markeby/Synth32/Schematics/3PoleStateVarVCF.kicad_sch

## KiCad design Schematics/3PoleStateVarVCF.kicad_sch (2024-06-07)

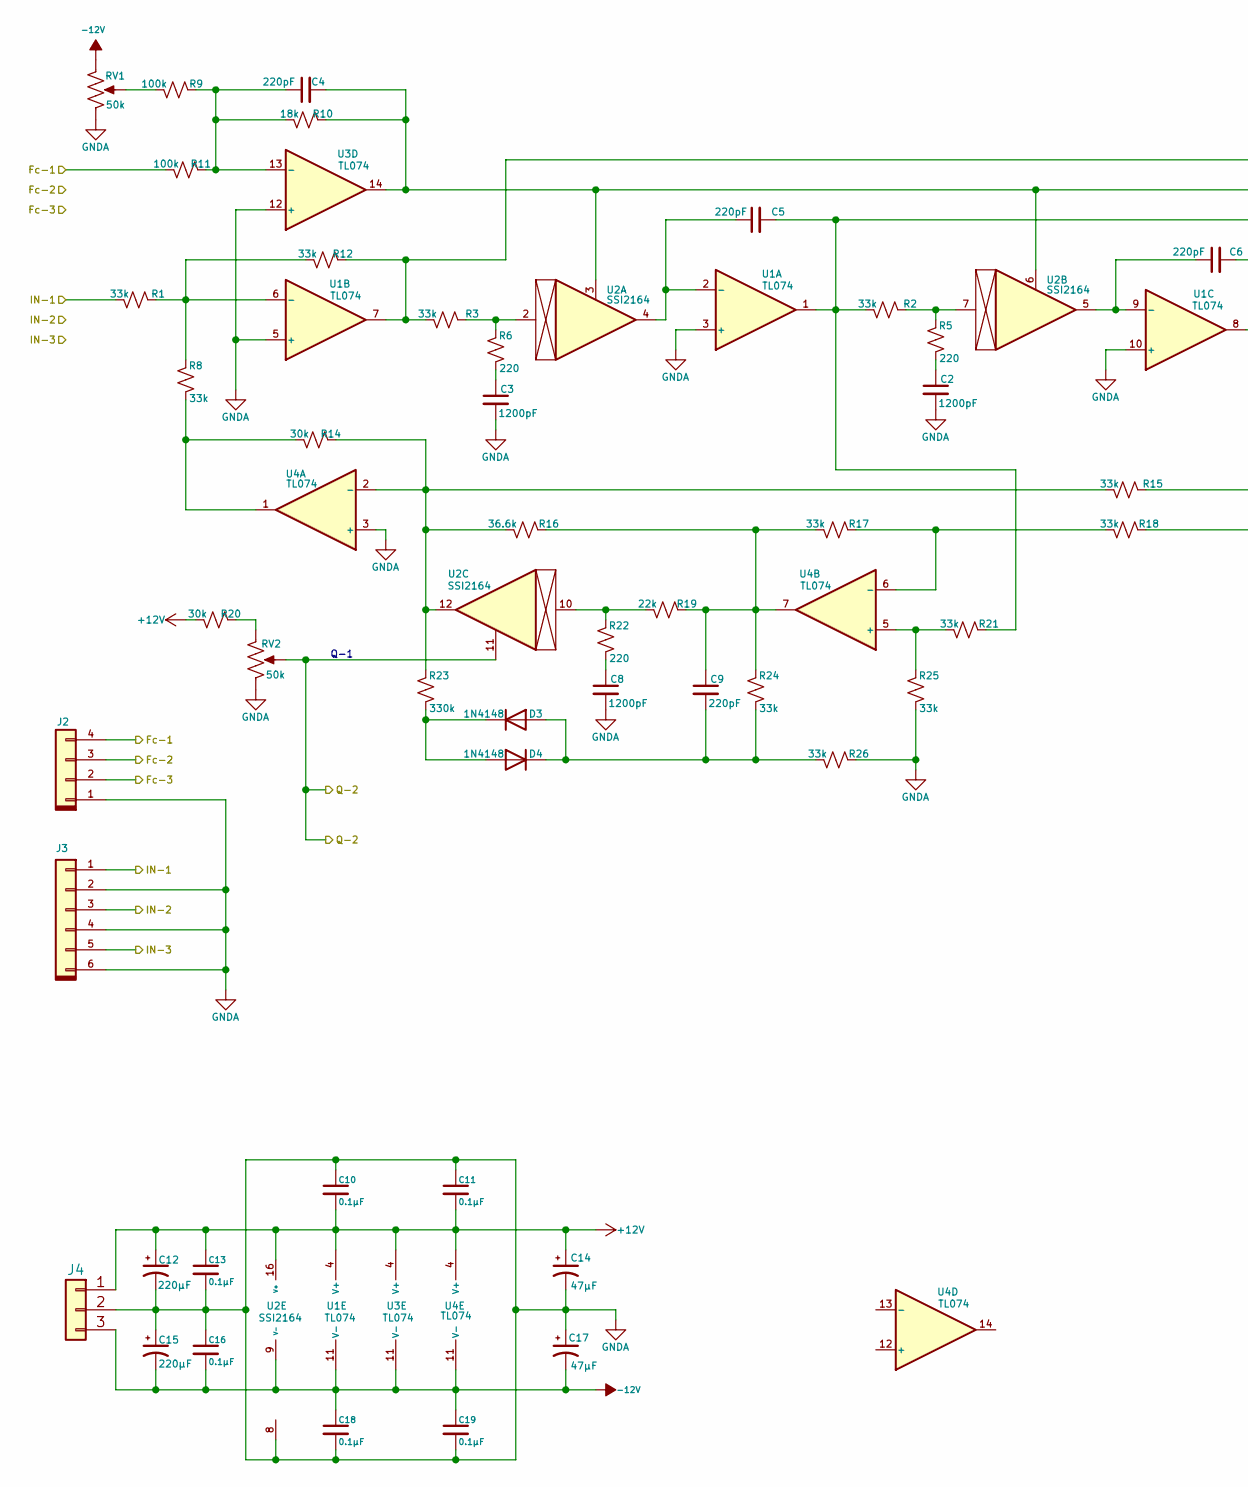
[picture p5: schematic 3PoleStateVarVCF.kicad_sch, part in row 1, column 1]

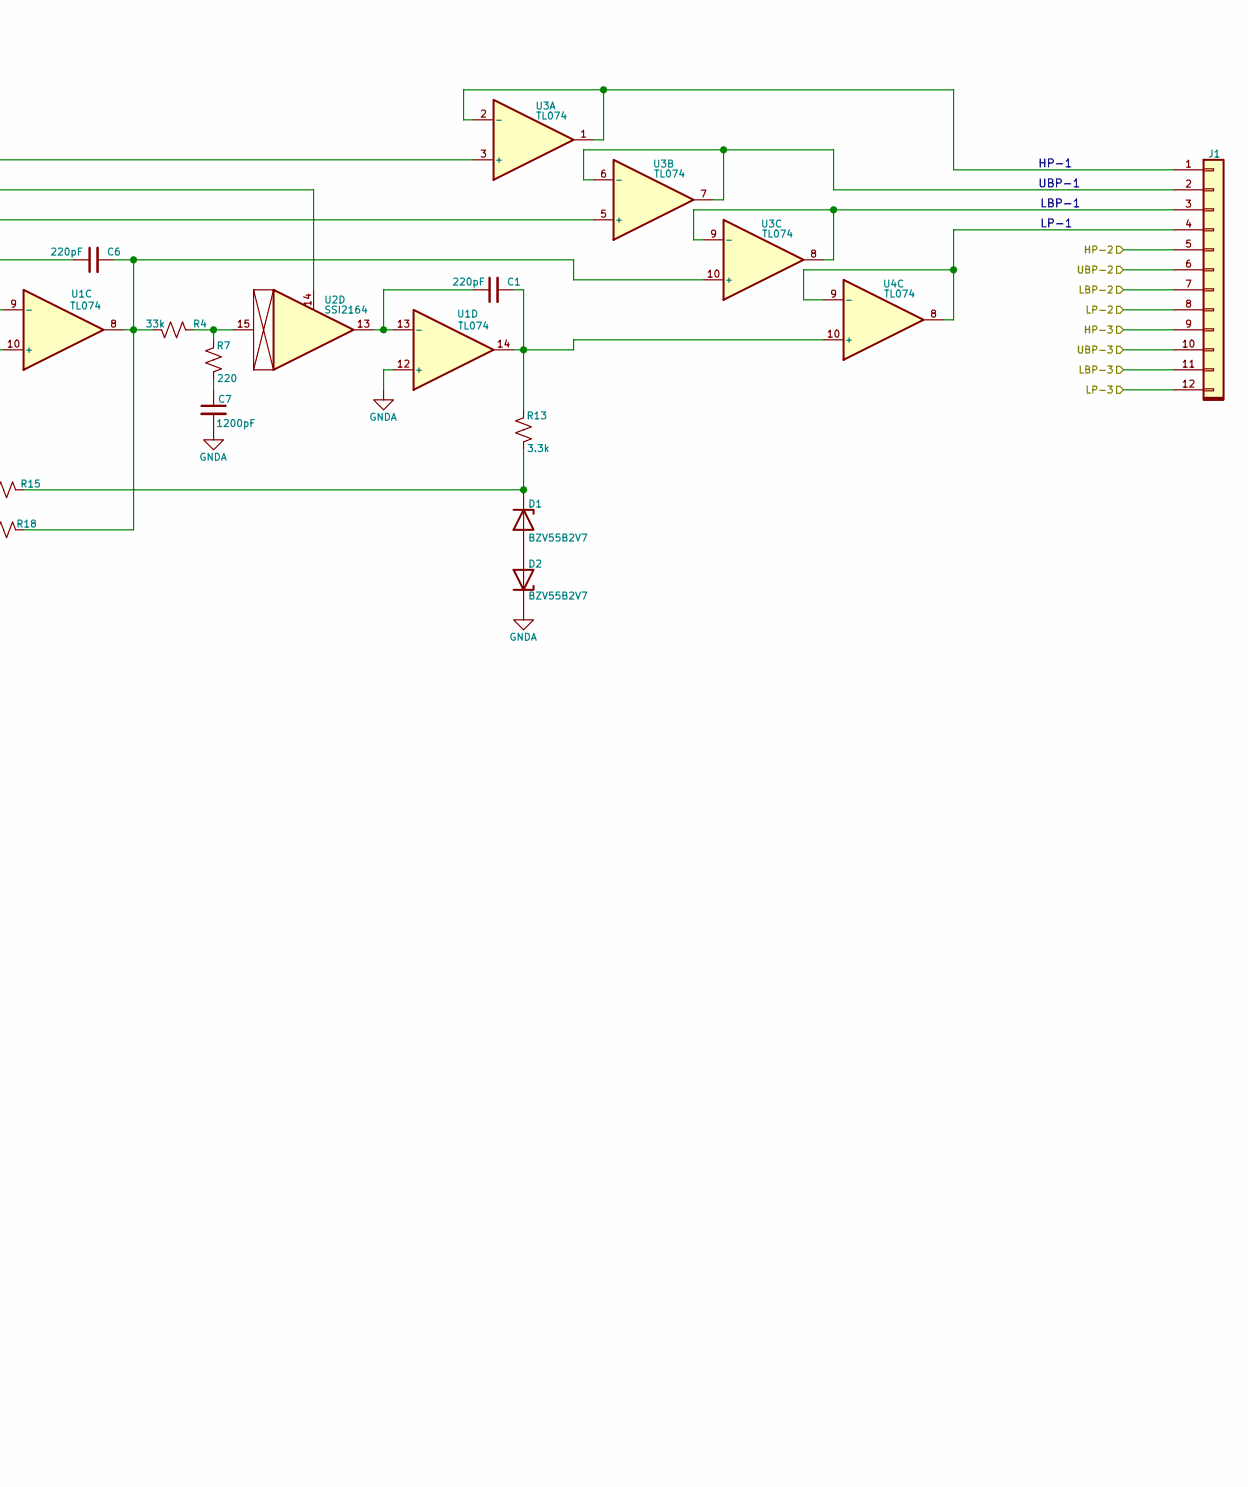
[picture p6: schematic 3PoleStateVarVCF.kicad_sch, part in row 1, column 2]

Parts:
C1, C4, C5, C6, C9: 220pF
C2, C3, C7, C8: 1200pF
C10, C11, C13, C16, C18, C19: 0.1µF
C12, C15: 220µF
C14, C17: 47µF
D1, D2: BZV55B2V7; D_MiniMELF
D3, D4: 1N4148; D_SOD-123
J1: Conn_01x12
J2: Conn_01x04
J3: Conn_01x06
J4: Conn_01x03
R1, R2, R3, R4, R8, R12, R15, R17, R18, R21, R24, R25, R26: 33k
R5, R6, R7, R22: 220
R9, R11: 100k
R10: 18k
R13: 3.3k
R14, R20: 30k
R16: 36.6k
R19: 22k
R23: 330k
RV1, RV2: 50k
U1, U3, U4: TL074
U2: SSI2164

Connections:
+12V: C10.2, C11.2, C12.1, C13.1, C14.1, J4.1, R20.2, U1.4 (V+), U2.16 (V+), U3.4 (V+), U4.4 (V+)
-12V: C15.2, C16.2, C17.2, C18.1, C19.1, J4.3, RV1., U1.11 (V-), U2.9 (V-), U3.11 (V-), U4.11 (V-)
Fc-1: J2.4, R11.2
Fc-2: J2.3
Fc-3: J2.2
GNDA: C2.2, C3.2, C7.2, C8.2, C10.1, C11.1, C12.2, C13.2, C14.2, C15.1, C16.1, C17.1, C18.2, C19.2, D2.1 (K), J2.1, J3.2, J3.4, J3.6, J4.2, R25.2, R26.1, RV1., RV2., U1.3 (+), U1.5 (+), U1.10 (+), U1.12 (+), U2.8, U3.12 (+), U4.3 (+)
HP-2: J1.5
HP-3: J1.9
IN-1: J3.1, R1.2
IN-2: J3.3
IN-3: J3.5
LBP-2: J1.7
LBP-3: J1.11
LP-2: J1.8
LP-3: J1.12
unnamed: C1.1, U1.13 (-), U2.13
unnamed: C1.2, R13.1, U1.14, U4.10 (+)
unnamed: C2.1, R5.2
unnamed: C3.1, R6.2
unnamed: C4.1, R9.1, R10.2, R11.1, U3.13 (-)
unnamed: C4.2, R10.1, U2.3, U2.6, U2.14, U3.14
unnamed: C5.1, U1.2 (-), U2.4
unnamed: C5.2, R2.2, R21.1, U1.1, U3.5 (+)
unnamed: C6.1, U1.9 (-), U2.5
unnamed: C6.2, R4.2, R18.1, U1.8, U3.10 (+)
unnamed: C7.1, R7.2
unnamed: C8.1, R22.2
unnamed: C9.1, R16.1, R17.2, R19.1, R24.1, U4.7
unnamed: C9.2, D3.2 (A), D4.1 (K), R24.2, R26.2
unnamed: D1.1 (K), R13.2, R15.1
unnamed: D1.2 (A), D2.2 (A)
unnamed: D3.1 (K), D4.2 (A), R23.2
unnamed: J1.1, U3.1, U3.2 (-)
unnamed: J1.2, U3.6 (-), U3.7
unnamed: J1.3, U3.8, U3.9 (-)
unnamed: J1.4, U4.8, U4.9 (-)
unnamed: R1.1, R8.1, R12.2, U1.6 (-)
unnamed: R2.1, R5.1, U2.7
unnamed: R3.1, R6.1, U2.2
unnamed: R4.1, R7.1, U2.15
unnamed: R9.2, RV1.
unnamed: R3.2, R12.1, U1.7, U3.3 (+)
unnamed: R14.1, R15.2, R16.2, R23.1, U2.12, U4.2 (-)
unnamed: R8.2, R14.2, U4.1
unnamed: R17.1, R18.2, U4.6 (-)
unnamed: R19.2, R22.1, U2.10
unnamed: R20.1, RV2.
unnamed: R21.2, R25.1, U4.5 (+)
Q-2: RV2., U2.11
UBP-2: J1.6
UBP-3: J1.10

Notes on the sheet:
LP-1
UBP-1
LBP-1
HP-1
Q-1
