markeby/Synth32/Schematics/Analog-1.kicad_sch

## KiCad design Schematics/Analog-1.kicad_sch (2024-10-31)

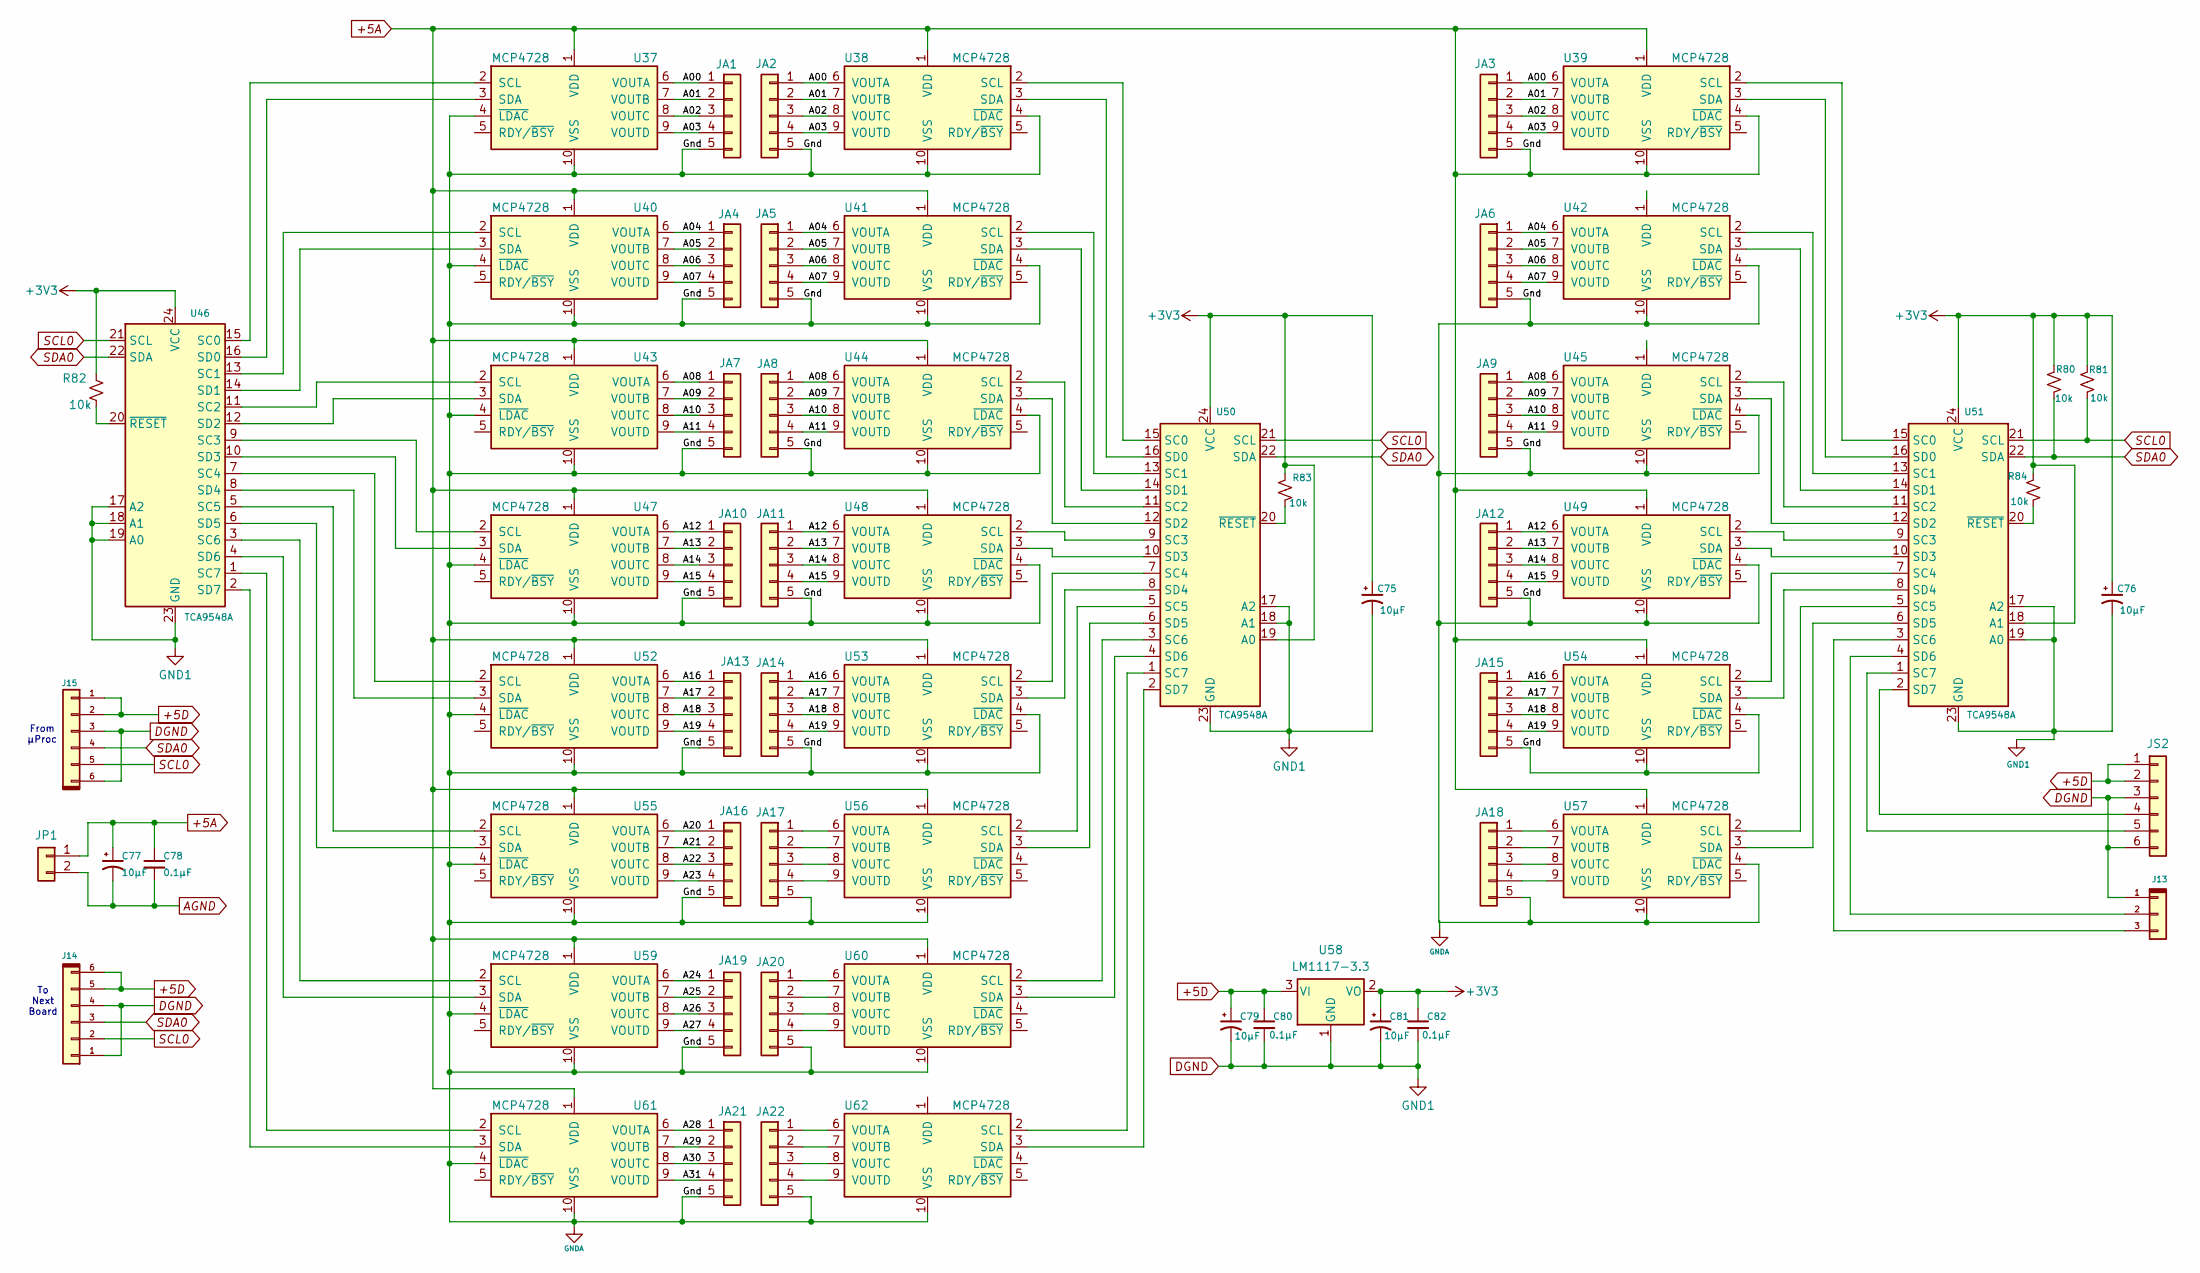
[picture p7: schematic Analog-1.kicad_sch]

Parts:
C75, C76, C77, C79, C81: 10µF
C78, C80, C82: 0.1µF
J13: Conn_01x03
J14, J15: Conn_01x06
JA1, JA2, JA3: DA00
JA4, JA5, JA6: DA04
JA7, JA8, JA9: DA08
JA10, JA11, JA12: DA12
JA13, JA14, JA15, JA17, JA18, JA20, JA22: DA16
JA16: DA20
JA19: DA24
JA21: DA38
JP1: From 12v Analog
JS2: To Compute #1
R80, R81, R82, R83, R84: 10k
U37, U38, U39, U40, U41, U42, U43, U44, U45, U47, U48, U49, U52, U53, U54, U55, U56, U57, U59, U60, U61, U62: MCP4728; MSOP-10_3x3mm_P0.5mm
U46, U50, U51: TCA9548A; SOIC-24W_7.5x15.4mm_P1.27mm
U58: LM1117-3.3

Connections:
+3V3: C75.1, C76.1, C81.1, C82.1, R80.1, R81.1, R82.1, R83.1, R84.1, U46.24 (VCC), U50.19 (A0), U50.24 (VCC), U51.18 (A1), U51.24 (VCC), U58.2 (VO)
+5A: C77.1, C78.1, JA1.5, JA2.5, JA3.5, JA4.5, JA5.5, JA6.5, JA7.5, JA8.5, JA9.5, JA10.5, JA11.5, JA12.5, JA13.5, JA14.5, JA15.5, JA16.5, JA17.5, JA18.5, JA19.5, JA20.5, JA21.5, JA22.5, JP1.1, U37.1 (VDD), U37.4 (~LDAC), U37.10 (VSS), U38.1 (VDD), U38.4 (~LDAC), U38.10 (VSS), U39.1 (VDD), U39.4 (~LDAC), U39.10 (VSS), U40.1 (VDD), U40.4 (~LDAC), U40.10 (VSS), U41.1 (VDD), U41.4 (~LDAC), U41.10 (VSS), U42.4 (~LDAC), U42.10 (VSS), U43.1 (VDD), U43.4 (~LDAC), U43.10 (VSS), U44.1 (VDD), U44.4 (~LDAC), U44.10 (VSS), U45.4 (~LDAC), U45.10 (VSS), U47.1 (VDD), U47.4 (~LDAC), U47.10 (VSS), U48.1 (VDD), U48.4 (~LDAC), U48.10 (VSS), U49.1 (VDD), U49.4 (~LDAC), U49.10 (VSS), U52.1 (VDD), U52.4 (~LDAC), U52.10 (VSS), U53.1 (VDD), U53.4 (~LDAC), U53.10 (VSS), U54.1 (VDD), U54.4 (~LDAC), U54.10 (VSS), U55.1 (VDD), U55.4 (~LDAC), U55.10 (VSS), U56.1 (VDD), U56.10 (VSS), U57.1 (VDD), U57.4 (~LDAC), U57.10 (VSS), U59.1 (VDD), U59.4 (~LDAC), U59.10 (VSS), U60.1 (VDD), U60.10 (VSS), U61.1 (VDD), U61.4 (~LDAC), U61.10 (VSS), U62.10 (VSS)
+5D: C79.1, C80.1, J14.5, J14.6, J15.1, J15.2, JS2.1, JS2.2, U58.3 (VI)
A00: JA1.1, JA2.1, JA3.1, U37.6 (VOUTA), U38.6 (VOUTA), U39.6 (VOUTA)
A01: JA1.2, JA2.2, JA3.2, U37.7 (VOUTB), U38.7 (VOUTB), U39.7 (VOUTB)
A02: JA1.3, JA2.3, JA3.3, U37.8 (VOUTC), U38.8 (VOUTC), U39.8 (VOUTC)
A03: JA1.4, JA2.4, JA3.4, U37.9 (VOUTD), U38.9 (VOUTD), U39.9 (VOUTD)
A04: JA4.1, JA5.1, JA6.1, U40.6 (VOUTA), U41.6 (VOUTA), U42.6 (VOUTA)
A05: JA4.2, JA5.2, JA6.2, U40.7 (VOUTB), U41.7 (VOUTB), U42.7 (VOUTB)
A06: JA4.3, JA5.3, JA6.3, U40.8 (VOUTC), U41.8 (VOUTC), U42.8 (VOUTC)
A07: JA4.4, JA5.4, JA6.4, U40.9 (VOUTD), U41.9 (VOUTD), U42.9 (VOUTD)
A08: JA7.1, JA8.1, JA9.1, U43.6 (VOUTA), U44.6 (VOUTA), U45.6 (VOUTA)
A09: JA7.2, JA8.2, JA9.2, U43.7 (VOUTB), U44.7 (VOUTB), U45.7 (VOUTB)
A10: JA7.3, JA8.3, JA9.3, U43.8 (VOUTC), U44.8 (VOUTC), U45.8 (VOUTC)
A11: JA7.4, JA8.4, JA9.4, U43.9 (VOUTD), U44.9 (VOUTD), U45.9 (VOUTD)
A12: JA10.1, JA11.1, JA12.1, U47.6 (VOUTA), U48.6 (VOUTA), U49.6 (VOUTA)
A13: JA10.2, JA11.2, JA12.2, U47.7 (VOUTB), U48.7 (VOUTB), U49.7 (VOUTB)
A14: JA10.3, JA11.3, JA12.3, U47.8 (VOUTC), U48.8 (VOUTC), U49.8 (VOUTC)
A15: JA10.4, JA11.4, JA12.4, U47.9 (VOUTD), U48.9 (VOUTD), U49.9 (VOUTD)
A16: JA13.1, JA14.1, JA15.1, U52.6 (VOUTA), U53.6 (VOUTA), U54.6 (VOUTA)
A17: JA13.2, JA14.2, JA15.2, U52.7 (VOUTB), U53.7 (VOUTB), U54.7 (VOUTB)
A18: JA13.3, JA14.3, JA15.3, U52.8 (VOUTC), U53.8 (VOUTC), U54.8 (VOUTC)
A19: JA13.4, JA14.4, JA15.4, U52.9 (VOUTD), U53.9 (VOUTD), U54.9 (VOUTD)
A20: JA16.1, U55.6 (VOUTA)
A21: JA16.2, U55.7 (VOUTB)
A22: JA16.3, U55.8 (VOUTC)
A23: JA16.4, U55.9 (VOUTD)
A24: JA19.1, U59.6 (VOUTA)
A25: JA19.2, U59.7 (VOUTB)
A26: JA19.3, U59.8 (VOUTC)
A27: JA19.4, U59.9 (VOUTD)
A28: JA21.1, U61.6 (VOUTA)
A29: JA21.2, U61.7 (VOUTB)
A30: JA21.3, U61.8 (VOUTC)
A31: JA21.4, U61.9 (VOUTD)
AGND: C77.2, C78.2, JP1.2
DGND: C75.2, C76.2, C79.2, C80.2, C81.2, C82.2, J13.1, J14.1, J14.4, J15.3, J15.6, JS2.3, JS2.6, U46.17 (A2), U46.18 (A1), U46.19 (A0), U46.23 (GND), U50.17 (A2), U50.18 (A1), U50.23 (GND), U51.17 (A2), U51.19 (A0), U51.23 (GND), U58.1 (GND)
unnamed: J13.2, U51.4 (SD6)
unnamed: J13.3, U51.3 (SC6)
unnamed: JA17.1, U56.6 (VOUTA)
unnamed: JA17.2, U56.7 (VOUTB)
unnamed: JA17.3, U56.8 (VOUTC)
unnamed: JA17.4, U56.9 (VOUTD)
unnamed: JA18.1, U57.6 (VOUTA)
unnamed: JA18.2, U57.7 (VOUTB)
unnamed: JA18.3, U57.8 (VOUTC)
unnamed: JA18.4, U57.9 (VOUTD)
unnamed: JA20.1, U60.6 (VOUTA)
unnamed: JA20.2, U60.7 (VOUTB)
unnamed: JA20.3, U60.8 (VOUTC)
unnamed: JA20.4, U60.9 (VOUTD)
unnamed: JA22.1, U62.6 (VOUTA)
unnamed: JA22.2, U62.7 (VOUTB)
unnamed: JA22.3, U62.8 (VOUTC)
unnamed: JA22.4, U62.9 (VOUTD)
unnamed: JS2.4, U51.2 (SD7)
unnamed: JS2.5, U51.1 (SC7)
unnamed: R82.2, U46.20 (~RESET)
unnamed: R83.2, U50.20 (~RESET)
unnamed: R84.2, U51.20 (~RESET)
unnamed: U37.2 (SCL), U46.15 (SC0)
unnamed: U37.3 (SDA), U46.16 (SD0)
unnamed: U38.2 (SCL), U50.15 (SC0)
unnamed: U38.3 (SDA), U50.16 (SD0)
unnamed: U39.2 (SCL), U51.15 (SC0)
unnamed: U39.3 (SDA), U51.16 (SD0)
unnamed: U40.2 (SCL), U46.13 (SC1)
unnamed: U40.3 (SDA), U46.14 (SD1)
unnamed: U41.2 (SCL), U50.13 (SC1)
unnamed: U41.3 (SDA), U50.14 (SD1)
unnamed: U42.2 (SCL), U51.13 (SC1)
unnamed: U42.3 (SDA), U51.14 (SD1)
unnamed: U43.2 (SCL), U46.11 (SC2)
unnamed: U43.3 (SDA), U46.12 (SD2)
unnamed: U44.2 (SCL), U50.11 (SC2)
unnamed: U44.3 (SDA), U50.12 (SD2)
unnamed: U45.2 (SCL), U51.11 (SC2)
unnamed: U45.3 (SDA), U51.12 (SD2)
unnamed: U46.1 (SC7), U61.2 (SCL)
unnamed: U46.2 (SD7), U61.3 (SDA)
unnamed: U46.3 (SC6), U59.2 (SCL)
unnamed: U46.4 (SD6), U59.3 (SDA)
unnamed: U46.5 (SC5), U55.2 (SCL)
unnamed: U46.6 (SD5), U55.3 (SDA)
unnamed: U46.7 (SC4), U52.2 (SCL)
unnamed: U46.8 (SD4), U52.3 (SDA)
unnamed: U46.9 (SC3), U47.2 (SCL)
unnamed: U46.10 (SD3), U47.3 (SDA)
unnamed: U48.2 (SCL), U50.9 (SC3)
unnamed: U48.3 (SDA), U50.10 (SD3)
unnamed: U49.2 (SCL), U51.9 (SC3)
unnamed: U49.3 (SDA), U51.10 (SD3)
unnamed: U50.1 (SC7), U62.2 (SCL)
unnamed: U50.2 (SD7), U62.3 (SDA)
unnamed: U50.3 (SC6), U60.2 (SCL)
unnamed: U50.4 (SD6), U60.3 (SDA)
unnamed: U50.5 (SC5), U56.2 (SCL)
unnamed: U50.6 (SD5), U56.3 (SDA)
unnamed: U50.7 (SC4), U53.2 (SCL)
unnamed: U50.8 (SD4), U53.3 (SDA)
unnamed: U51.5 (SC5), U57.2 (SCL)
unnamed: U51.6 (SD5), U57.3 (SDA)
unnamed: U51.7 (SC4), U54.2 (SCL)
unnamed: U51.8 (SD4), U54.3 (SDA)
SCL0: J14.2, J15.5, R81.2, U46.21 (SCL), U50.21 (SCL), U51.21 (SCL)
SDA0: J14.3, J15.4, R80.2, U46.22 (SDA), U50.22 (SDA), U51.22 (SDA)

Notes on the sheet:
From µProc
To Next Board
