markeby/Synth32/Schematics/DigitalOptical.kicad_sch

## KiCad design Schematics/DigitalOptical.kicad_sch (2024-11-26)

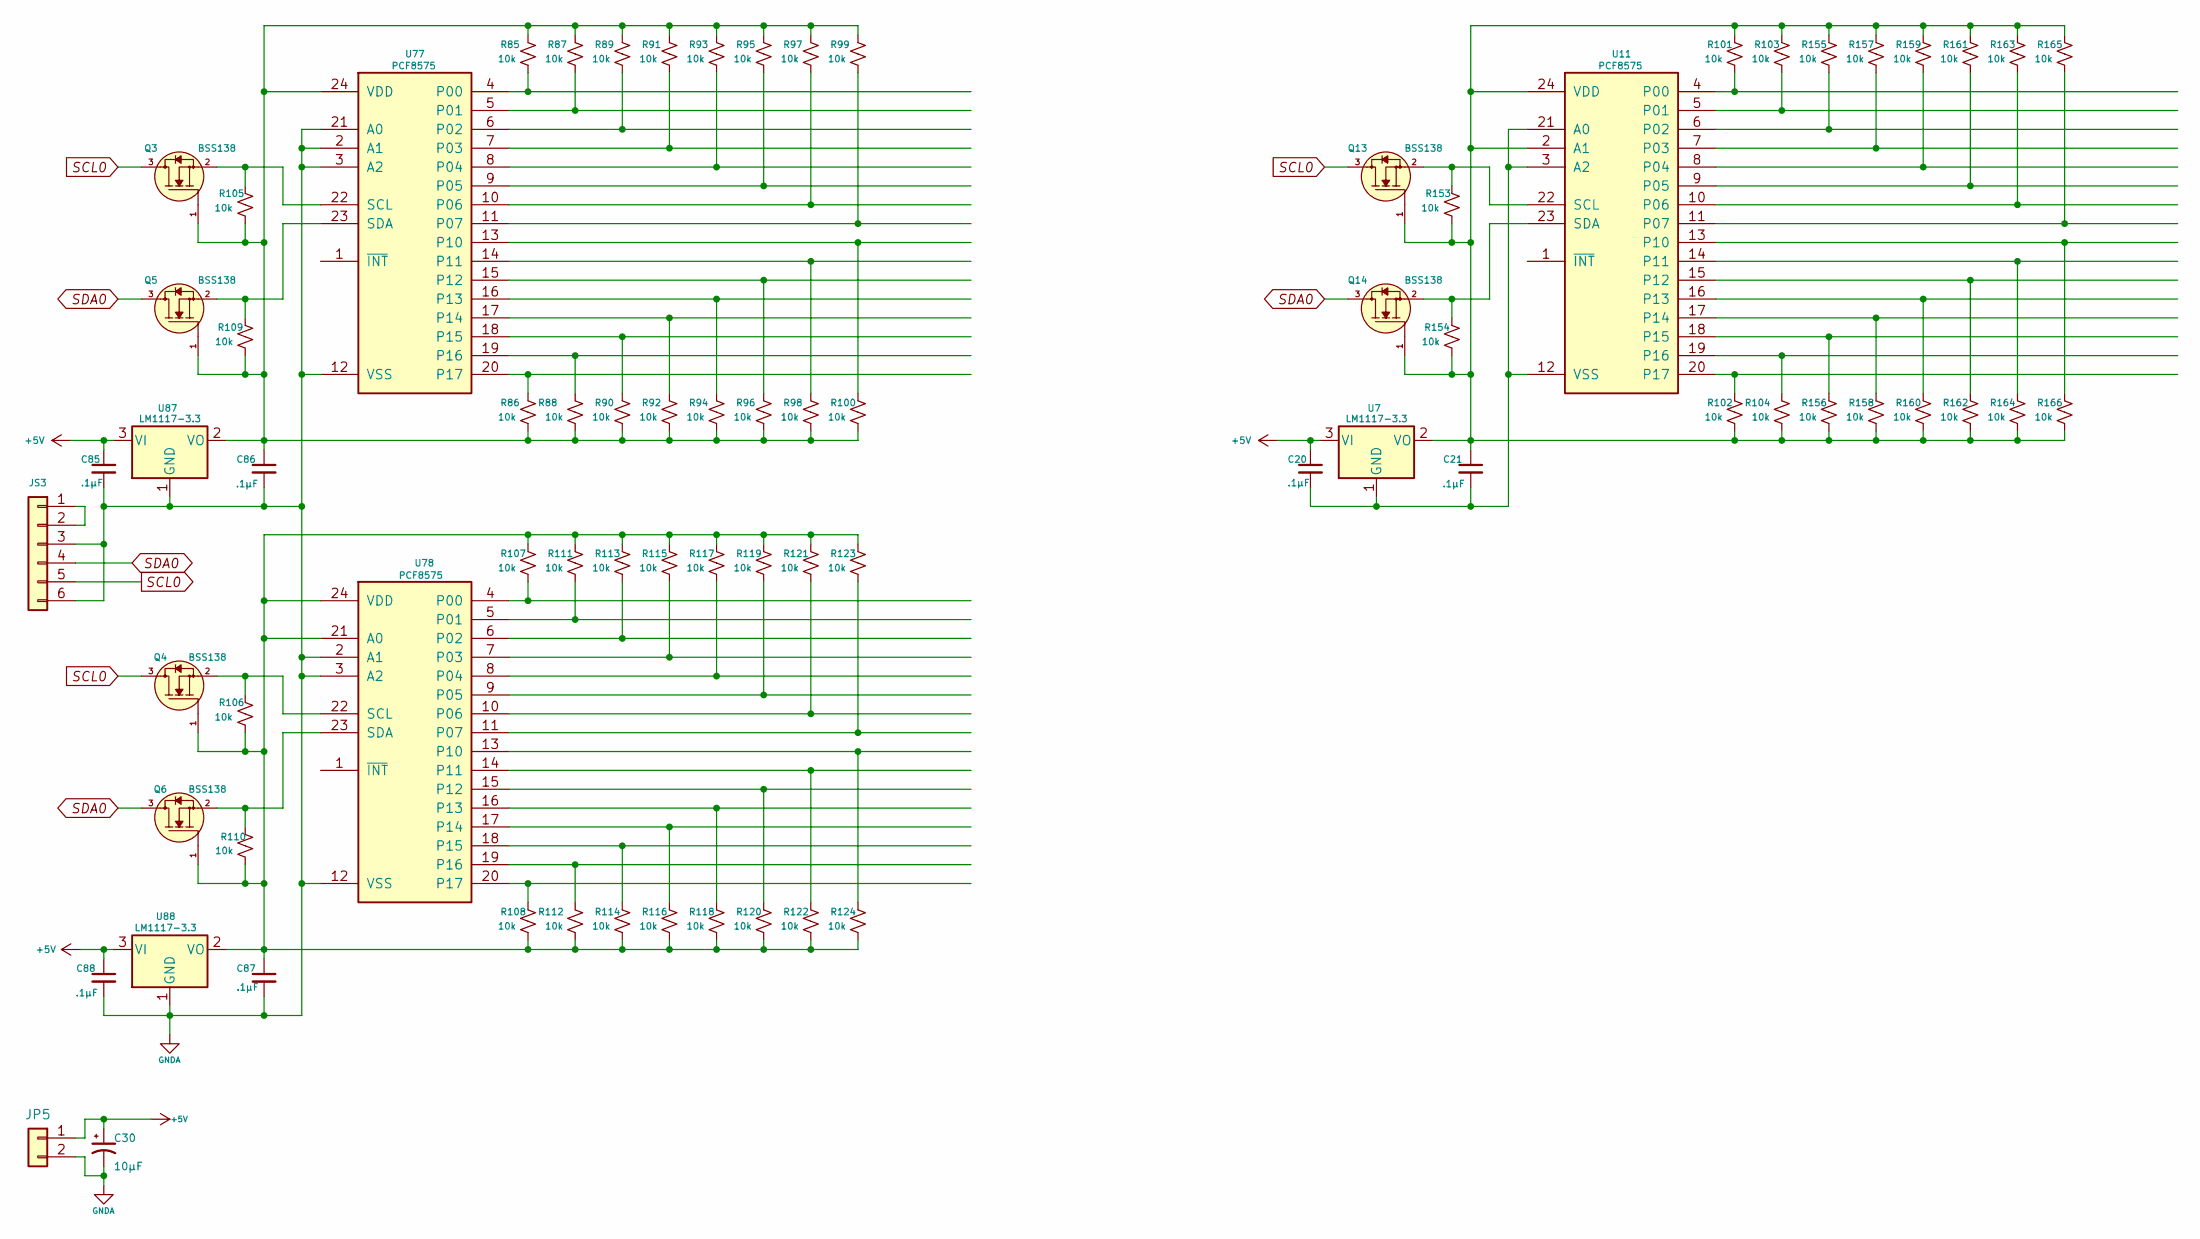
[picture p8: schematic DigitalOptical.kicad_sch]

Parts:
C20, C21, C85, C86, C87, C88: .1µF
C30: 10µF
JP5: From 12v Analog
JS3: To Compute #1
Q3, Q4, Q5, Q6, Q13, Q14: BSS138; SOT-23-3; MPN BSS138; Digi-Key_PN BSS138CT-ND
R85, R86, R87, R88, R89, R90, R91, R92, R93, R94, R95, R96, R97, R98, R99, R100, R101, R102, R103, R104, R105, R106, R107, R108, R109, R110, R111, R112, R113, R114, R115, R116, R117, R118, R119, R120, R121, R122, R123, R124, R153, R154, R155, R156, R157, R158, R159, R160, R161, R162, R163, R164, R165, R166: 10k
U7, U87, U88: LM1117-3.3
U11, U77, U78: PCF8575; SOP65P775X200-24; MPN PCF8575TS/1,112

Connections:
+5V: C20.1, C30.1, C85.1, C88.1, JP5.1, U7.3 (VI), U87.3 (VI), U88.3 (VI)
GNDA: C30.2, C85.2, C86.2, C87.2, C88.2, JP5.2, JS3.3, JS3.6, U77.2 (A1), U77.3 (A2), U77.12 (VSS), U77.21 (A0), U78.2 (A1), U78.3 (A2), U78.12 (VSS), U87.1 (GND), U88.1 (GND)
unnamed: C20.2, C21.2, U7.1 (GND), U11.3 (A2), U11.12 (VSS), U11.21 (A0)
unnamed: C21.1, Q13.1, Q14.1, R101.1, R102.2, R103.1, R104.2, R153.2, R154.2, R155.1, R156.2, R157.1, R158.2, R159.1, R160.2, R161.1, R162.2, R163.1, R164.2, R165.1, R166.2, U7.2 (VO), U11.2 (A1), U11.24 (VDD)
unnamed: C86.1, Q3.1, Q5.1, R85.1, R86.2, R87.1, R88.2, R89.1, R90.2, R91.1, R92.2, R93.1, R94.2, R95.1, R96.2, R97.1, R98.2, R99.1, R100.2, R105.2, R109.2, U77.24 (VDD), U87.2 (VO)
unnamed: C87.1, Q4.1, Q6.1, R106.2, R107.1, R108.2, R110.2, R111.1, R112.2, R113.1, R114.2, R115.1, R116.2, R117.1, R118.2, R119.1, R120.2, R121.1, R122.2, R123.1, R124.2, U78.21 (A0), U78.24 (VDD), U88.2 (VO)
unnamed: JS3.1, JS3.2
unnamed: Q3.2, R105.1, U77.22 (SCL)
unnamed: Q4.2, R106.1, U78.22 (SCL)
unnamed: Q5.2, R109.1, U77.23 (SDA)
unnamed: Q6.2, R110.1, U78.23 (SDA)
unnamed: Q13.2, R153.1, U11.22 (SCL)
unnamed: Q14.2, R154.1, U11.23 (SDA)
unnamed: R85.2, U77.4 (P00)
unnamed: R86.1, U77.20 (P17)
unnamed: R87.2, U77.5 (P01)
unnamed: R88.1, U77.19 (P16)
unnamed: R89.2, U77.6 (P02)
unnamed: R90.1, U77.18 (P15)
unnamed: R91.2, U77.7 (P03)
unnamed: R92.1, U77.17 (P14)
unnamed: R93.2, U77.8 (P04)
unnamed: R94.1, U77.16 (P13)
unnamed: R95.2, U77.9 (P05)
unnamed: R96.1, U77.15 (P12)
unnamed: R97.2, U77.10 (P06)
unnamed: R98.1, U77.14 (P11)
unnamed: R99.2, U77.11 (P07)
unnamed: R100.1, U77.13 (P10)
unnamed: R101.2, U11.4 (P00)
unnamed: R102.1, U11.20 (P17)
unnamed: R103.2, U11.5 (P01)
unnamed: R104.1, U11.19 (P16)
unnamed: R107.2, U78.4 (P00)
unnamed: R108.1, U78.20 (P17)
unnamed: R111.2, U78.5 (P01)
unnamed: R112.1, U78.19 (P16)
unnamed: R113.2, U78.6 (P02)
unnamed: R114.1, U78.18 (P15)
unnamed: R115.2, U78.7 (P03)
unnamed: R116.1, U78.17 (P14)
unnamed: R117.2, U78.8 (P04)
unnamed: R118.1, U78.16 (P13)
unnamed: R119.2, U78.9 (P05)
unnamed: R120.1, U78.15 (P12)
unnamed: R121.2, U78.10 (P06)
unnamed: R122.1, U78.14 (P11)
unnamed: R123.2, U78.11 (P07)
unnamed: R124.1, U78.13 (P10)
unnamed: R155.2, U11.6 (P02)
unnamed: R156.1, U11.18 (P15)
unnamed: R157.2, U11.7 (P03)
unnamed: R158.1, U11.17 (P14)
unnamed: R159.2, U11.8 (P04)
unnamed: R160.1, U11.16 (P13)
unnamed: R161.2, U11.9 (P05)
unnamed: R162.1, U11.15 (P12)
unnamed: R163.2, U11.10 (P06)
unnamed: R164.1, U11.14 (P11)
unnamed: R165.2, U11.11 (P07)
unnamed: R166.1, U11.13 (P10)
SCL0: JS3.5, Q3.3, Q4.3, Q13.3
SDA0: JS3.4, Q5.3, Q6.3, Q14.3
