markeby/Synth32/Schematics/Digitial-1.kicad_sch

## KiCad design Schematics/Digitial-1.kicad_sch (2024-08-03)

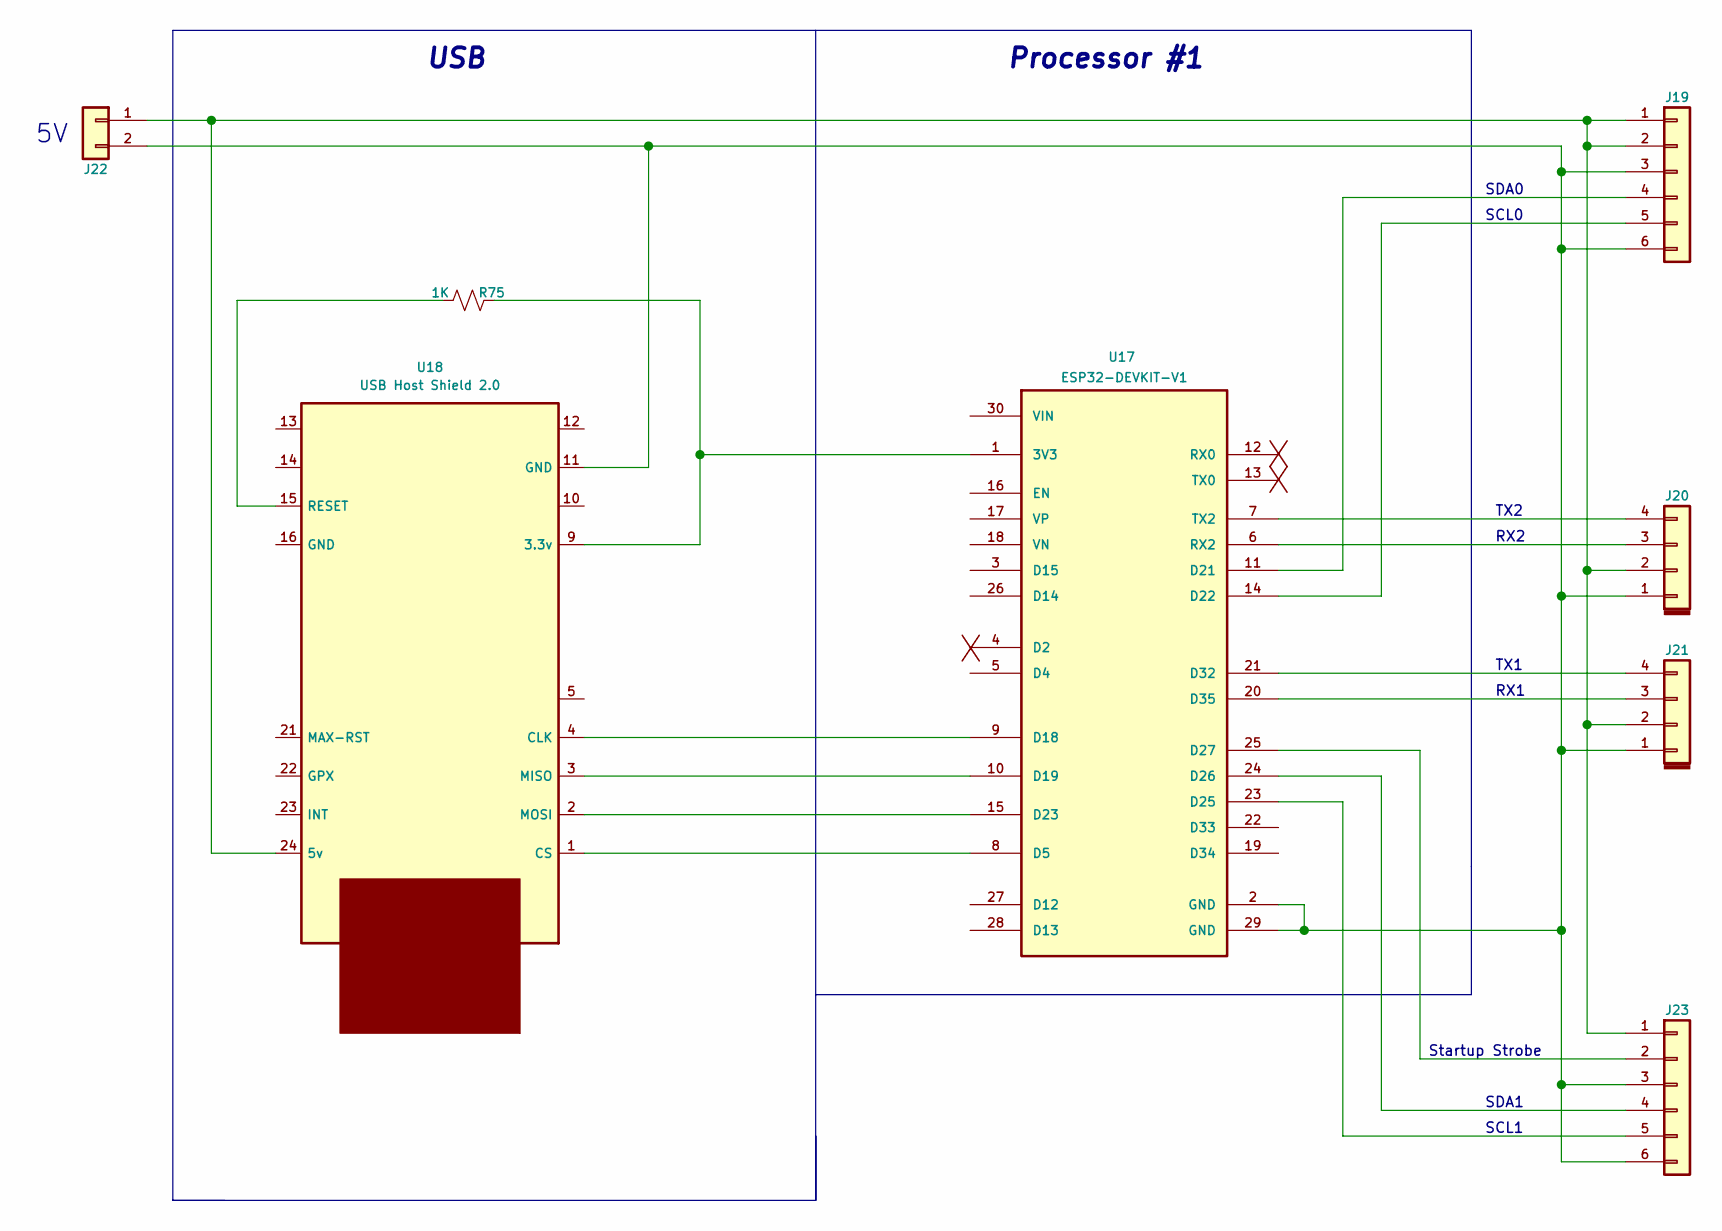
[picture p9: schematic Digitial-1.kicad_sch]

Parts:
J19, J23: To Compute #1
J20, J21: Conn_01x04
J22: Conn_01x02
R75: 1K
U17: ESP32-DEVKIT-V1
U18: USB Host Shield 2.0

Connections:
unnamed: J19.1, J19.2, J20.2, J21.2, J22.1, J23.1, U18.24 (5v)
unnamed: J19.3, J19.6, J20.1, J21.1, J22.2, J23.3, J23.6, U17.2 (GND), U17.29 (GND), U18.11 (GND)
unnamed: J19.4, U17.11 (D21)
unnamed: J19.5, U17.14 (D22)
unnamed: J20.3, U17.6 (RX2)
unnamed: J20.4, U17.7 (TX2)
unnamed: J21.3, U17.20 (D35)
unnamed: J21.4, U17.21 (D32)
unnamed: J23.2, U17.25 (D27)
unnamed: J23.4, U17.24 (D26)
unnamed: J23.5, U17.23 (D25)
unnamed: R75.1, U17.1 (3V3), U18.9 (3.3v)
unnamed: R75.2, U18.15 (RESET)
unnamed: U17.8 (D5), U18.1 (CS)
unnamed: U17.9 (D18), U18.4 (CLK)
unnamed: U17.10 (D19), U18.3 (MISO)
unnamed: U17.15 (D23), U18.2 (MOSI)

Notes on the sheet:
RX1
Processor #1
RX2
SDA1
Startup Strobe
TX2
TX1
SCL0
USB
SDA0
SCL1
