markeby/Synth32/Schematics/LFO-1.kicad_sch

## KiCad design Schematics/LFO-1.kicad_sch (2024-07-26)

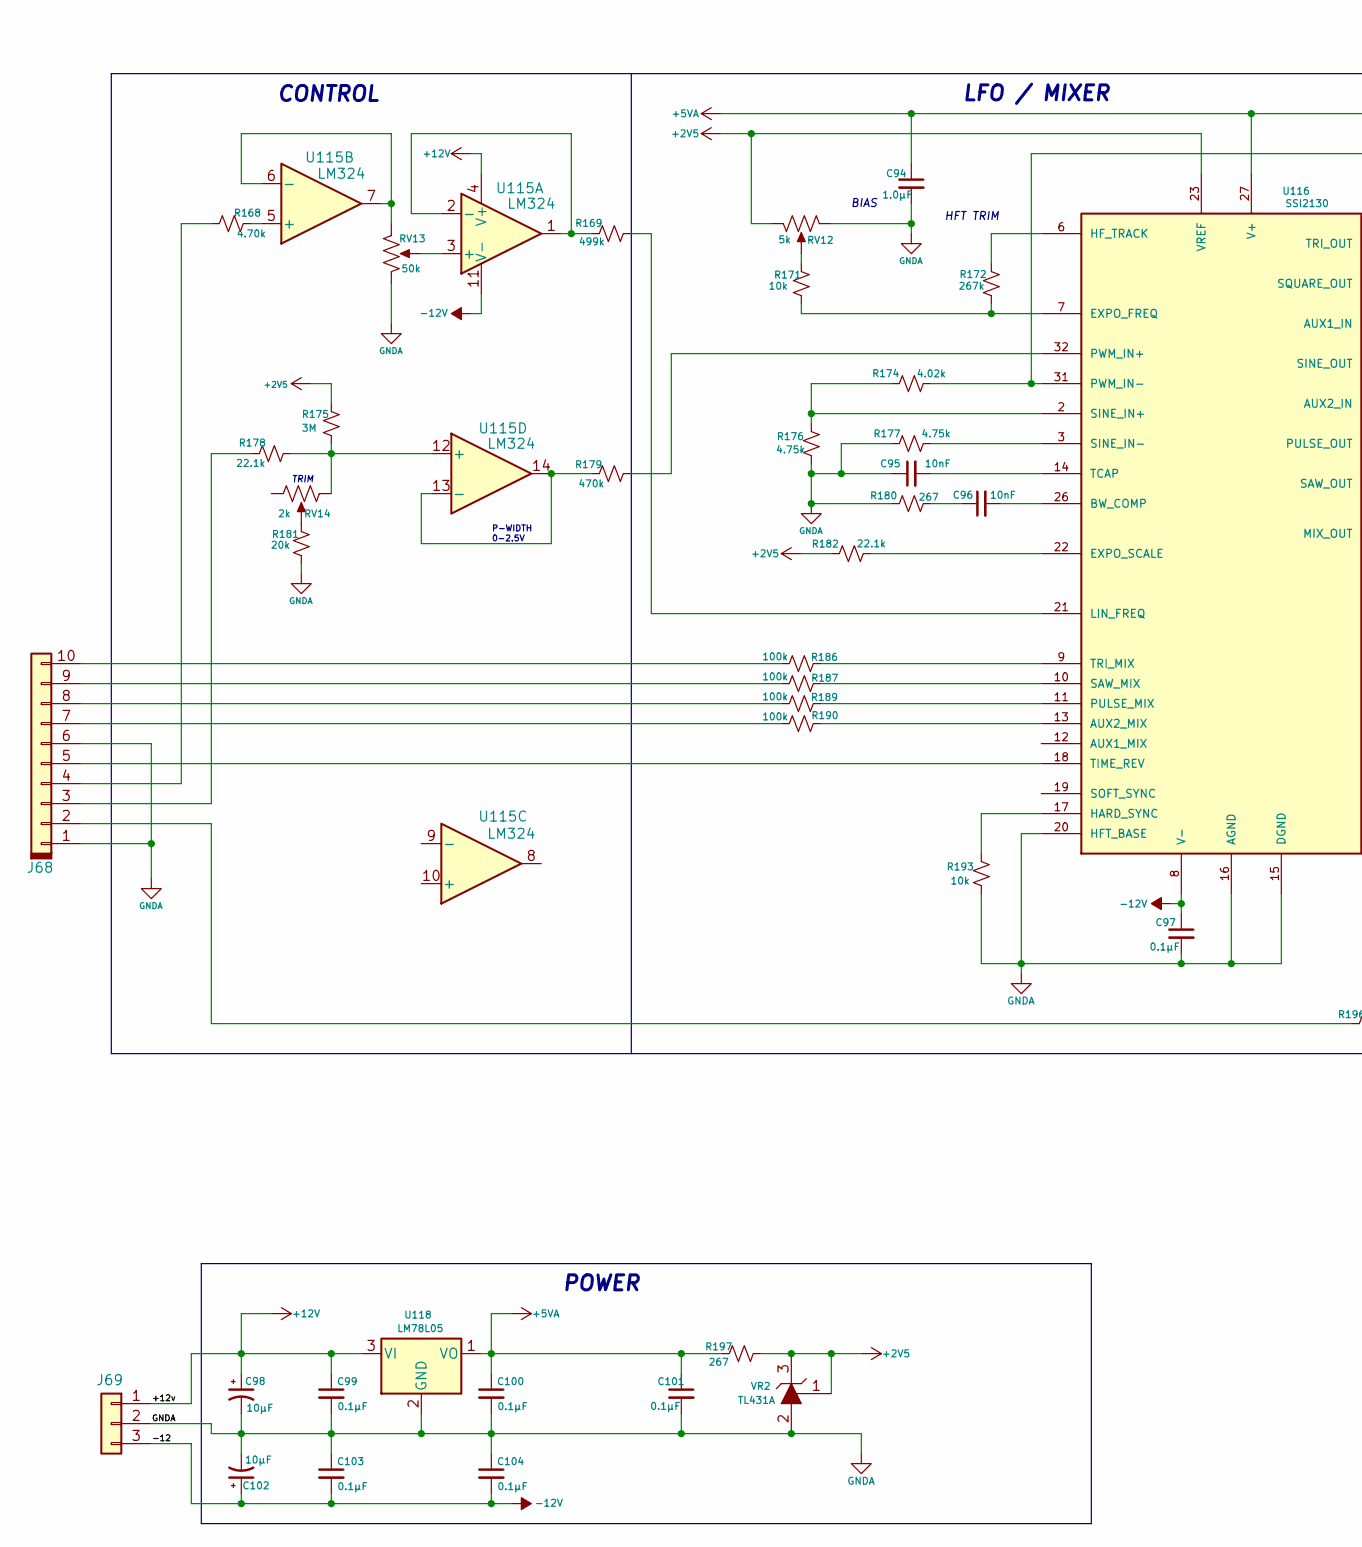
[picture p10: schematic LFO-1.kicad_sch, part in row 1, column 1]

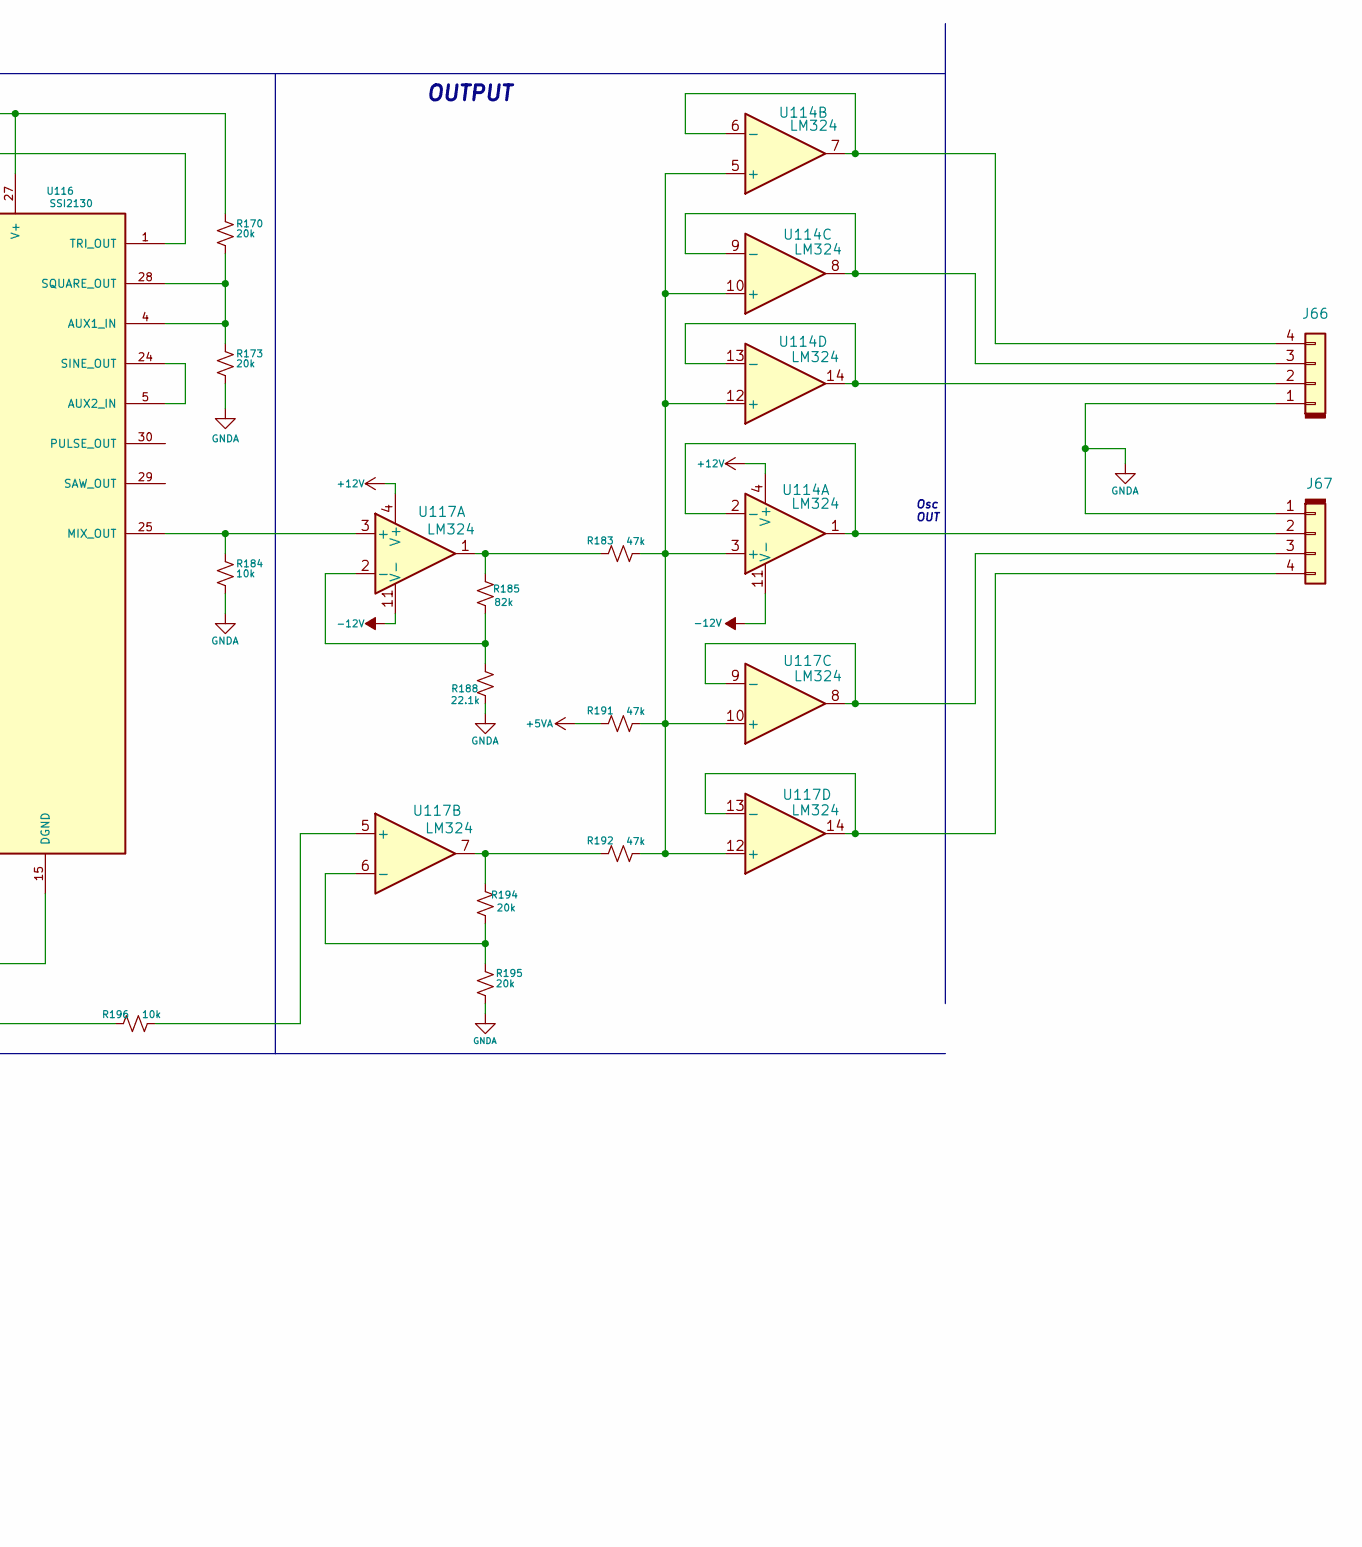
[picture p11: schematic LFO-1.kicad_sch, part in row 1, column 2]

Parts:
C94: 1.0µF
C95, C96: 10nF
C97, C99, C100, C101, C103, C104: 0.1µF
C98, C102: 10µF
J66, J67: Conn_01x04
J68: Conn_01x10h
J69: Conn_01x03
R168: 4.70k
R169: 499k
R170, R173, R181, R194, R195: 20k
R171, R184, R193, R196: 10k
R172: 267k
R174: 4.02k
R175: 3M
R176, R177: 4.75k
R178, R182, R188: 22.1k
R179: 470k
R180, R197: 267
R183, R191, R192: 47k
R185: 82k
R186, R187, R189, R190: 100k
RV12: 5k
RV13: 50k
RV14: 2k
U114, U115, U117: LM324
U116: SSI2130; QFN40P400X400X90-33N; PARTREV Rev. 2.4
U118: LM78L05; TO-92_Inline
VR2: TL431A; TO-92-3_Formed_Leads; MPN TL431CLPM; Digi-Key_PN 296-26717-1-ND

Connections:
+2V5: R175.1, R182.1, R197.2, RV12., U116.23 (VREF), VR2.1 (REF), VR2.3 (K)
+5VA: C94.1, C100.1, C101.1, R170.1, R191.1, R197.1, U116.27 (V+), U118.1 (VO)
+12v: C98.1, C99.1, J69.1, U114.4 (V+), U115.4 (V+), U117.4 (V+), U118.3 (VI)
-12V: C97.1, C102.1, C103.2, C104.2, J69.3, U114.11 (V-), U115.11 (V-), U116.8 (V-), U117.11 (V-)
GNDA: C94.2, C95.1, C97.2, C98.2, C99.2, C100.2, C101.2, C102.2, C103.1, C104.1, J66.1, J67.1, J68.1, J68.6, J69.2, R173.2, R176.2, R177.1, R180.1, R181.2, R184.2, R188.2, R193.2, R195.2, RV12., RV13., U116.15 (DGND), U116.16 (AGND), U116.20 (HFT_BASE), U118.2 (GND), VR2.2 (A)
unnamed: C95.2, U116.14 (TCAP)
unnamed: C96.1, R180.2
unnamed: C96.2, U116.26 (BW_COMP)
unnamed: J66.2, U114.13 (-), U114.14
unnamed: J66.3, U114.8, U114.9 (-)
unnamed: J66.4, U114.6 (-), U114.7
unnamed: J67.2, U114.1, U114.2 (-)
unnamed: J67.3, U117.8, U117.9 (-)
unnamed: J67.4, U117.13 (-), U117.14
unnamed: J68.2, R196.1
unnamed: J68.3, R178.1
unnamed: J68.4, R168.1
unnamed: J68.5, U116.18 (TIME_REV)
unnamed: J68.7, R190.1
unnamed: J68.8, R189.1
unnamed: J68.9, R187.1
unnamed: J68.10, R186.1
unnamed: R168.2, U115.5 (+)
unnamed: R169.1, U115.1, U115.2 (-)
unnamed: R169.2, U116.21 (LIN_FREQ)
unnamed: R170.2, R173.1, U116.4 (AUX1_IN), U116.28 (SQUARE_OUT)
unnamed: R171.1, RV12.
unnamed: R171.2, R172.2, U116.7 (EXPO_FREQ)
unnamed: R172.1, U116.6 (HF_TRACK)
unnamed: R174.1, R176.1, U116.2 (SINE_IN+)
unnamed: R174.2, U116.1 (TRI_OUT), U116.31 (PWM_IN-)
unnamed: R175.2, R178.2, RV14., U115.12 (+)
unnamed: R177.2, U116.3 (SINE_IN-)
unnamed: R179.1, U115.13 (-), U115.14
unnamed: R179.2, U116.32 (PWM_IN+)
unnamed: R181.1, RV14.
unnamed: R182.2, U116.22 (EXPO_SCALE)
unnamed: R183.1, R185.1, U117.1
unnamed: R183.2, R191.2, R192.2, U114.3 (+), U114.5 (+), U114.10 (+), U114.12 (+), U117.10 (+), U117.12 (+)
unnamed: R184.1, U116.25 (MIX_OUT), U117.3 (+)
unnamed: R185.2, R188.1, U117.2 (-)
unnamed: R186.2, U116.9 (TRI_MIX)
unnamed: R187.2, U116.10 (SAW_MIX)
unnamed: R189.2, U116.11 (PULSE_MIX)
unnamed: R190.2, U116.13 (AUX2_MIX)
unnamed: R192.1, R194.2, U117.7
unnamed: R193.1, U116.17 (HARD_SYNC)
unnamed: R194.1, R195.1, U117.6 (-)
unnamed: R196.2, U117.5 (+)
unnamed: RV13., U115.3 (+), U115.6 (-), U115.7
unnamed: U116.5 (AUX2_IN), U116.24 (SINE_OUT)

Notes on the sheet:
Osc OUT
_{HFT TRIM}
LFO / MIXER
CONTROL
_{TRIM}
0-2.5V
_{BIAS}
P-WIDTH
POWER
OUTPUT
