markeby/Synth32/Schematics/Mixer1.kicad_sch

## KiCad design Schematics/Mixer1.kicad_sch (2024-10-31)

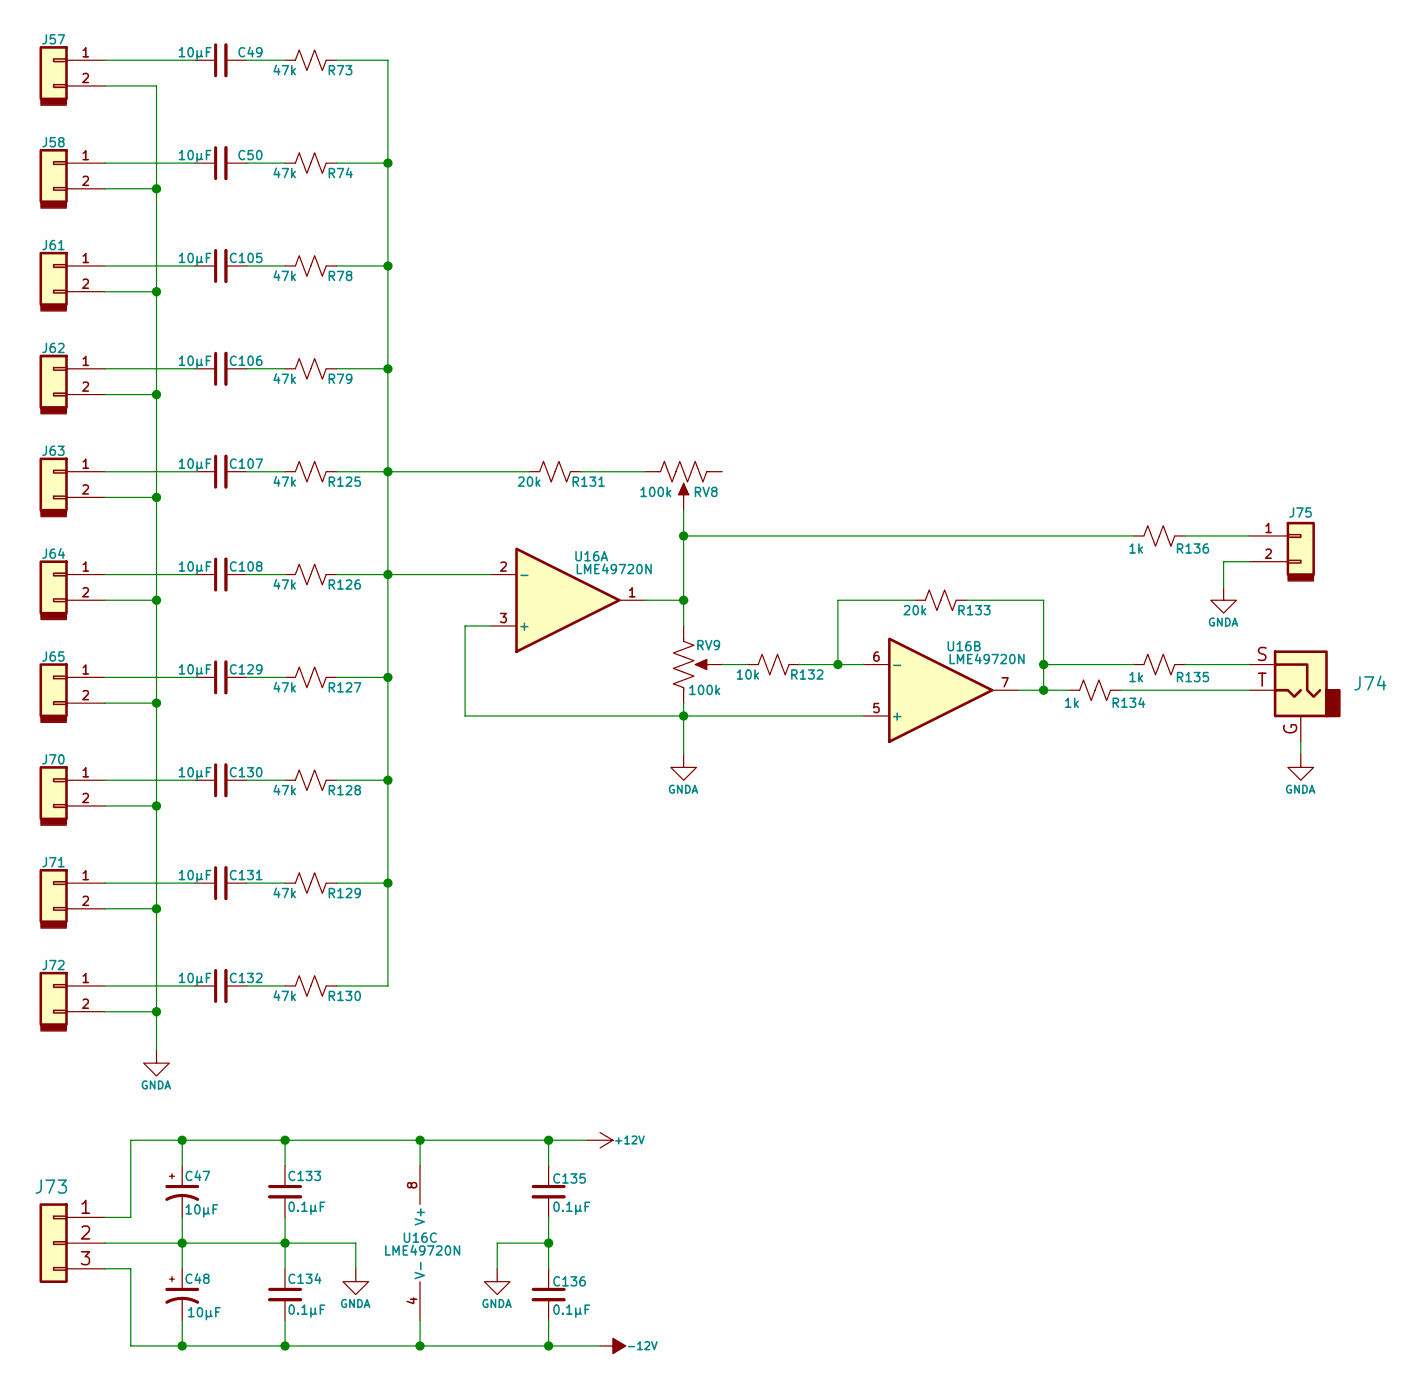
[picture p12: schematic Mixer1.kicad_sch]

Parts:
C47, C48, C49, C50, C105, C106, C107, C108, C129, C130, C131, C132: 10µF
C133, C134, C135, C136: 0.1µF
J57, J58, J61, J62, J63, J64, J65, J70, J71, J72, J75: Conn_01x02
J73: Conn_01x03
J74: AudioJack2_Ground
R73, R74, R78, R79, R125, R126, R127, R128, R129, R130: 47k
R131, R133: 20k
R132: 10k
R134, R135, R136: 1k
RV8, RV9: 100k
U16: LME49720N

Connections:
+12V: C47.1, C133.1, C135.1, J73.1, U16.8 (V+)
-12V: C48.2, C134.2, C136.2, J73.3, U16.4 (V-)
GNDA: C47.2, C48.1, C133.2, C134.1, C135.2, C136.1, J57.2, J58.2, J61.2, J62.2, J63.2, J64.2, J65.2, J70.2, J71.2, J72.2, J73.2, J74.G, J75.2, RV9., U16.3 (+), U16.5 (+)
unnamed: C49.1, J57.1
unnamed: C49.2, R73.1
unnamed: C50.1, J58.1
unnamed: C50.2, R74.1
unnamed: C105.1, J61.1
unnamed: C105.2, R78.1
unnamed: C106.1, J62.1
unnamed: C106.2, R79.1
unnamed: C107.1, J63.1
unnamed: C107.2, R125.1
unnamed: C108.1, J64.1
unnamed: C108.2, R126.1
unnamed: C129.1, J65.1
unnamed: C129.2, R127.1
unnamed: C130.1, J70.1
unnamed: C130.2, R128.1
unnamed: C131.1, J71.1
unnamed: C131.2, R129.1
unnamed: C132.1, J72.1
unnamed: C132.2, R130.1
unnamed: J74.S, R135.2
unnamed: J74.T, R134.2
unnamed: J75.1, R136.2
unnamed: R73.2, R74.2, R78.2, R79.2, R125.2, R126.2, R127.2, R128.2, R129.2, R130.2, R131.1, U16.2 (-)
unnamed: R131.2, RV8.
unnamed: R132.1, RV9.
unnamed: R132.2, R133.1, U16.6 (-)
unnamed: R133.2, R134.1, R135.1, U16.7
unnamed: R136.1, RV8., RV9., U16.1
