markeby/Synth32/Schematics/Multiplexer.kicad_sch

## KiCad design Schematics/Multiplexer.kicad_sch (2024-11-26)

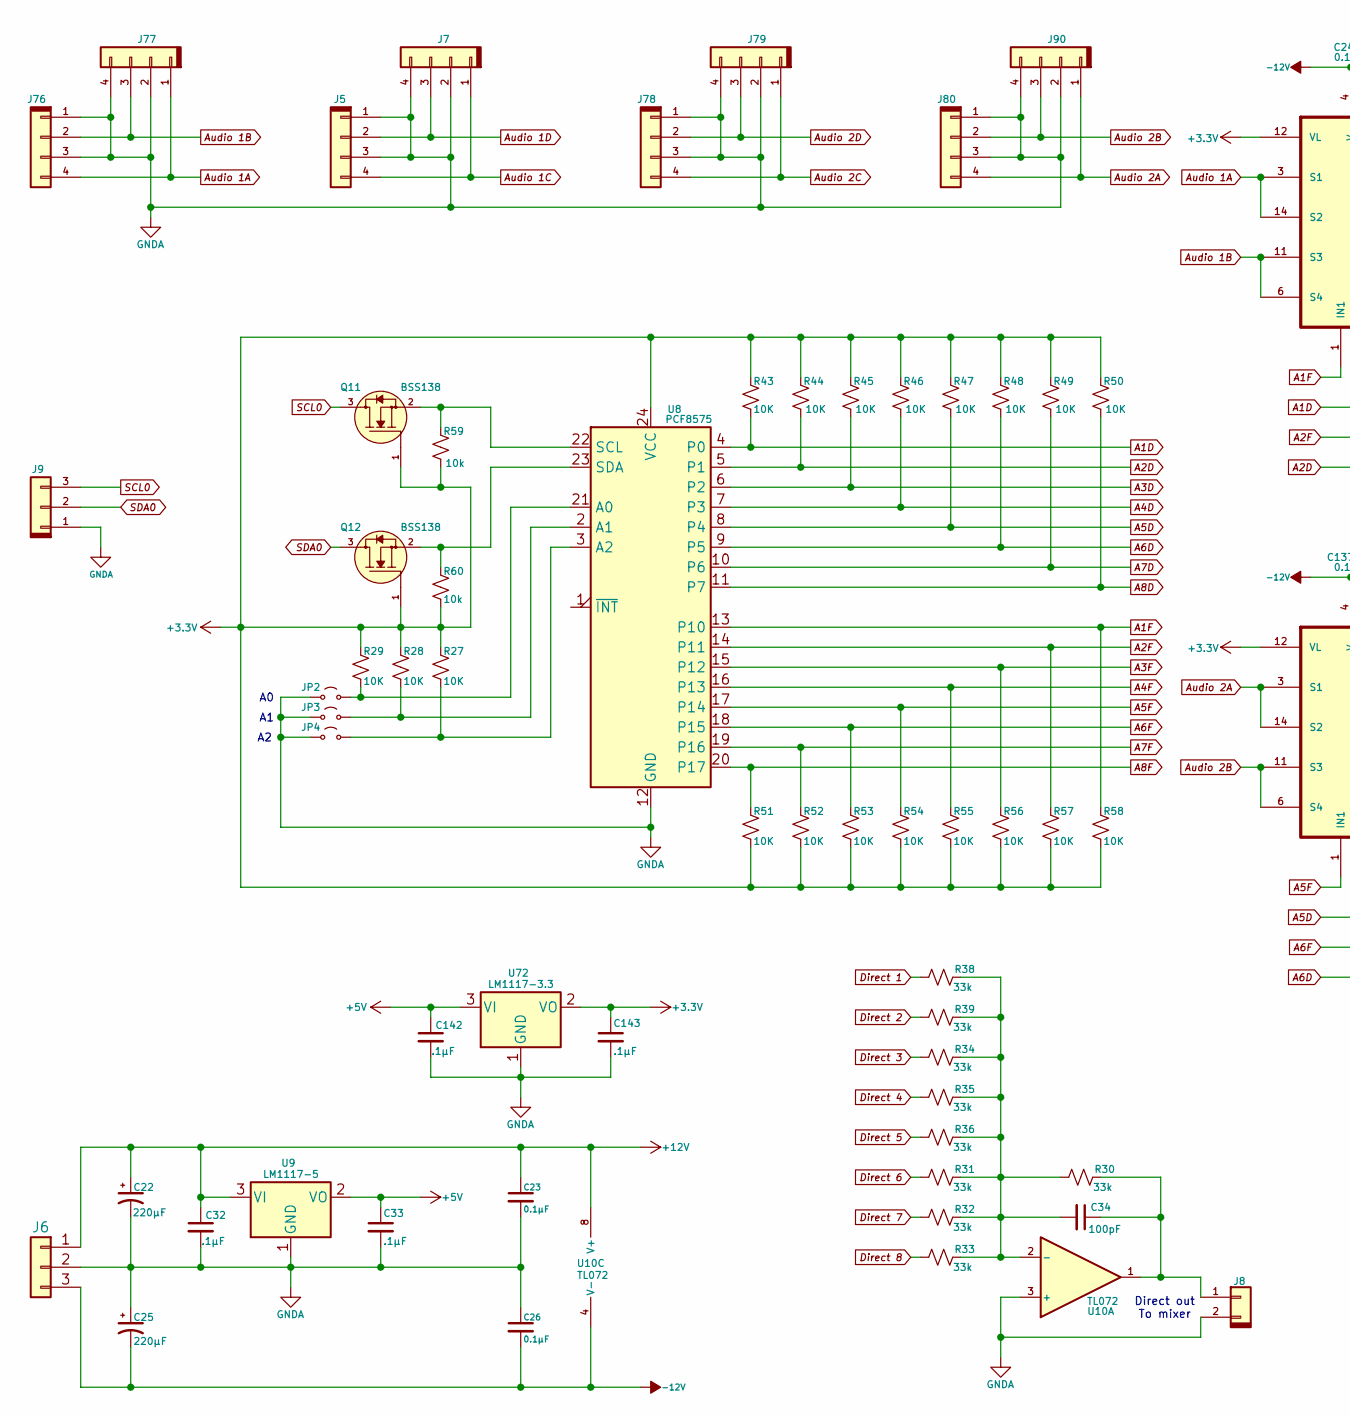
[picture p13: schematic Multiplexer.kicad_sch, part in row 1, column 1]

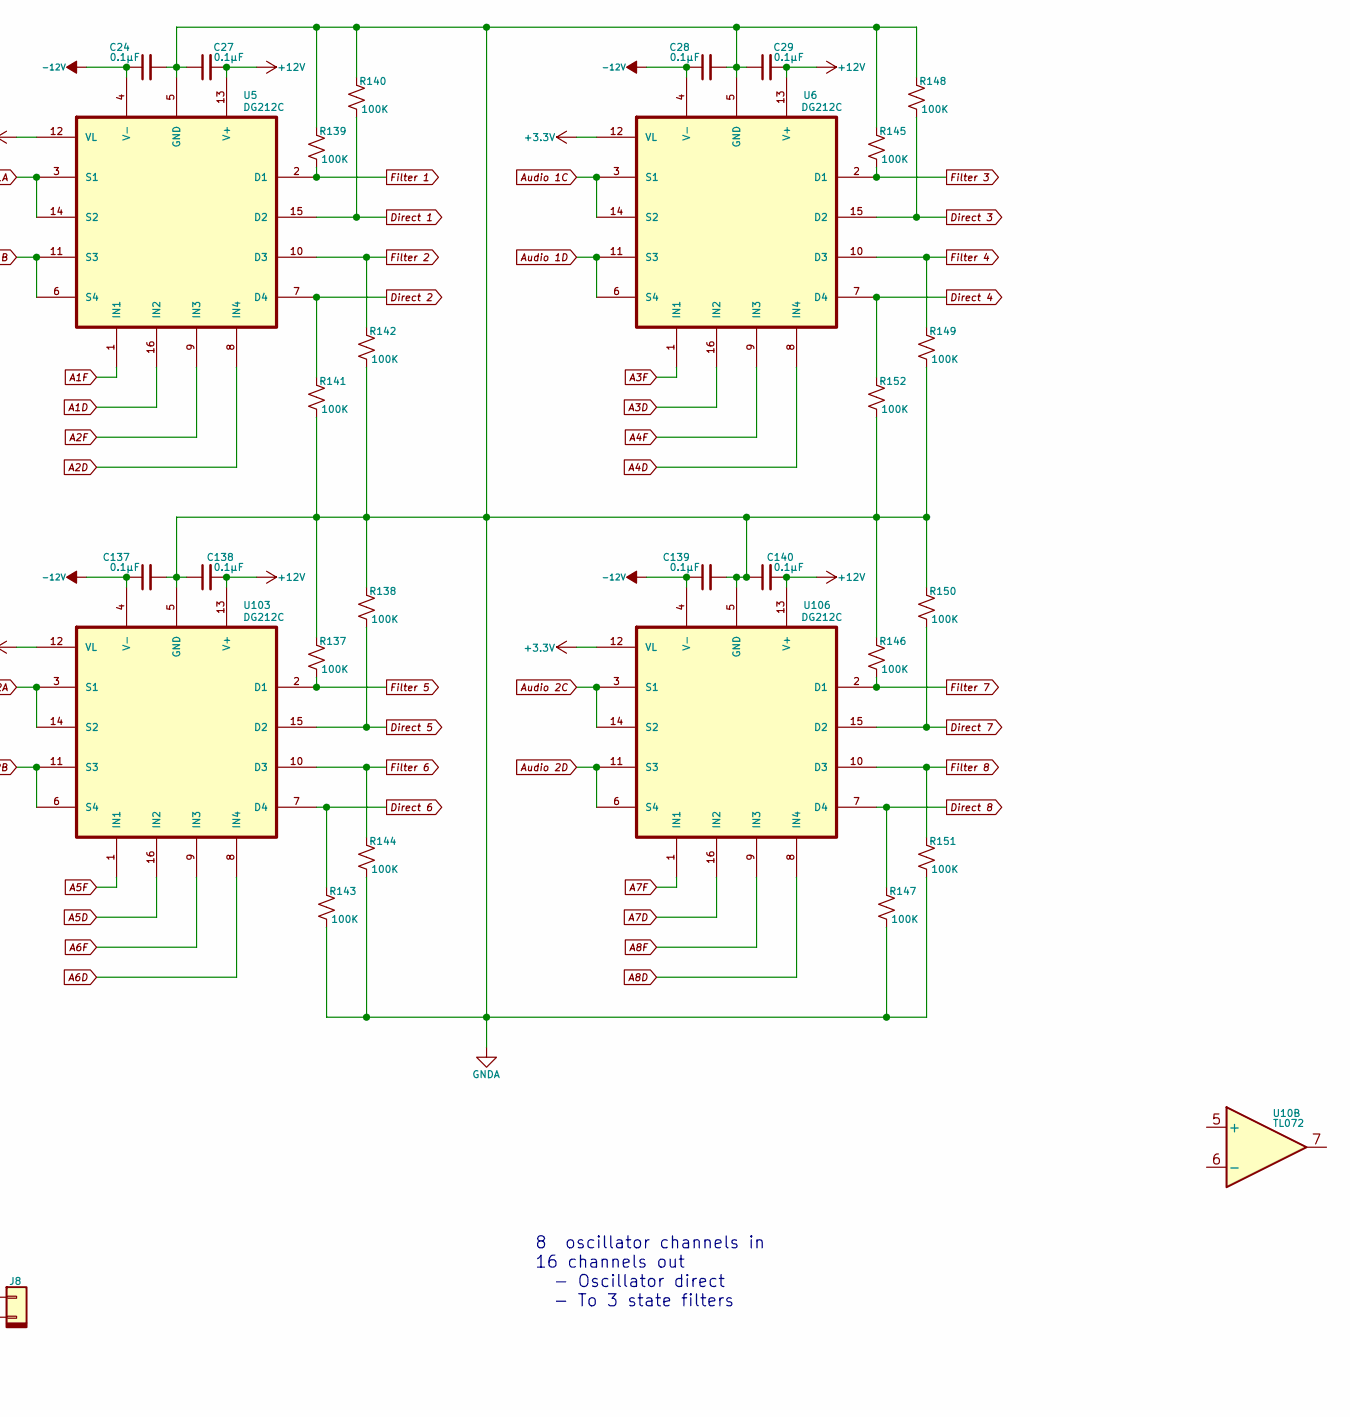
[picture p14: schematic Multiplexer.kicad_sch, part in row 1, column 2]

Parts:
C22, C25: 220µF
C23, C24, C26, C27, C28, C29, C137, C138, C139, C140: 0.1µF
C32, C33, C142, C143: .1µF
C34: 100pF
J5, J7, J76, J77, J78, J79, J80, J90: Conn_01x04
J6, J9: Conn_01x03
J8: Conn_01x02
JP2, JP3, JP4: Jumper_2_Small_Open
Q11, Q12: BSS138; SOT-23-3; MPN BSS138; Digi-Key_PN BSS138CT-ND
R27, R28, R29, R43, R44, R45, R46, R47, R48, R49, R50, R51, R52, R53, R54, R55, R56, R57, R58: 10K
R30, R31, R32, R33, R34, R35, R36, R38, R39: 33k
R59, R60: 10k
R137, R138, R139, R140, R141, R142, R143, R144, R145, R146, R147, R148, R149, R150, R151, R152: 100K
U5, U6, U103, U106: DG212C
U8: PCF8575; SSOP-24_5.3x8.2mm_P0.65mm
U9: LM1117-5
U10: TL072
U72: LM1117-3.3

Connections:
+3.3V: C143.1, Q11.1, Q12.1, R27.1, R28.1, R29.1, R43.1, R44.1, R45.1, R46.1, R47.1, R48.1, R49.1, R50.1, R51.2, R52.2, R53.2, R54.2, R55.2, R56.2, R57.2, R58.2, R59.2, R60.2, U5.12 (VL), U6.12 (VL), U8.24 (VCC), U72.2 (VO), U103.12 (VL), U106.12 (VL)
+5V: C33.1, C142.1, U9.2 (VO), U72.3 (VI)
+12V: C22.1, C23.1, C27.2, C29.2, C32.1, C138.2, C140.2, J6.1, U5.13 (V+), U6.13 (V+), U9.3 (VI), U10.8 (V+), U103.13 (V+), U106.13 (V+)
-12V: C24.1, C25.2, C26.2, C28.1, C137.1, C139.1, J6.3, U5.4 (V-), U6.4 (V-), U10.4 (V-), U103.4 (V-), U106.4 (V-)
A1D: R43.2, U5.16 (IN2), U8.4 (P0)
A1F: R58.1, U5.1 (IN1), U8.13 (P10)
A2D: R44.2, U5.8 (IN4), U8.5 (P1)
A2F: R57.1, U5.9 (IN3), U8.14 (P11)
A3D: R45.2, U6.16 (IN2), U8.6 (P2)
A3F: R56.1, U6.1 (IN1), U8.15 (P12)
A4D: R46.2, U6.8 (IN4), U8.7 (P3)
A4F: R55.1, U6.9 (IN3), U8.16 (P13)
A5D: R47.2, U8.8 (P4), U103.16 (IN2)
A5F: R54.1, U8.17 (P14), U103.1 (IN1)
A6D: R48.2, U8.9 (P5), U103.8 (IN4)
A6F: R53.1, U8.18 (P15), U103.9 (IN3)
A7D: R49.2, U8.10 (P6), U106.16 (IN2)
A7F: R52.1, U8.19 (P16), U106.1 (IN1)
A8D: R50.2, U8.11 (P7), U106.8 (IN4)
A8F: R51.1, U8.20 (P17), U106.9 (IN3)
Audio 1A: J76.4, J77.1, U5.3 (S1), U5.14 (S2)
Audio 1B: J76.2, J77.3, U5.6 (S4), U5.11 (S3)
Audio 1C: J5.4, J7.1, U6.3 (S1), U6.14 (S2)
Audio 1D: J5.2, J7.3, U6.6 (S4), U6.11 (S3)
Audio 2A: J80.4, J90.1, U103.3 (S1), U103.14 (S2)
Audio 2B: J80.2, J90.3, U103.6 (S4), U103.11 (S3)
Audio 2C: J78.4, J79.1, U106.3 (S1), U106.14 (S2)
Audio 2D: J78.2, J79.3, U106.6 (S4), U106.11 (S3)
Direct 1: R38.1, R140.2, U5.15 (D2)
Direct 2: R39.1, R141.1, U5.7 (D4)
Direct 3: R34.1, R148.2, U6.15 (D2)
Direct 4: R35.1, R152.1, U6.7 (D4)
Direct 5: R36.1, R138.2, U103.15 (D2)
Direct 6: R31.1, R143.1, U103.7 (D4)
Direct 7: R32.1, R150.2, U106.15 (D2)
Direct 8: R33.1, R147.1, U106.7 (D4)
Filter 1: R139.2, U5.2 (D1)
Filter 2: R142.1, U5.10 (D3)
Filter 3: R145.2, U6.2 (D1)
Filter 4: R149.1, U6.10 (D3)
Filter 5: R137.2, U103.2 (D1)
Filter 6: R144.1, U103.10 (D3)
Filter 7: R146.2, U106.2 (D1)
Filter 8: R151.1, U106.10 (D3)
GNDA: C22.2, C23.2, C24.2, C25.1, C26.1, C27.1, C28.2, C29.1, C32.2, C33.2, C137.2, C138.1, C139.2, C140.1, C142.2, C143.2, J5.1, J5.3, J6.2, J7.2, J7.4, J8.2, J9.1, J76.1, J76.3, J77.2, J77.4, J78.1, J78.3, J79.2, J79.4, J80.1, J80.3, J90.2, J90.4, JP2.1 (A), JP3.1 (A), JP4.1 (A), R137.1, R138.1, R139.1, R140.1, R141.2, R142.2, R143.2, R144.2, R145.1, R146.1, R147.2, R148.1, R149.2, R150.1, R151.2, R152.2, U5.5 (GND), U6.5 (GND), U8.12 (GND), U9.1 (GND), U10.3 (+), U72.1 (GND), U103.5 (GND), U106.5 (GND)
unnamed: C34.1, J8.1, R30.2, U10.1
unnamed: C34.2, R30.1, R31.2, R32.2, R33.2, R34.2, R35.2, R36.2, R38.2, R39.2, U10.2 (-)
unnamed: JP2.2 (B), R29.2, U8.21 (A0)
unnamed: JP3.2 (B), R28.2, U8.2 (A1)
unnamed: JP4.2 (B), R27.2, U8.3 (A2)
unnamed: Q11.2, R59.1, U8.22 (SCL)
unnamed: Q12.2, R60.1, U8.23 (SDA)
SCL0: J9.3, Q11.3
SDA0: J9.2, Q12.3

Notes on the sheet:
8 oscillator channels in 16 channels out - Oscillator direct - To 3 state filters
Direct out To mixer
