markeby/Synth32/Schematics/Noise.kicad_sch

## KiCad design Schematics/Noise.kicad_sch (2024-11-26)

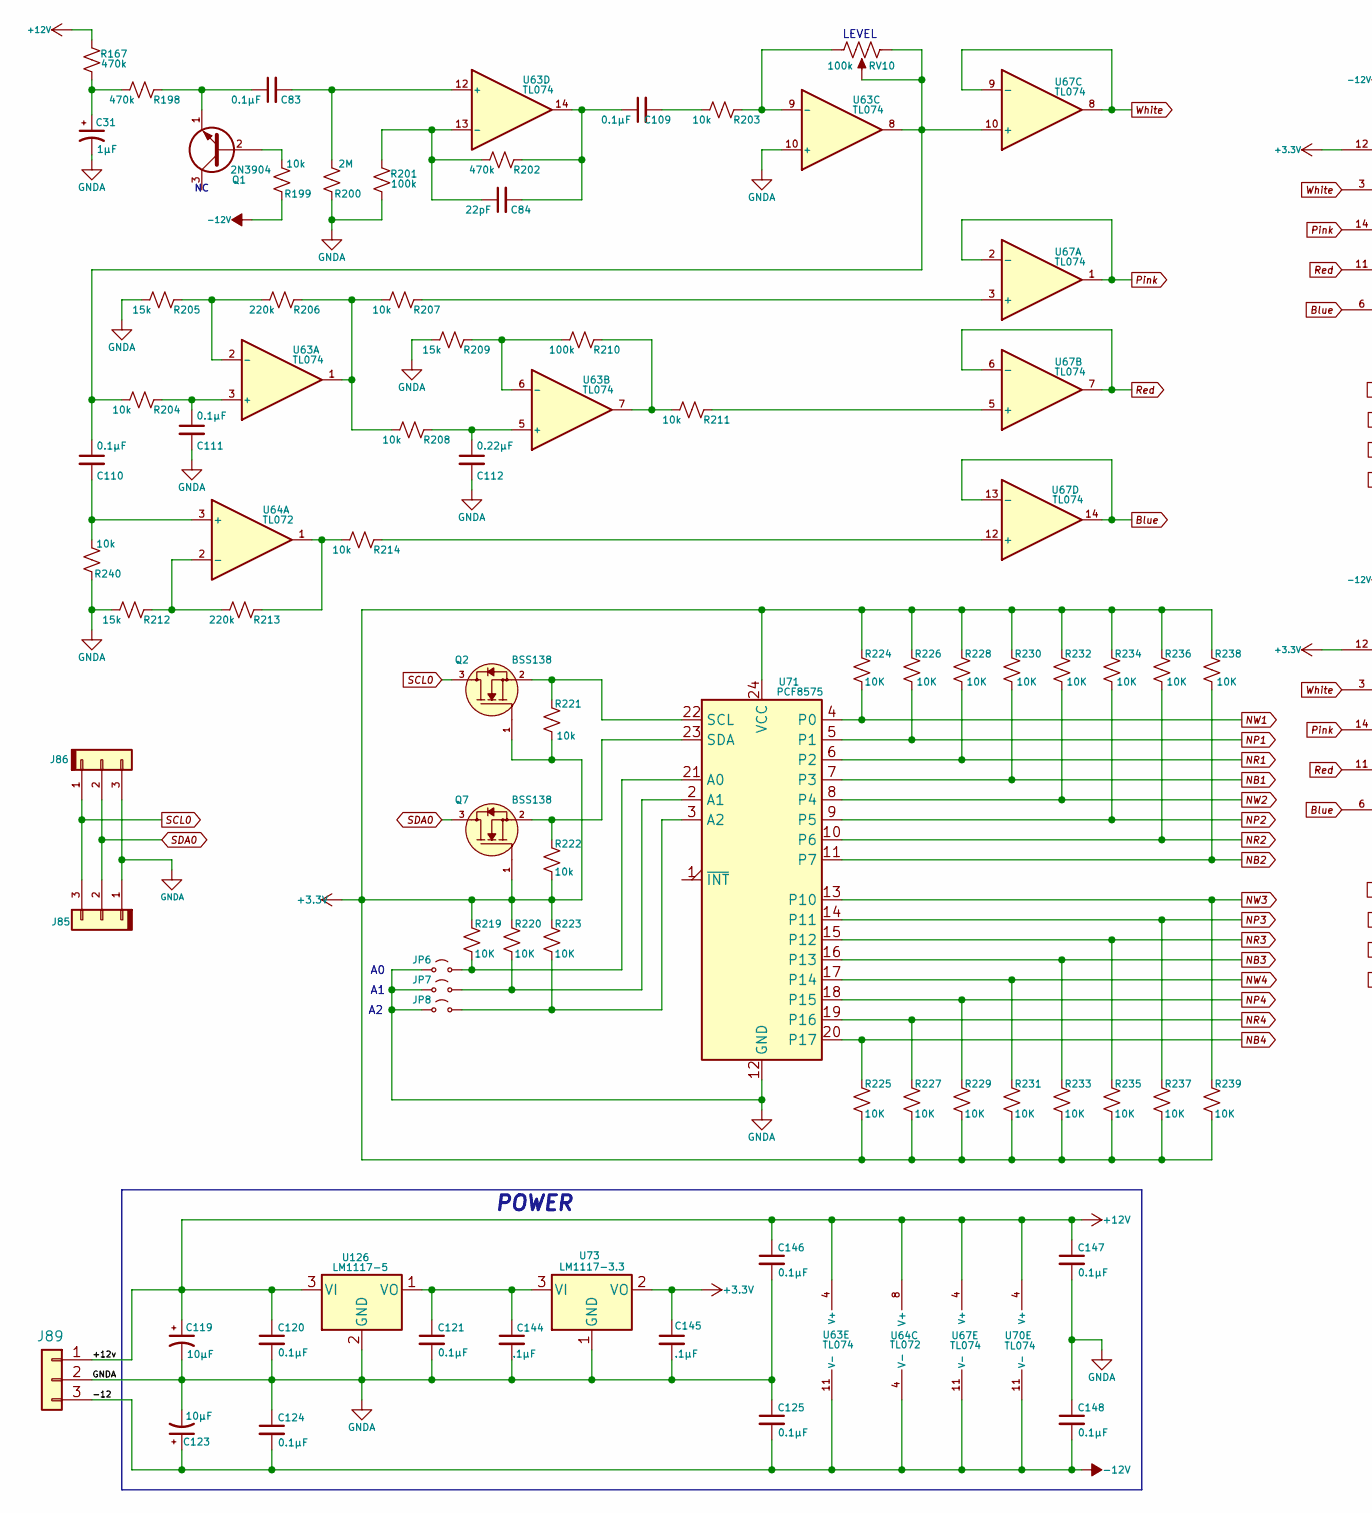
[picture p15: schematic Noise.kicad_sch, part in row 1, column 1]

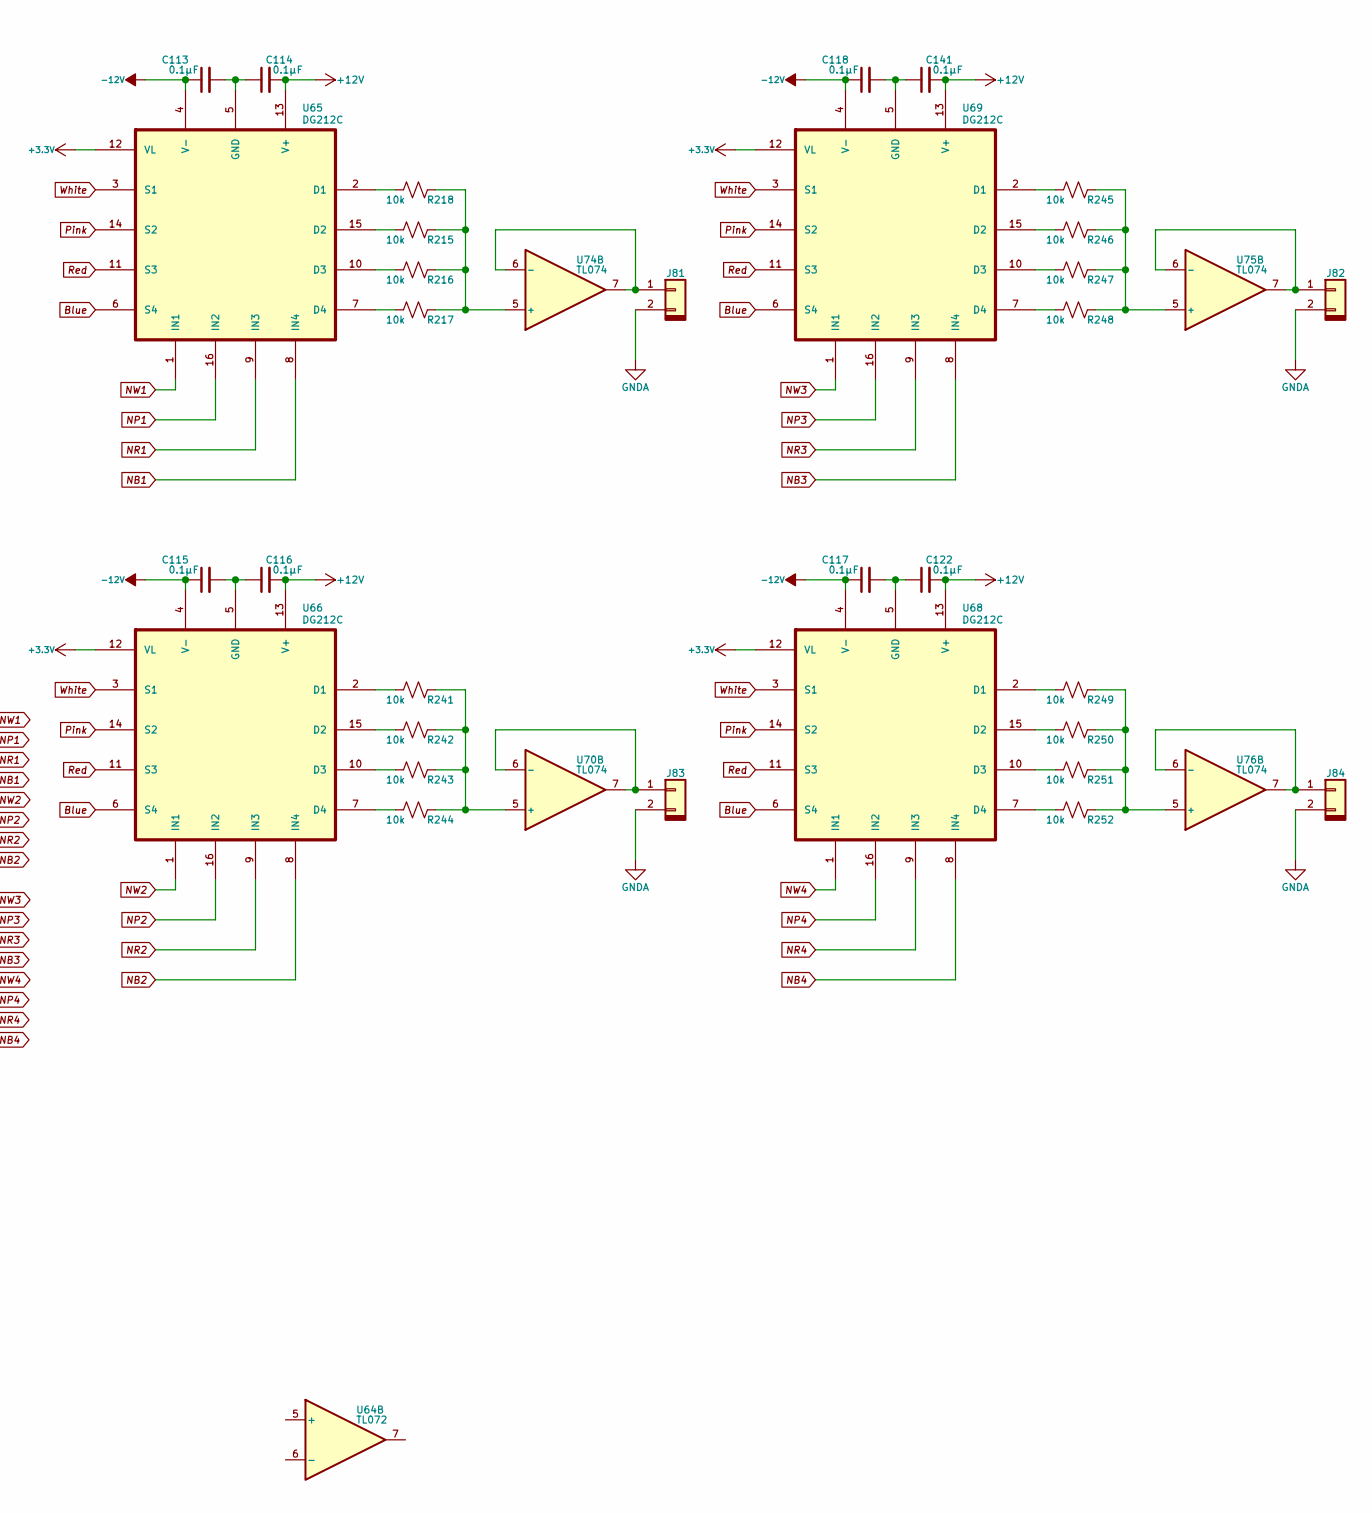
[picture p16: schematic Noise.kicad_sch, part in row 1, column 2]

Parts:
C31: 1µF
C83, C109, C110, C111, C113, C114, C115, C116, C117, C118, C120, C121, C122, C124, C125, C141, C146, C147, C148: 0.1µF
C84: 22pF
C112: 0.22µF
C119, C123: 10µF
C144, C145: .1µF
J81, J82, J83, J84: Conn_01x02
J85, J86, J89: Conn_01x03
JP6, JP7, JP8: Jumper_2_Small_Open
Q1: 2N3904; TO-92_Inline
Q2, Q7: BSS138; SOT-23-3; MPN BSS138; Digi-Key_PN BSS138CT-ND
R167, R198, R202: 470k
R199, R203, R204, R207, R208, R211, R214, R215, R216, R217, R218, R221, R222, R240, R241, R242, R243, R244, R245, R246, R247, R248, R249, R250, R251, R252: 10k
R200: 2M
R201, R210: 100k
R205, R209, R212: 15k
R206, R213: 220k
R219, R220, R223, R224, R225, R226, R227, R228, R229, R230, R231, R232, R233, R234, R235, R236, R237, R238, R239: 10K
RV10: 100k
U63, U67, U70, U74, U75, U76: TL074
U64: TL072
U65, U66, U68, U69: DG212C
U71: PCF8575; SSOP-24_5.3x8.2mm_P0.65mm
U73: LM1117-3.3
U126: LM1117-5; TO-92_Inline

Connections:
+3.3V: C145.1, Q2.1, Q7.1, R219.1, R220.1, R221.2, R222.2, R223.1, R224.1, R225.2, R226.1, R227.2, R228.1, R229.2, R230.1, R231.2, R232.1, R233.2, R234.1, R235.2, R236.1, R237.2, R238.1, R239.2, U65.12 (VL), U66.12 (VL), U68.12 (VL), U69.12 (VL), U71.24 (VCC), U73.2 (VO)
+12v: C114.2, C116.2, C119.1, C120.1, C122.2, C141.2, C146.1, C147.1, J89.1, R167.1, U63.4 (V+), U64.8 (V+), U65.13 (V+), U66.13 (V+), U67.4 (V+), U68.13 (V+), U69.13 (V+), U70.4 (V+), U126.3 (VI)
-12V: C113.1, C115.1, C117.1, C118.1, C123.1, C124.2, C125.2, C148.2, J89.3, R199.2, U63.11 (V-), U64.4 (V-), U65.4 (V-), U66.4 (V-), U67.11 (V-), U68.4 (V-), U69.4 (V-), U70.11 (V-)
Blue: U65.6 (S4), U66.6 (S4), U67.13 (-), U67.14, U68.6 (S4), U69.6 (S4)
GNDA: C31.2, C111.2, C112.2, C119.2, C120.2, C121.2, C123.2, C124.1, C125.1, C144.2, C145.2, C146.2, C147.2, C148.1, J81.2, J82.2, J83.2, J84.2, J85.1, J86.3, J89.2, JP6.1 (A), JP7.1 (A), JP8.1 (A), R200.2, R201.2, R205.1, R209.1, R212.1, R240.2, U63.10 (+), U71.12 (GND), U73.1 (GND), U126.2 (GND)
NB1: R230.2, U65.8 (IN4), U71.7 (P3)
NB2: R238.2, U66.8 (IN4), U71.11 (P7)
NB3: R233.1, U69.8 (IN4), U71.16 (P13)
NB4: R225.1, U68.8 (IN4), U71.20 (P17)
NP1: R226.2, U65.16 (IN2), U71.5 (P1)
NP2: R234.2, U66.16 (IN2), U71.9 (P5)
NP3: R237.1, U69.16 (IN2), U71.14 (P11)
NP4: R229.1, U68.16 (IN2), U71.18 (P15)
NR1: R228.2, U65.9 (IN3), U71.6 (P2)
NR2: R236.2, U66.9 (IN3), U71.10 (P6)
NR3: R235.1, U69.9 (IN3), U71.15 (P12)
NR4: R227.1, U68.9 (IN3), U71.19 (P16)
NW1: R224.2, U65.1 (IN1), U71.4 (P0)
NW2: R232.2, U66.1 (IN1), U71.8 (P4)
NW3: R239.1, U69.1 (IN1), U71.13 (P10)
NW4: R231.1, U68.1 (IN1), U71.17 (P14)
unnamed: C31.1, R167.2, R198.1
unnamed: C83.1, Q1.1 (E), R198.2
unnamed: C83.2, R200.1, U63.12 (+)
unnamed: C84.1, R201.1, R202.1, U63.13 (-)
unnamed: C84.2, C109.1, R202.2, U63.14
unnamed: C109.2, R203.1
unnamed: C110.1, R204.1, RV10., U63.8, U67.10 (+)
unnamed: C110.2, R240.1, U64.3 (+)
unnamed: C111.1, R204.2, U63.3 (+)
unnamed: C112.1, R208.2, U63.5 (+)
unnamed: C113.2, C114.1, U65.5 (GND)
unnamed: C115.2, C116.1, U66.5 (GND)
unnamed: C117.2, C122.1, U68.5 (GND)
unnamed: C118.2, C141.1, U69.5 (GND)
unnamed: C121.1, C144.1, U73.3 (VI), U126.1 (VO)
unnamed: J81.1, U74.6 (-), U74.7
unnamed: J82.1, U75.6 (-), U75.7
unnamed: J83.1, U70.6 (-), U70.7
unnamed: J84.1, U76.6 (-), U76.7
unnamed: JP6.2 (B), R219.2, U71.21 (A0)
unnamed: JP7.2 (B), R220.2, U71.2 (A1)
unnamed: JP8.2 (B), R223.2, U71.3 (A2)
unnamed: Q1.2 (B), R199.1
unnamed: Q2.2, R221.1, U71.22 (SCL)
unnamed: Q7.2, R222.1, U71.23 (SDA)
unnamed: R203.2, RV10., U63.9 (-)
unnamed: R205.2, R206.1, U63.2 (-)
unnamed: R206.2, R207.1, R208.1, U63.1
unnamed: R207.2, U67.3 (+)
unnamed: R209.2, R210.1, U63.6 (-)
unnamed: R210.2, R211.1, U63.7
unnamed: R211.2, U67.5 (+)
unnamed: R212.2, R213.1, U64.2 (-)
unnamed: R213.2, R214.1, U64.1
unnamed: R214.2, U67.12 (+)
unnamed: R215.1, U65.15 (D2)
unnamed: R215.2, R216.2, R217.2, R218.2, U74.5 (+)
unnamed: R216.1, U65.10 (D3)
unnamed: R217.1, U65.7 (D4)
unnamed: R218.1, U65.2 (D1)
unnamed: R241.1, U66.2 (D1)
unnamed: R241.2, R242.2, R243.2, R244.2, U70.5 (+)
unnamed: R242.1, U66.15 (D2)
unnamed: R243.1, U66.10 (D3)
unnamed: R244.1, U66.7 (D4)
unnamed: R245.1, U69.2 (D1)
unnamed: R245.2, R246.2, R247.2, R248.2, U75.5 (+)
unnamed: R246.1, U69.15 (D2)
unnamed: R247.1, U69.10 (D3)
unnamed: R248.1, U69.7 (D4)
unnamed: R249.1, U68.2 (D1)
unnamed: R249.2, R250.2, R251.2, R252.2, U76.5 (+)
unnamed: R250.1, U68.15 (D2)
unnamed: R251.1, U68.10 (D3)
unnamed: R252.1, U68.7 (D4)
Pink: U65.14 (S2), U66.14 (S2), U67.1, U67.2 (-), U68.14 (S2), U69.14 (S2)
Red: U65.11 (S3), U66.11 (S3), U67.6 (-), U67.7, U68.11 (S3), U69.11 (S3)
SCL0: J85.3, J86.1, Q2.3
SDA0: J85.2, J86.2, Q7.3
White: U65.3 (S1), U66.3 (S1), U67.8, U67.9 (-), U68.3 (S1), U69.3 (S1)

Notes on the sheet:
POWER
LEVEL
