markeby/Synth32/Schematics/Osc2_Carry.kicad_sch

## KiCad design Schematics/Osc2_Carry.kicad_sch (2024-10-31)

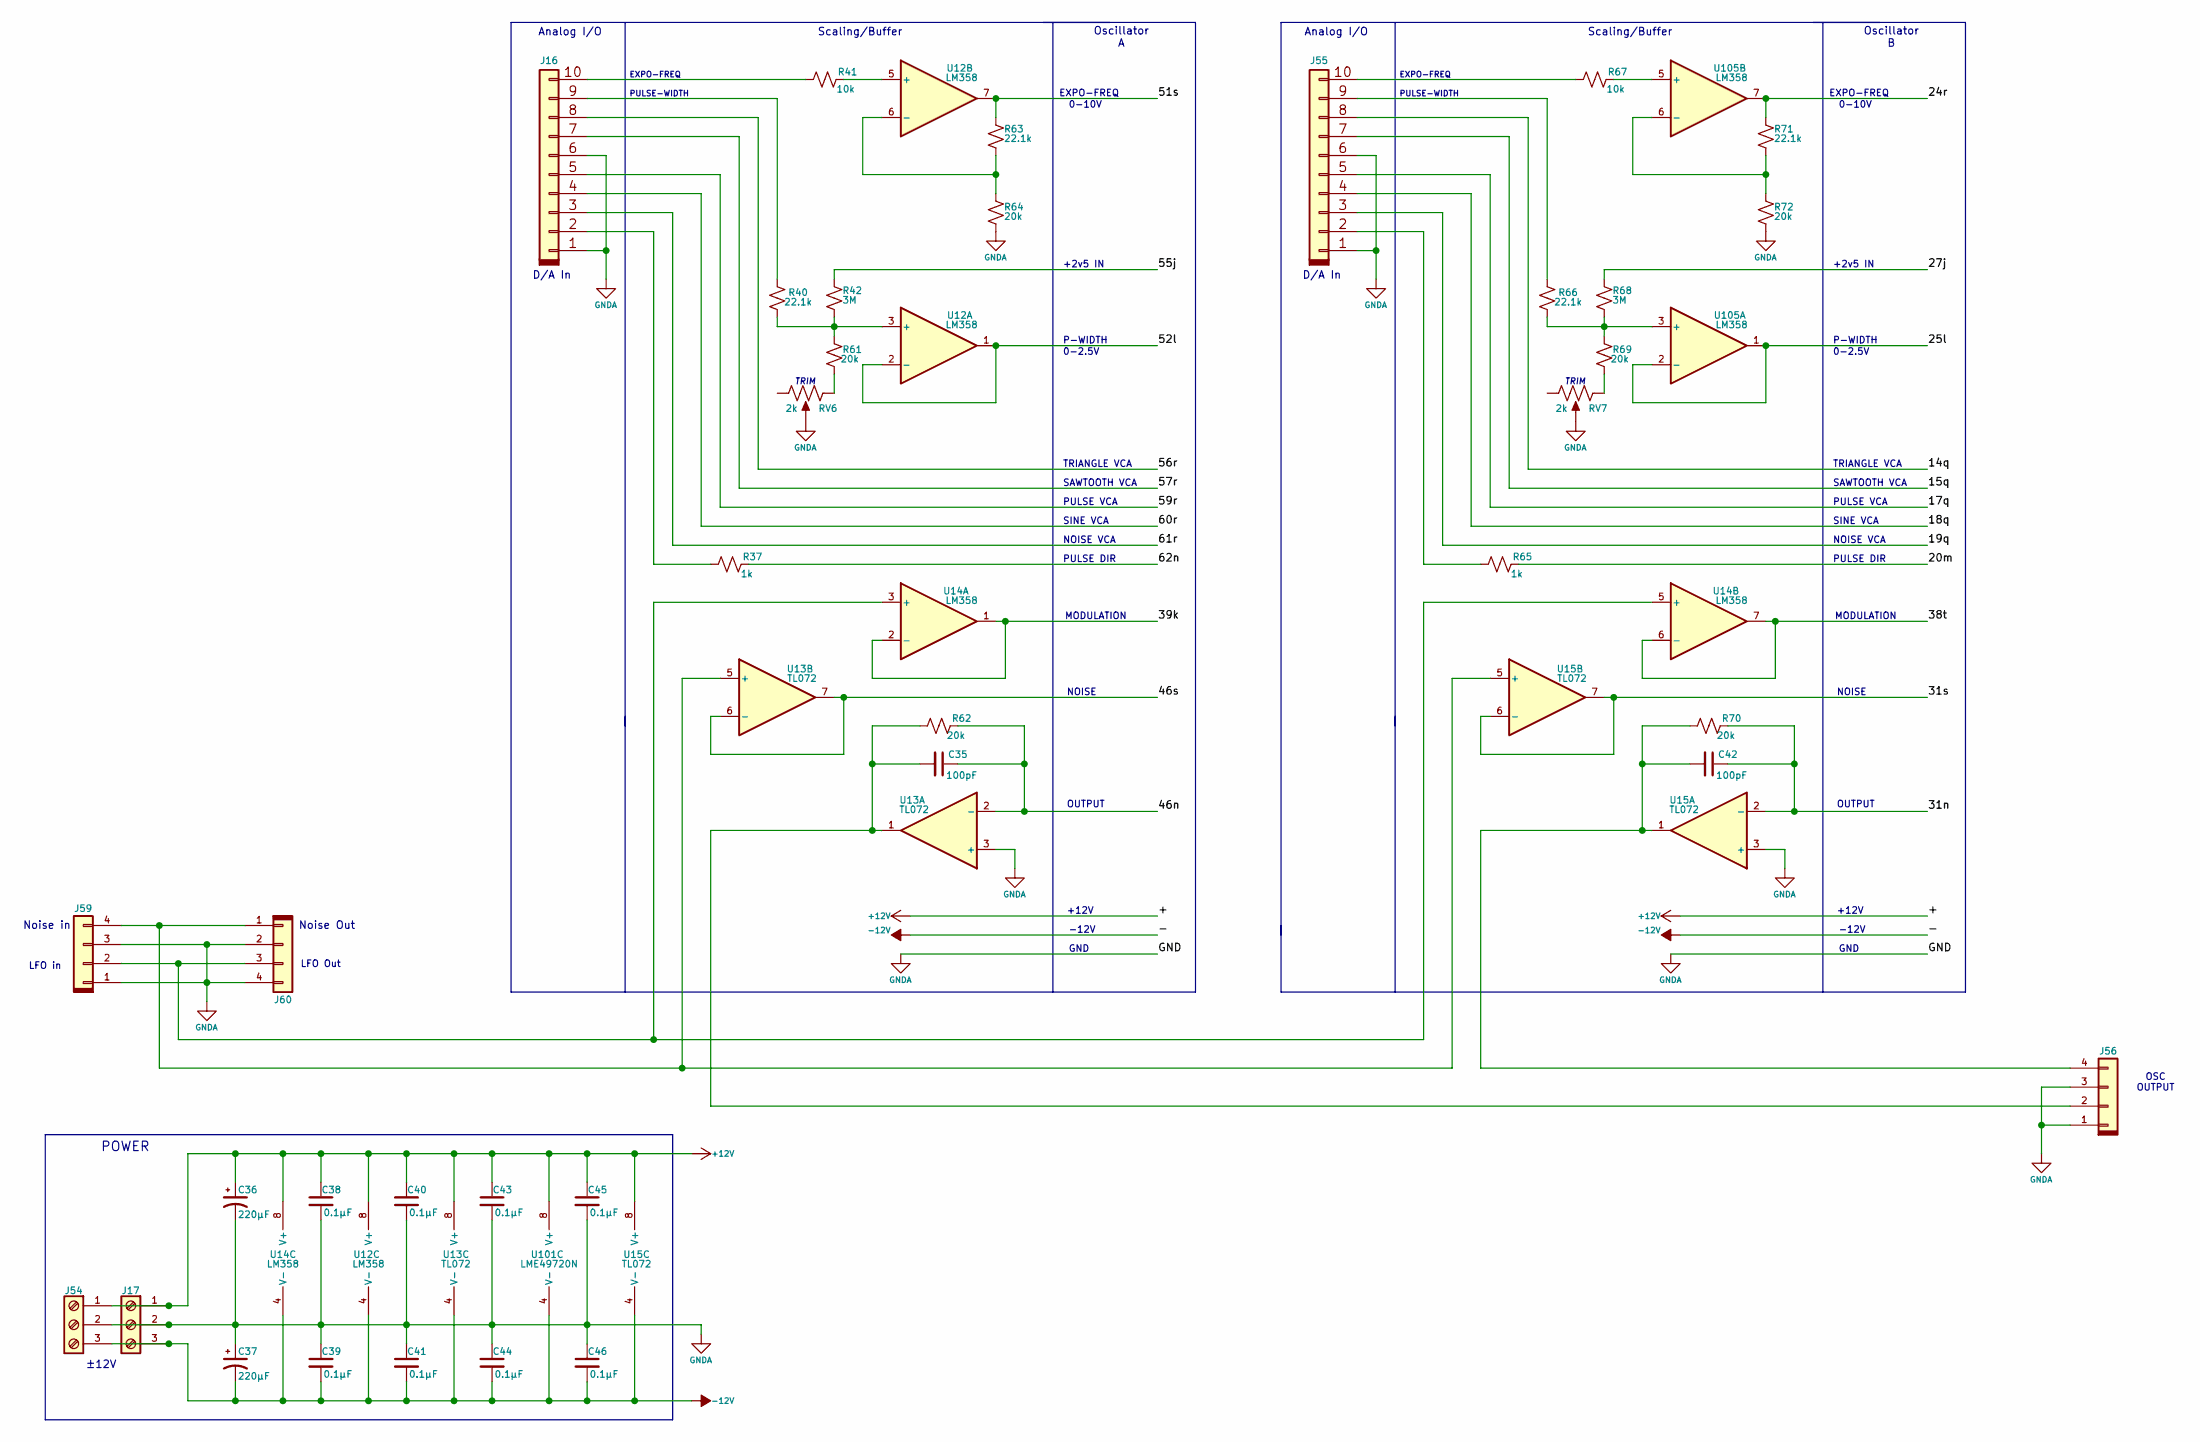
[picture p17: schematic Osc2_Carry.kicad_sch]

Parts:
C35, C42: 100pF
C36, C37: 220µF
C38, C39, C40, C41, C43, C44, C45, C46: 0.1µF
J16, J55: Conn_01x10h
J17, J54: Screw_Terminal_01x03
J56, J59, J60: Conn_01x04
R37, R65: 1k
R40, R63, R66, R71: 22.1k
R41, R67: 10k
R42, R68: 3M
R61, R62, R64, R69, R70, R72: 20k
RV6, RV7: 2k
U12, U14, U105: LM358
U13, U15: TL072
U101: LME49720N

Connections:
14q: J55.8
15q: J55.7
17q: J55.5
18q: J55.4
19q: J55.3
20m: R65.2
24r: R71.1, U105.7
25l: U105.1, U105.2 (-)
27j: R68.1
31n: C42.1, R70.2, U15.2 (-)
31s: U15.6 (-), U15.7
38t: U14.6 (-), U14.7
39k: U14.1, U14.2 (-)
46n: C35.1, R62.2, U13.2 (-)
46s: U13.6 (-), U13.7
51s: R63.1, U12.7
52l: U12.1, U12.2 (-)
55j: R42.1
56r: J16.8
57r: J16.7
59r: J16.5
60r: J16.4
61r: J16.3
62n: R37.2
+12V: C36.1, C38.1, C40.1, C43.1, C45.1, J17.1, J54.1, U12.8 (V+), U13.8 (V+), U14.8 (V+), U15.8 (V+), U101.8 (V+)
-12V: C37.2, C39.2, C41.2, C44.2, C46.2, J17.3, J54.3, U12.4 (V-), U13.4 (V-), U14.4 (V-), U15.4 (V-), U101.4 (V-)
GNDA: C36.2, C37.1, C38.2, C39.1, C40.2, C41.1, C43.2, C44.1, C45.2, C46.1, J16.1, J16.6, J17.2, J54.2, J55.1, J55.6, J56.1, J56.3, J59.1, J59.3, J60.2, J60.4, R64.2, R72.2, RV6., RV7., U13.3 (+), U15.3 (+)
unnamed: C35.2, J56.2, R62.1, U13.1
unnamed: C42.2, J56.4, R70.1, U15.1
unnamed: J16.2, R37.1
unnamed: J16.9, R40.1
unnamed: J16.10, R41.1
unnamed: J55.2, R65.1
unnamed: J55.9, R66.1
unnamed: J55.10, R67.1
unnamed: J59.2, J60.3, U14.3 (+), U14.5 (+)
unnamed: J59.4, J60.1, U13.5 (+), U15.5 (+)
unnamed: R40.2, R42.2, R61.1, U12.3 (+)
unnamed: R41.2, U12.5 (+)
unnamed: R61.2, RV6.
unnamed: R63.2, R64.1, U12.6 (-)
unnamed: R66.2, R68.2, R69.1, U105.3 (+)
unnamed: R67.2, U105.5 (+)
unnamed: R69.2, RV7.
unnamed: R71.2, R72.1, U105.6 (-)

Notes on the sheet:
OUTPUT
Scaling/Buffer
OSC OUTPUT
Noise in
-12V
Oscillator A
_{TRIM}
Noise Out
0-2.5V
GND
Analog I/O
+12V
MODULATION
EXPO-FREQ
LFO in
PULSE DIR
LFO Out
D/A In
POWER
TRIANGLE VCA
NOISE
NOISE VCA
P-WIDTH
SINE VCA
0-10V
PULSE-WIDTH
±12V
+2v5 IN
PULSE VCA
SAWTOOTH VCA
Oscillator B
