markeby/Synth32/Schematics/Oscc_6Ifc.kicad_sch

## KiCad design Schematics/Oscc_6Ifc.kicad_sch (2024-07-26)

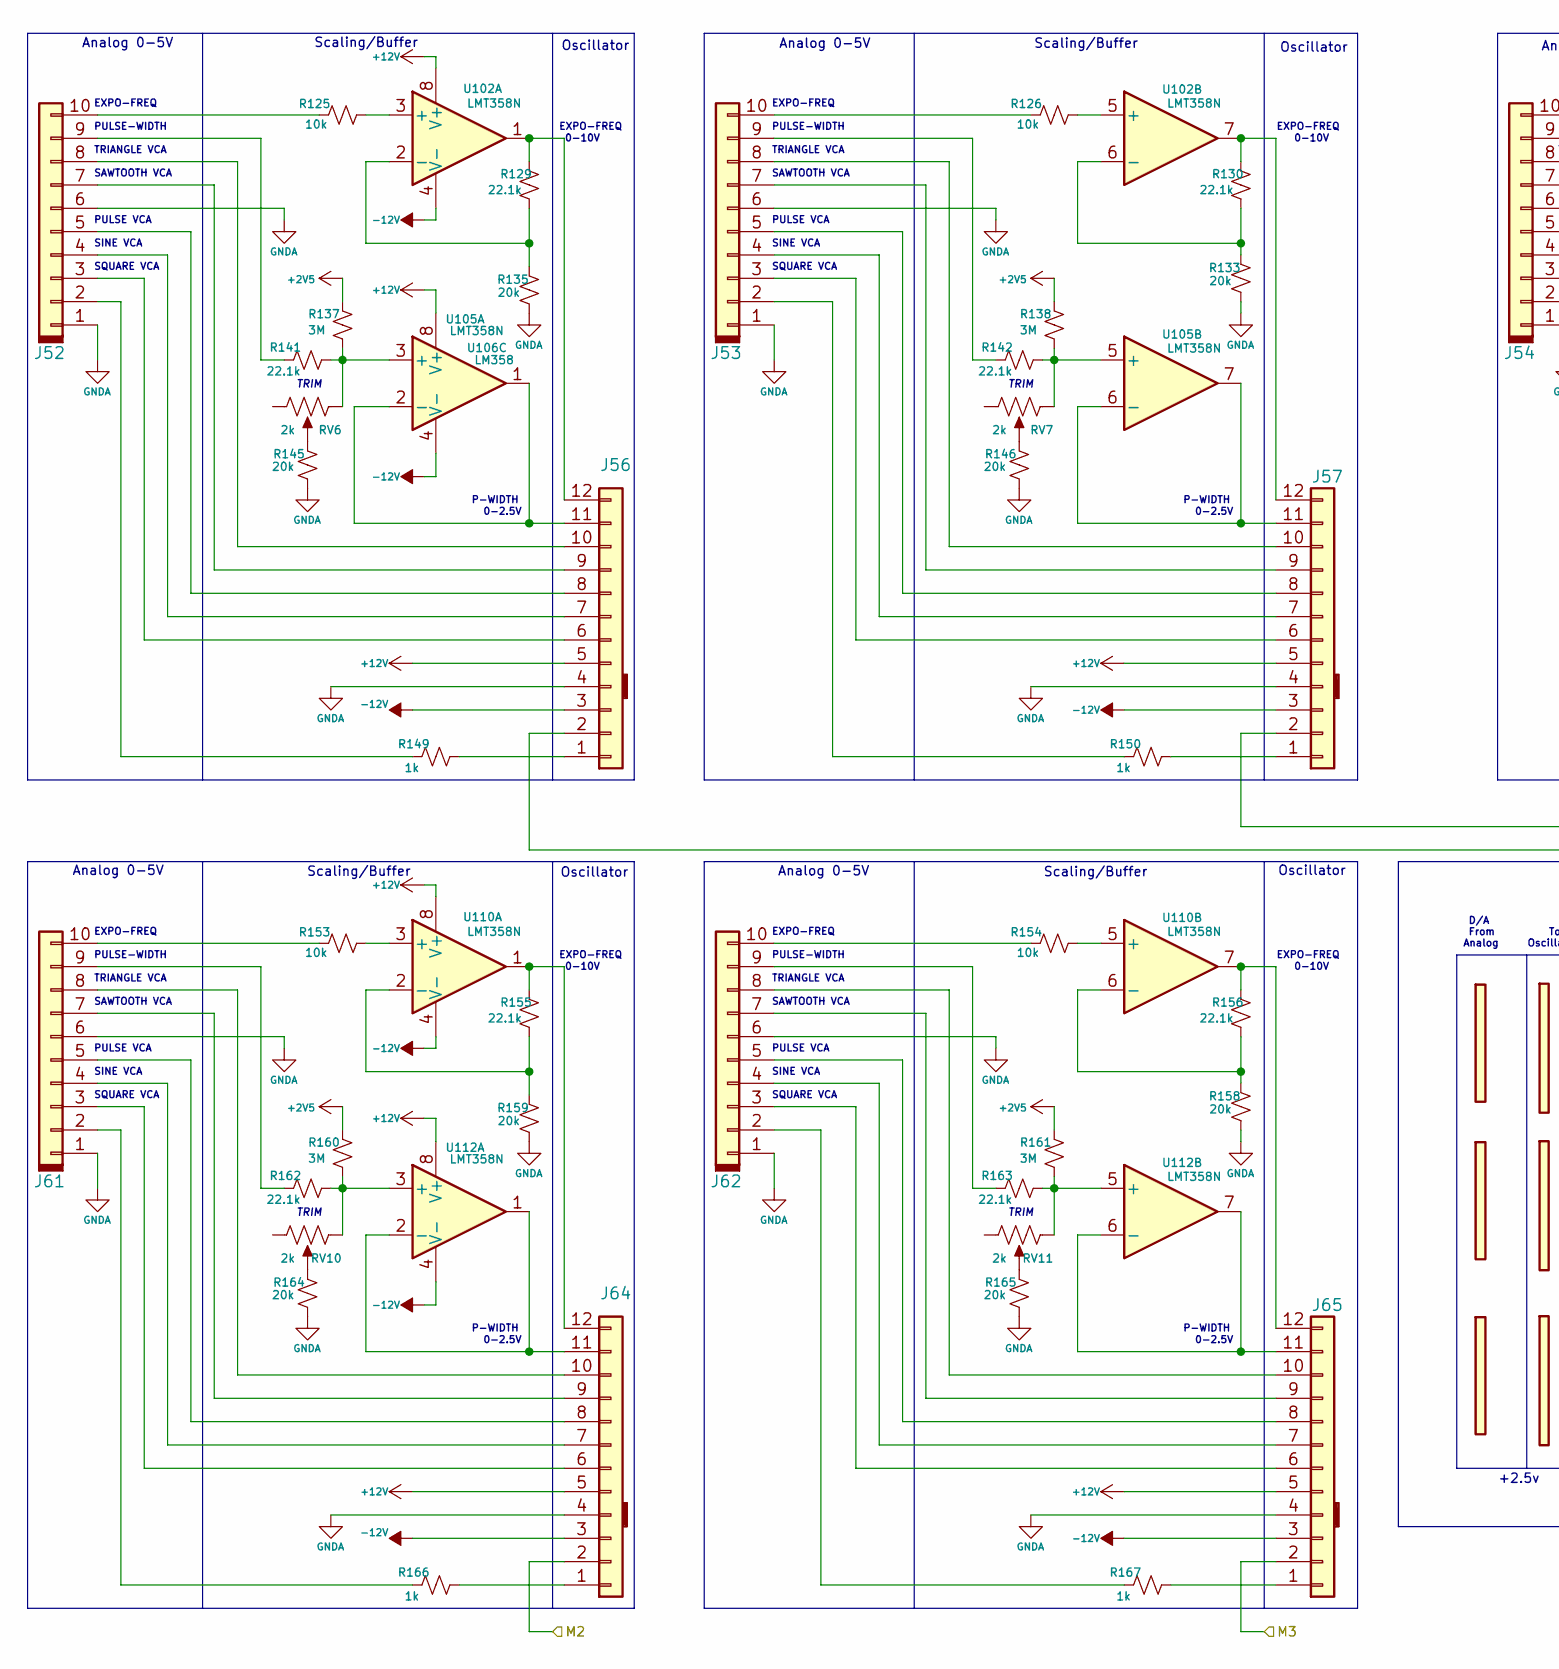
[picture p18: schematic Oscc_6Ifc.kicad_sch, part in row 1, column 1]

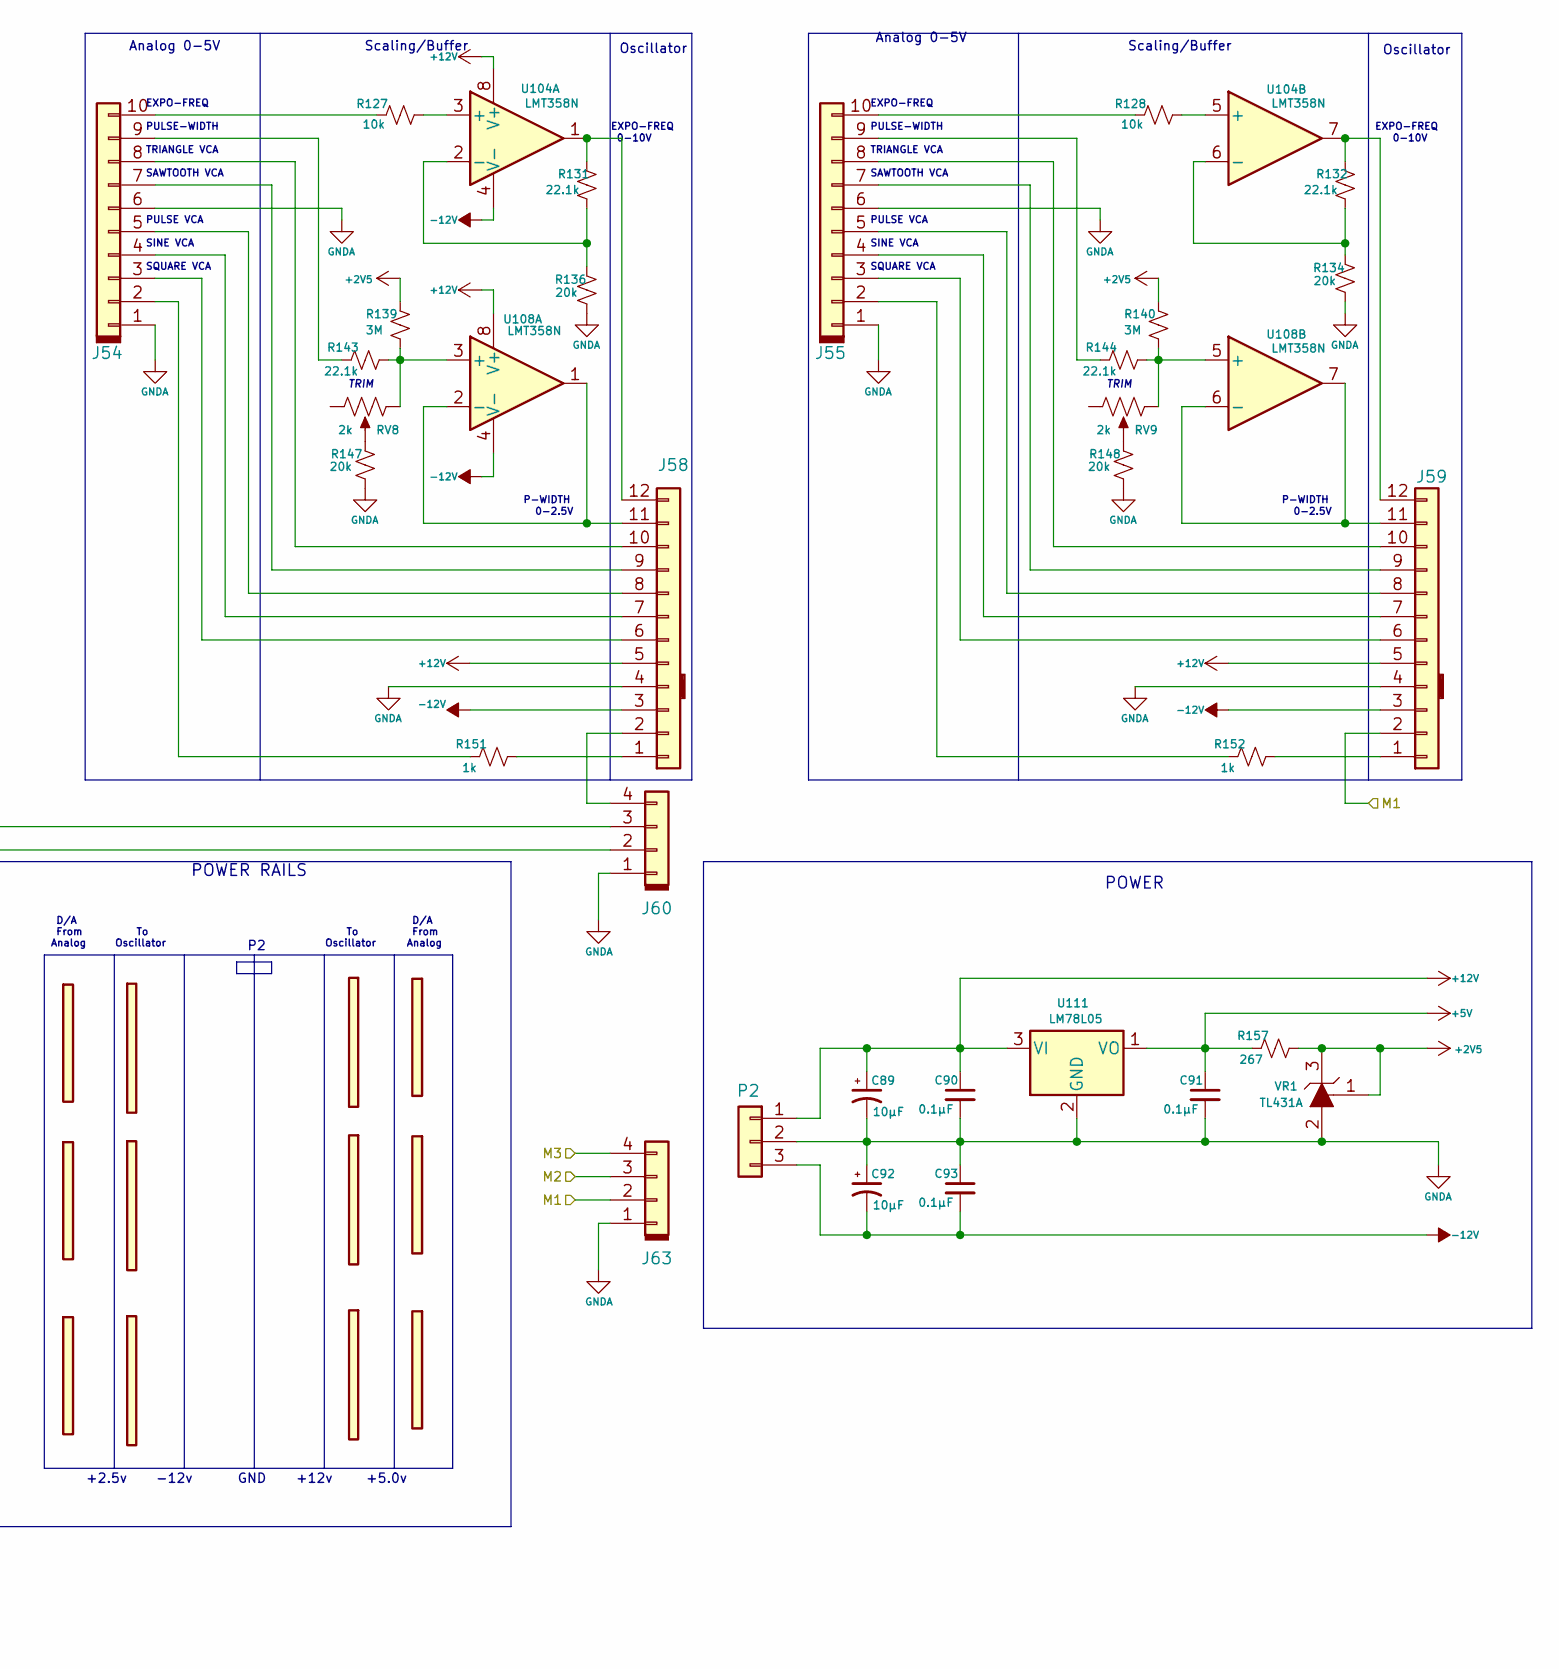
[picture p19: schematic Oscc_6Ifc.kicad_sch, part in row 1, column 2]

Parts:
C89, C92: 10µF
C90, C91, C93: 0.1µF
J52, J53, J54, J55, J61, J62: Conn_01x10h
J56, J57, J58, J59, J64, J65: Conn_01x12
J60, J63: Conn_01x04
JM1, JM2, JM5, JM6, JM9, JM10: Model_12
JM3, JM4, JM7, JM8, JM11, JM12: Model_10
P2: Conn_01x03
R125, R126, R127, R128, R153, R154: 10k
R129, R130, R131, R132, R141, R142, R143, R144, R155, R156, R162, R163: 22.1k
R133, R134, R135, R136, R145, R146, R147, R148, R158, R159, R164, R165: 20k
R137, R138, R139, R140, R160, R161: 3M
R149, R150, R151, R152, R166, R167: 1k
R157: 267
RV6, RV7, RV8, RV9, RV10, RV11: 2k
U101, U103, U106, U107, U109, U113: LM358
U102, U104, U105, U108, U110, U112: LMT358N
U111: LM78L05; TO-92_Inline
VR1: TL431A; TO-92-3_Formed_Leads; MPN TL431CLPM; Digi-Key_PN 296-26717-1-ND

Connections:
+2V5: R137.1, R138.1, R139.1, R140.1, R157.2, R160.1, R161.1, VR1.1 (REF), VR1.3 (K)
+5V: C91.1, R157.1, U111.1 (VO)
+12V: C89.1, C90.1, J56.5, J57.5, J58.5, J59.5, J64.5, J65.5, P2.1, U101.8 (V+), U103.8 (V+), U106.8 (V+), U107.8 (V+), U109.8 (V+), U111.3 (VI), U113.8 (V+)
-12V: C92.2, C93.2, J56.3, J57.3, J58.3, J59.3, J64.3, J65.3, P2.3, U101.4 (V-), U103.4 (V-), U106.4 (V-), U107.4 (V-), U109.4 (V-), U113.4 (V-)
GNDA: C89.2, C90.2, C91.2, C92.1, C93.1, J52.1, J52.6, J53.1, J53.6, J54.1, J54.6, J55.1, J55.6, J56.4, J57.4, J58.4, J59.4, J60.1, J61.1, J61.6, J62.1, J62.6, J63.1, J64.4, J65.4, P2.2, R133.2, R134.2, R135.2, R136.2, R145.2, R146.2, R147.2, R148.2, R158.2, R159.2, R164.2, R165.2, U111.2 (GND), VR1.2 (A)
M1: J59.2, J63.2
M2: J63.3, J64.2
M3: J63.4, J65.2
unnamed: J52.2, R149.1
unnamed: J52.3, J56.6
unnamed: J52.4, J56.7
unnamed: J52.5, J56.8
unnamed: J52.7, J56.9
unnamed: J52.8, J56.10
unnamed: J52.9, R141.1
unnamed: J52.10, R125.1
unnamed: J53.2, R150.1
unnamed: J53.3, J57.6
unnamed: J53.4, J57.7
unnamed: J53.5, J57.8
unnamed: J53.7, J57.9
unnamed: J53.8, J57.10
unnamed: J53.9, R142.1
unnamed: J53.10, R126.1
unnamed: J54.2, R151.1
unnamed: J54.3, J58.6
unnamed: J54.4, J58.7
unnamed: J54.5, J58.8
unnamed: J54.7, J58.9
unnamed: J54.8, J58.10
unnamed: J54.9, R143.1
unnamed: J54.10, R127.1
unnamed: J55.2, R152.1
unnamed: J55.3, J59.6
unnamed: J55.4, J59.7
unnamed: J55.5, J59.8
unnamed: J55.7, J59.9
unnamed: J55.8, J59.10
unnamed: J55.9, R144.1
unnamed: J55.10, R128.1
unnamed: J56.1, R149.2
unnamed: J56.2, J60.2
unnamed: J56.11, U105.1, U105.2 (-)
unnamed: J56.12, R129.1, U102.1
unnamed: J57.1, R150.2
unnamed: J57.2, J60.3
unnamed: J57.11, U105.6 (-), U105.7
unnamed: J57.12, R130.1, U102.7
unnamed: J58.1, R151.2
unnamed: J58.2, J60.4
unnamed: J58.11, U108.1, U108.2 (-)
unnamed: J58.12, R131.1, U104.1
unnamed: J59.1, R152.2
unnamed: J59.11, U108.6 (-), U108.7
unnamed: J59.12, R132.1, U104.7
unnamed: J61.2, R166.1
unnamed: J61.3, J64.6
unnamed: J61.4, J64.7
unnamed: J61.5, J64.8
unnamed: J61.7, J64.9
unnamed: J61.8, J64.10
unnamed: J61.9, R162.1
unnamed: J61.10, R153.1
unnamed: J62.2, R167.1
unnamed: J62.3, J65.6
unnamed: J62.4, J65.7
unnamed: J62.5, J65.8
unnamed: J62.7, J65.9
unnamed: J62.8, J65.10
unnamed: J62.9, R163.1
unnamed: J62.10, R154.1
unnamed: J64.1, R166.2
unnamed: J64.11, U112.1, U112.2 (-)
unnamed: J64.12, R155.1, U110.1
unnamed: J65.1, R167.2
unnamed: J65.11, U112.6 (-), U112.7
unnamed: J65.12, R156.1, U110.7
unnamed: R125.2, U102.3 (+)
unnamed: R126.2, U102.5 (+)
unnamed: R127.2, U104.3 (+)
unnamed: R128.2, U104.5 (+)
unnamed: R129.2, R135.1, U102.2 (-)
unnamed: R130.2, R133.1, U102.6 (-)
unnamed: R131.2, R136.1, U104.2 (-)
unnamed: R132.2, R134.1, U104.6 (-)
unnamed: R137.2, R141.2, RV6., U105.3 (+)
unnamed: R138.2, R142.2, RV7., U105.5 (+)
unnamed: R139.2, R143.2, RV8., U108.3 (+)
unnamed: R140.2, R144.2, RV9., U108.5 (+)
unnamed: R145.1, RV6.
unnamed: R146.1, RV7.
unnamed: R147.1, RV8.
unnamed: R148.1, RV9.
unnamed: R153.2, U110.3 (+)
unnamed: R154.2, U110.5 (+)
unnamed: R155.2, R159.1, U110.2 (-)
unnamed: R156.2, R158.1, U110.6 (-)
unnamed: R160.2, R162.2, RV10., U112.3 (+)
unnamed: R161.2, R163.2, RV11., U112.5 (+)
unnamed: R164.1, RV10.
unnamed: R165.1, RV11.

Notes on the sheet:
PULSE-WIDTH
Oscillator
+12v
Analog 0-5V
GND
POWER RAILS
SQUARE VCA
To Oscillator
0-10V
D/A From Analog
-12v
EXPO-FREQ
+5.0v
POWER
SAWTOOTH VCA
0-2.5V
P-WIDTH
TRIANGLE VCA
PULSE VCA
Scaling/Buffer
SINE VCA
_{TRIM}
+2.5v
