markeby/Synth32/Schematics/PSU.kicad_sch

## KiCad design Schematics/PSU.kicad_sch (2024-10-31)

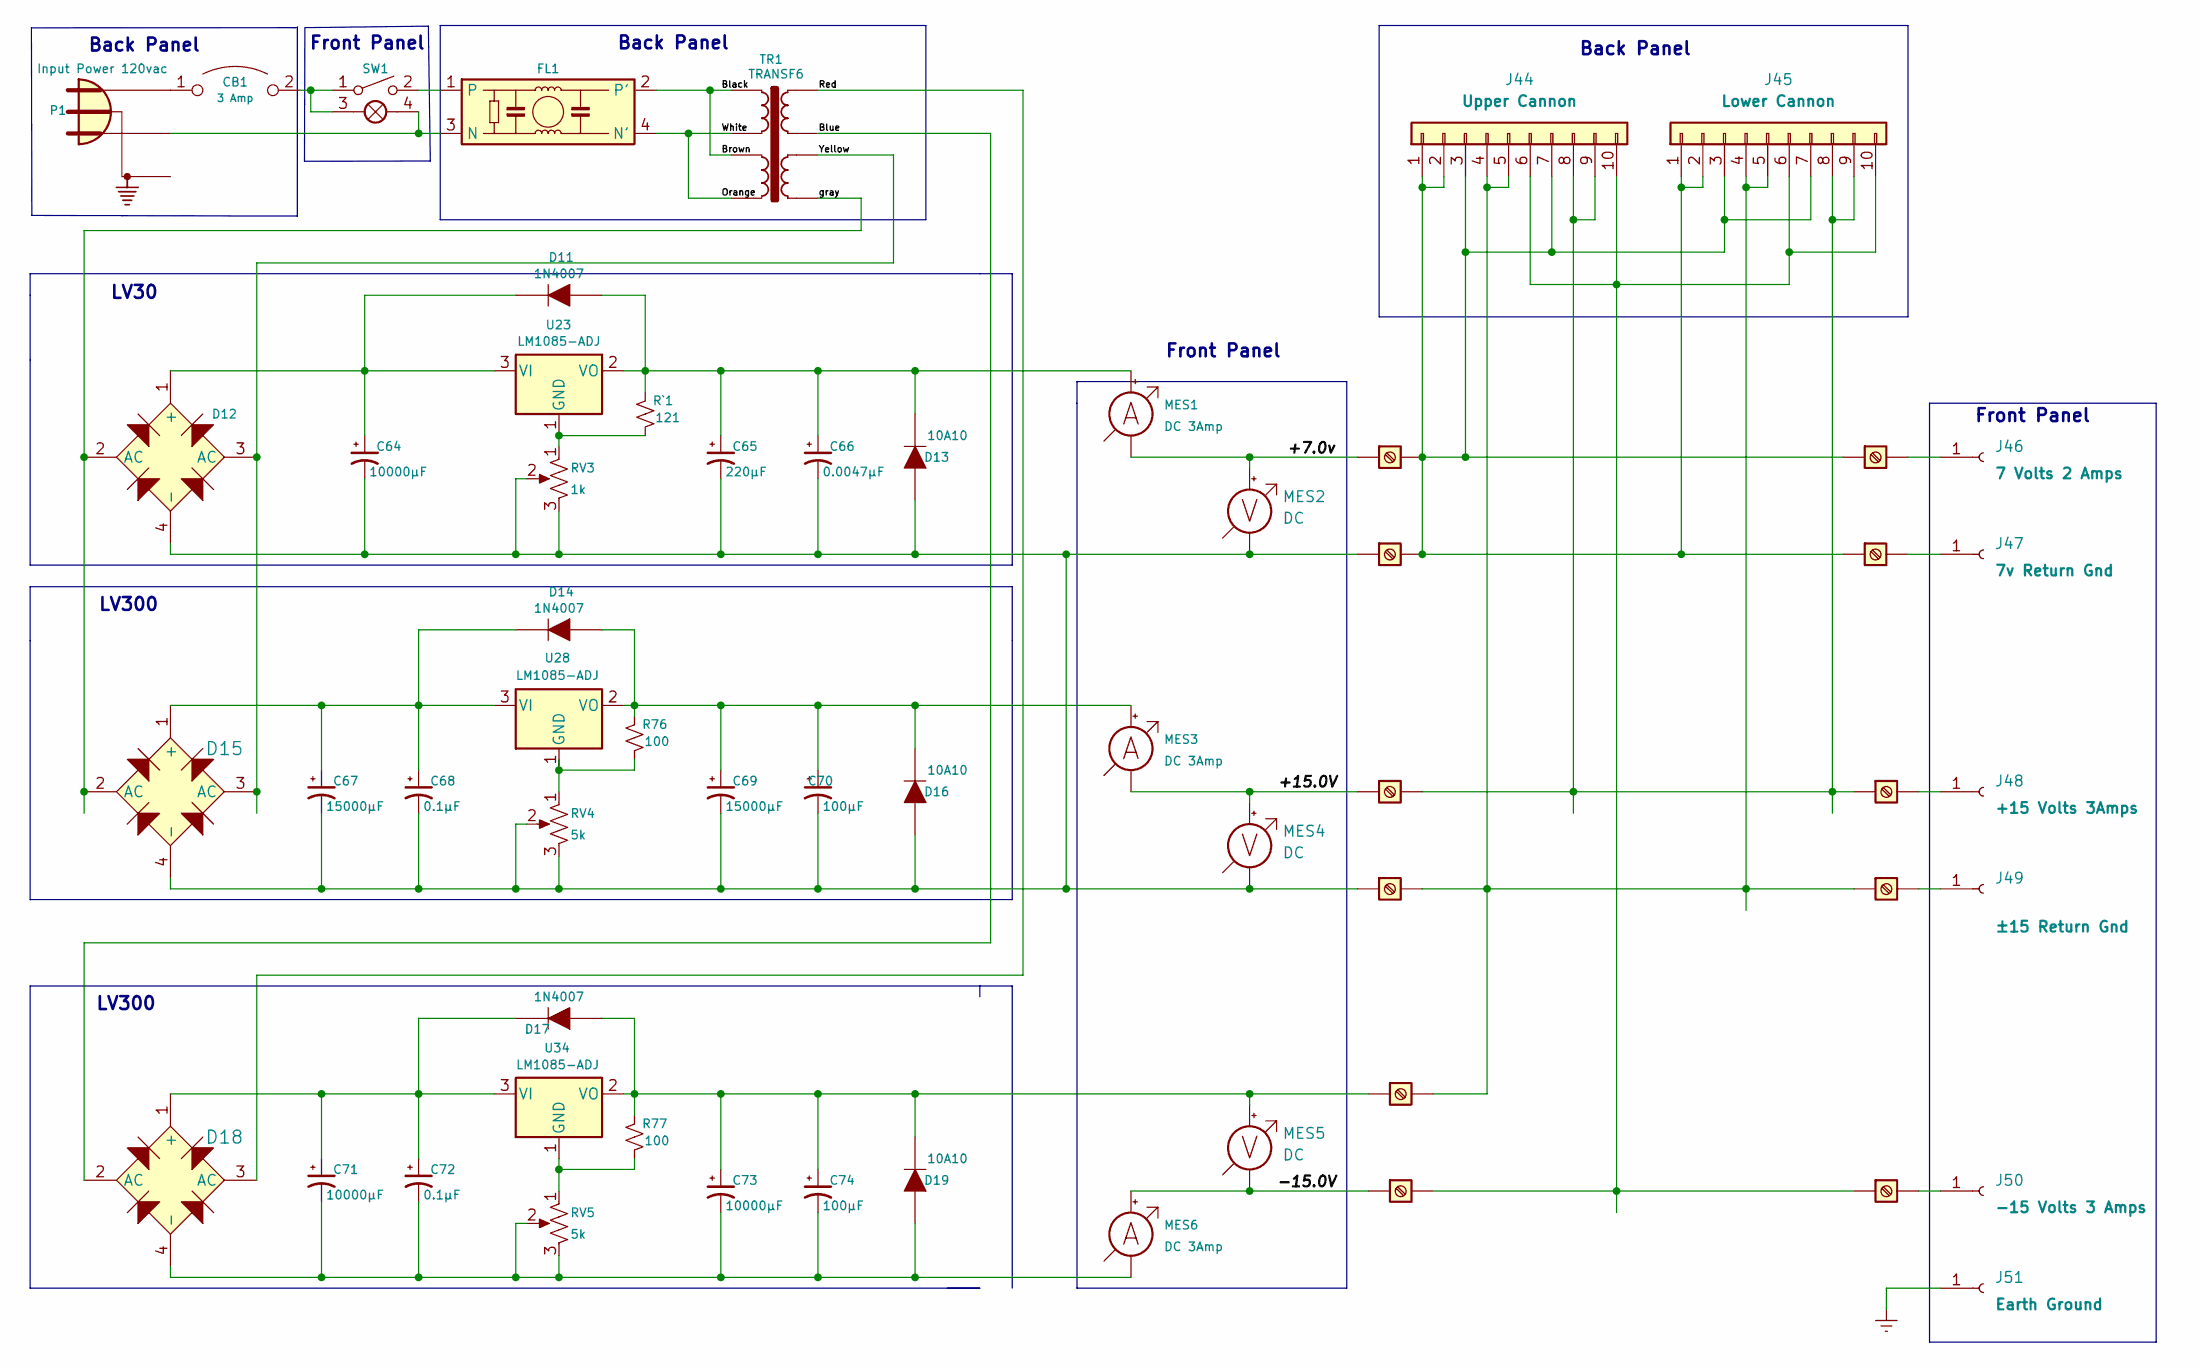
[picture p20: schematic PSU.kicad_sch]

Parts:
C64, C71, C73: 10000µF
C65: 220µF
C66: 0.0047µF
C67, C69: 15000µF
C68, C72: 0.1µF
C70, C74: 100µF
CB1: 3 Amp
D11, D14, D17: 1N4007; DO-41; MPN 1N4007-T; Digi-Key_PN 1N4007DICT-ND
D12, D15, D18: KBP04G; SIP-4_W3.81mm; MPN KBP04G; Digi-Key_PN KBP04G-ND
D13, D16, D19: 10A10; DO-41; MPN 1N4007-T; Digi-Key_PN 1N4007DICT-ND
FL1: 1FP45-0R; Filter_FILTERCON_1FPxx
J44: Upper Cannon
J45: Lower Cannon
J46: 7 Volts 2 Amps
J47: 7v Return Gnd
J48: +15 Volts 3Amps
J49: ±15 Return Gnd
J50: -15 Volts 3 Amps
J51: Earth Ground
MES1, MES3, MES6: DC 3Amp
MES2, MES4, MES5: DC
P1: Input Power 120vac
R76, R77: 100
RV3: 1k
RV4, RV5: 5k
R`1: 121
SW1: SW_SPST_Lamp
TR1: TRANSF6
U23, U28, U34: LM1085-ADJ
U24, U25, U26, U27, U29, U30, U31, U32, U33, U35, U36: Screw_Terminal

Connections:
Black: FL1.2 (P'), TR1.1, TR1.3
Blue: D18.2 (AC), TR1.7
Earth: J51.1
unnamed: C64.1, D11.K, D12.1 (+), U23.3 (VI)
unnamed: C64.2, C65.2, C66.2, C67.2, C68.2, C69.2, C70.2, D12.4 (-), D13.A, D15.4 (-), D16.A, MES2.1 (-), MES4.1 (-), RV3.2, RV3.3, RV4.2, RV4.3, U26., U31.
unnamed: C65.1, C66.1, D11.A, D13.K, MES1.2 (+), R`1.1, U23.2 (VO)
unnamed: C67.1, C68.1, D14.K, D15.1 (+), U28.3 (VI)
unnamed: C69.1, C70.1, D14.A, D16.K, MES3.2 (+), R76.1, U28.2 (VO)
unnamed: C71.1, C72.1, D17.K, D18.1 (+), U34.3 (VI)
unnamed: C71.2, C72.2, C73.2, C74.2, D18.4 (-), D19.A, MES6.1 (-), RV5.2, RV5.3
unnamed: C73.1, C74.1, D17.A, D19.K, MES5.2 (+), R77.1, U33., U34.2 (VO)
unnamed: CB1.1, P1.1 (AC_P)
unnamed: CB1.2, SW1.1, SW1.3 (L)
unnamed: FL1.1, SW1.2
unnamed: FL1.3 (N), P1.2 (AC_N), SW1.4 (L)
unnamed: J44.1, J44.2, J44.3, J44.7, J45.1, J45.2, J45.3, J45.7, U24., U25., U26., U27.
unnamed: J44.4, J44.5, J45.4, J45.5, U31., U32., U33.
unnamed: J44.8, J44.9, J45.8, J45.9, U29., U30.
unnamed: J44.6, J44.10, J45.6, J45.10, U35., U36.
unnamed: J46.1, U25.
unnamed: J47.1, U27.
unnamed: J48.1, U30.
unnamed: J49.1, U32.
unnamed: J50.1, U36.
unnamed: MES1.1 (-), MES2.2 (+), U24.
unnamed: MES3.1 (-), MES4.2 (+), U29.
unnamed: MES5.1 (-), MES6.2 (+), U35.
unnamed: R76.2, RV4.1, U28.1 (GND)
unnamed: R77.2, RV5.1, U34.1 (GND)
unnamed: RV3.1, R`1.2, U23.1 (GND)
Orange: FL1.4 (N'), TR1.2, TR1.4
Red: D18.3 (AC), TR1.8
Yellow: D12.3 (AC), D15.3 (AC), TR1.6
gray: D12.2 (AC), D15.2 (AC), TR1.5

Notes on the sheet:
Back Panel
LV300
Front Panel
LV30
