markeby/Synth32/Schematics/Power-Distrib.kicad_sch

## KiCad design Schematics/Power-Distrib.kicad_sch (2024-10-31)

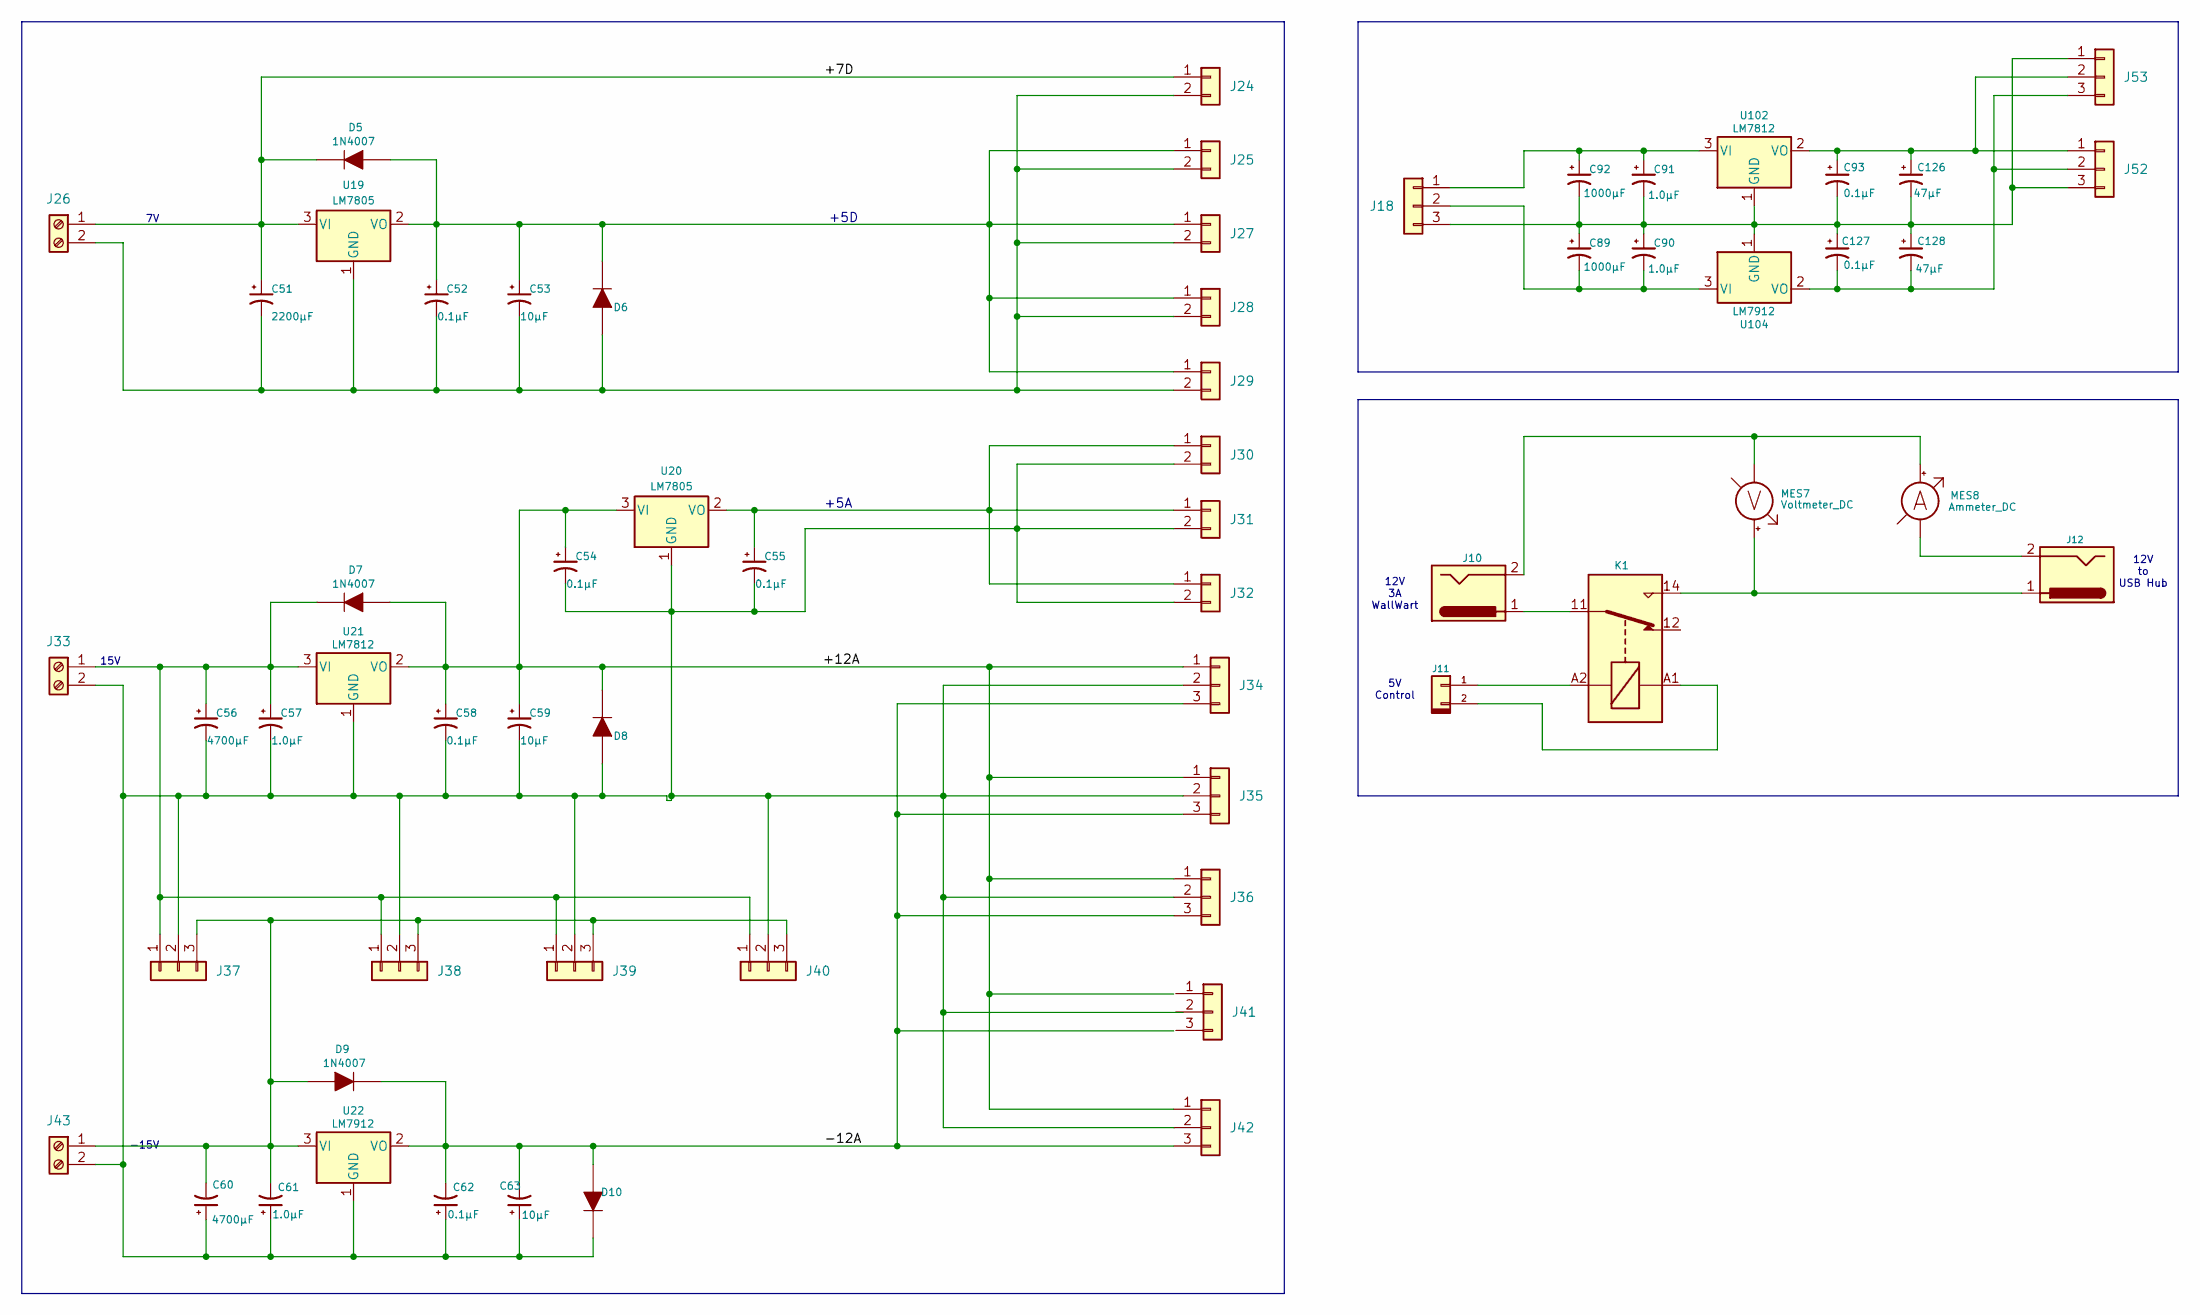
[picture p21: schematic Power-Distrib.kicad_sch]

Parts:
C51: 2200µF
C52, C54, C55, C58, C62, C93, C127: 0.1µF
C53, C59, C63: 10µF
C56, C60: 4700µF
C57, C61, C90, C91: 1.0µF
C89, C92: 1000µF
C126, C128: 47µF
D5, D6, D7, D8, D9, D10: 1N4007; DO-41; MPN 1N4007-T; Digi-Key_PN 1N4007DICT-ND
J10, J12: Jack-DC
J11, J24, J25, J27, J28, J29, J30, J31, J32: Conn_01x02
J18, J34, J35, J36, J37, J38, J39, J40, J41, J42, J52, J53: Conn_01x03
J26, J33, J43: Screw_Terminal_01x02
K1: Relay_SPDT
MES7: Voltmeter_DC
MES8: Ammeter_DC
U19, U20: LM7805
U21, U102: LM7812
U22, U104: LM7912

Connections:
+7D: C51.1, D5.K, J24.1, J26.1, U19.3 (VI)
+12A: C54.1, C58.1, C59.1, D7.A, D8.K, J34.1, J35.1, J36.1, J42.1, U20.3 (VI), U21.2 (VO)
-12A: C62.2, C63.2, D9.K, D10.A, J34.3, J35.3, J36.3, J42.3, U22.2 (VO)
unnamed: C51.2, C52.2, C53.2, D6.A, J24.2, J25.2, J26.2, J27.2, J28.2, J29.2, U19.1 (GND)
unnamed: C52.1, C53.1, D5.A, D6.K, J25.1, J27.1, J28.1, J29.1, U19.2 (VO)
unnamed: C54.2, C55.2, C56.2, C57.2, C58.2, C59.2, C60.1, C61.1, C62.1, C63.1, D8.A, D10.K, J30.2, J31.2, J32.2, J33.2, J34.2, J35.2, J36.2, J37.2, J38.2, J39.2, J40.2, J42.2, J43.2, U20.1 (GND), U21.1 (GND), U22.1 (GND)
unnamed: C55.1, J30.1, J31.1, J32.1, U20.2 (VO)
unnamed: C56.1, C57.1, D7.K, J33.1, J37.1, J38.1, J39.1, J40.1, U21.3 (VI)
unnamed: C60.2, C61.2, D9.A, J37.3, J38.3, J39.3, J40.3, J43.1, U22.3 (VI)
unnamed: C89.2, C90.2, J18.2, U104.3 (VI)
unnamed: C91.1, C92.1, J18.1, U102.3 (VI)
unnamed: C93.1, C126.1, J52.1, J53.2, U102.2 (VO)
unnamed: C89.1, C90.1, C91.2, C92.2, C93.2, C126.2, C127.1, C128.1, J18.3, J52.3, J53.1, U102.1 (GND), U104.1 (GND)
unnamed: C127.2, C128.2, J52.2, J53.3, U104.2 (VO)
unnamed: J10.1, K1.11
unnamed: J10.2, MES7.1 (-), MES8.2 (+)
unnamed: J11.1, K1.A2
unnamed: J11.2, K1.A1
unnamed: J12.1, K1.14, MES7.2 (+)
unnamed: J12.2, MES8.1 (-)

Notes on the sheet:
+5A
12V 3A WallWart
-15V
+5D
15V
5V Control
12V to USB Hub
