markeby/Synth32/Schematics/SpareBoards/Analog-52channel.kicad_sch

## KiCad design Schematics/SpareBoards/Analog-52channel.kicad_sch (2023-11-05)

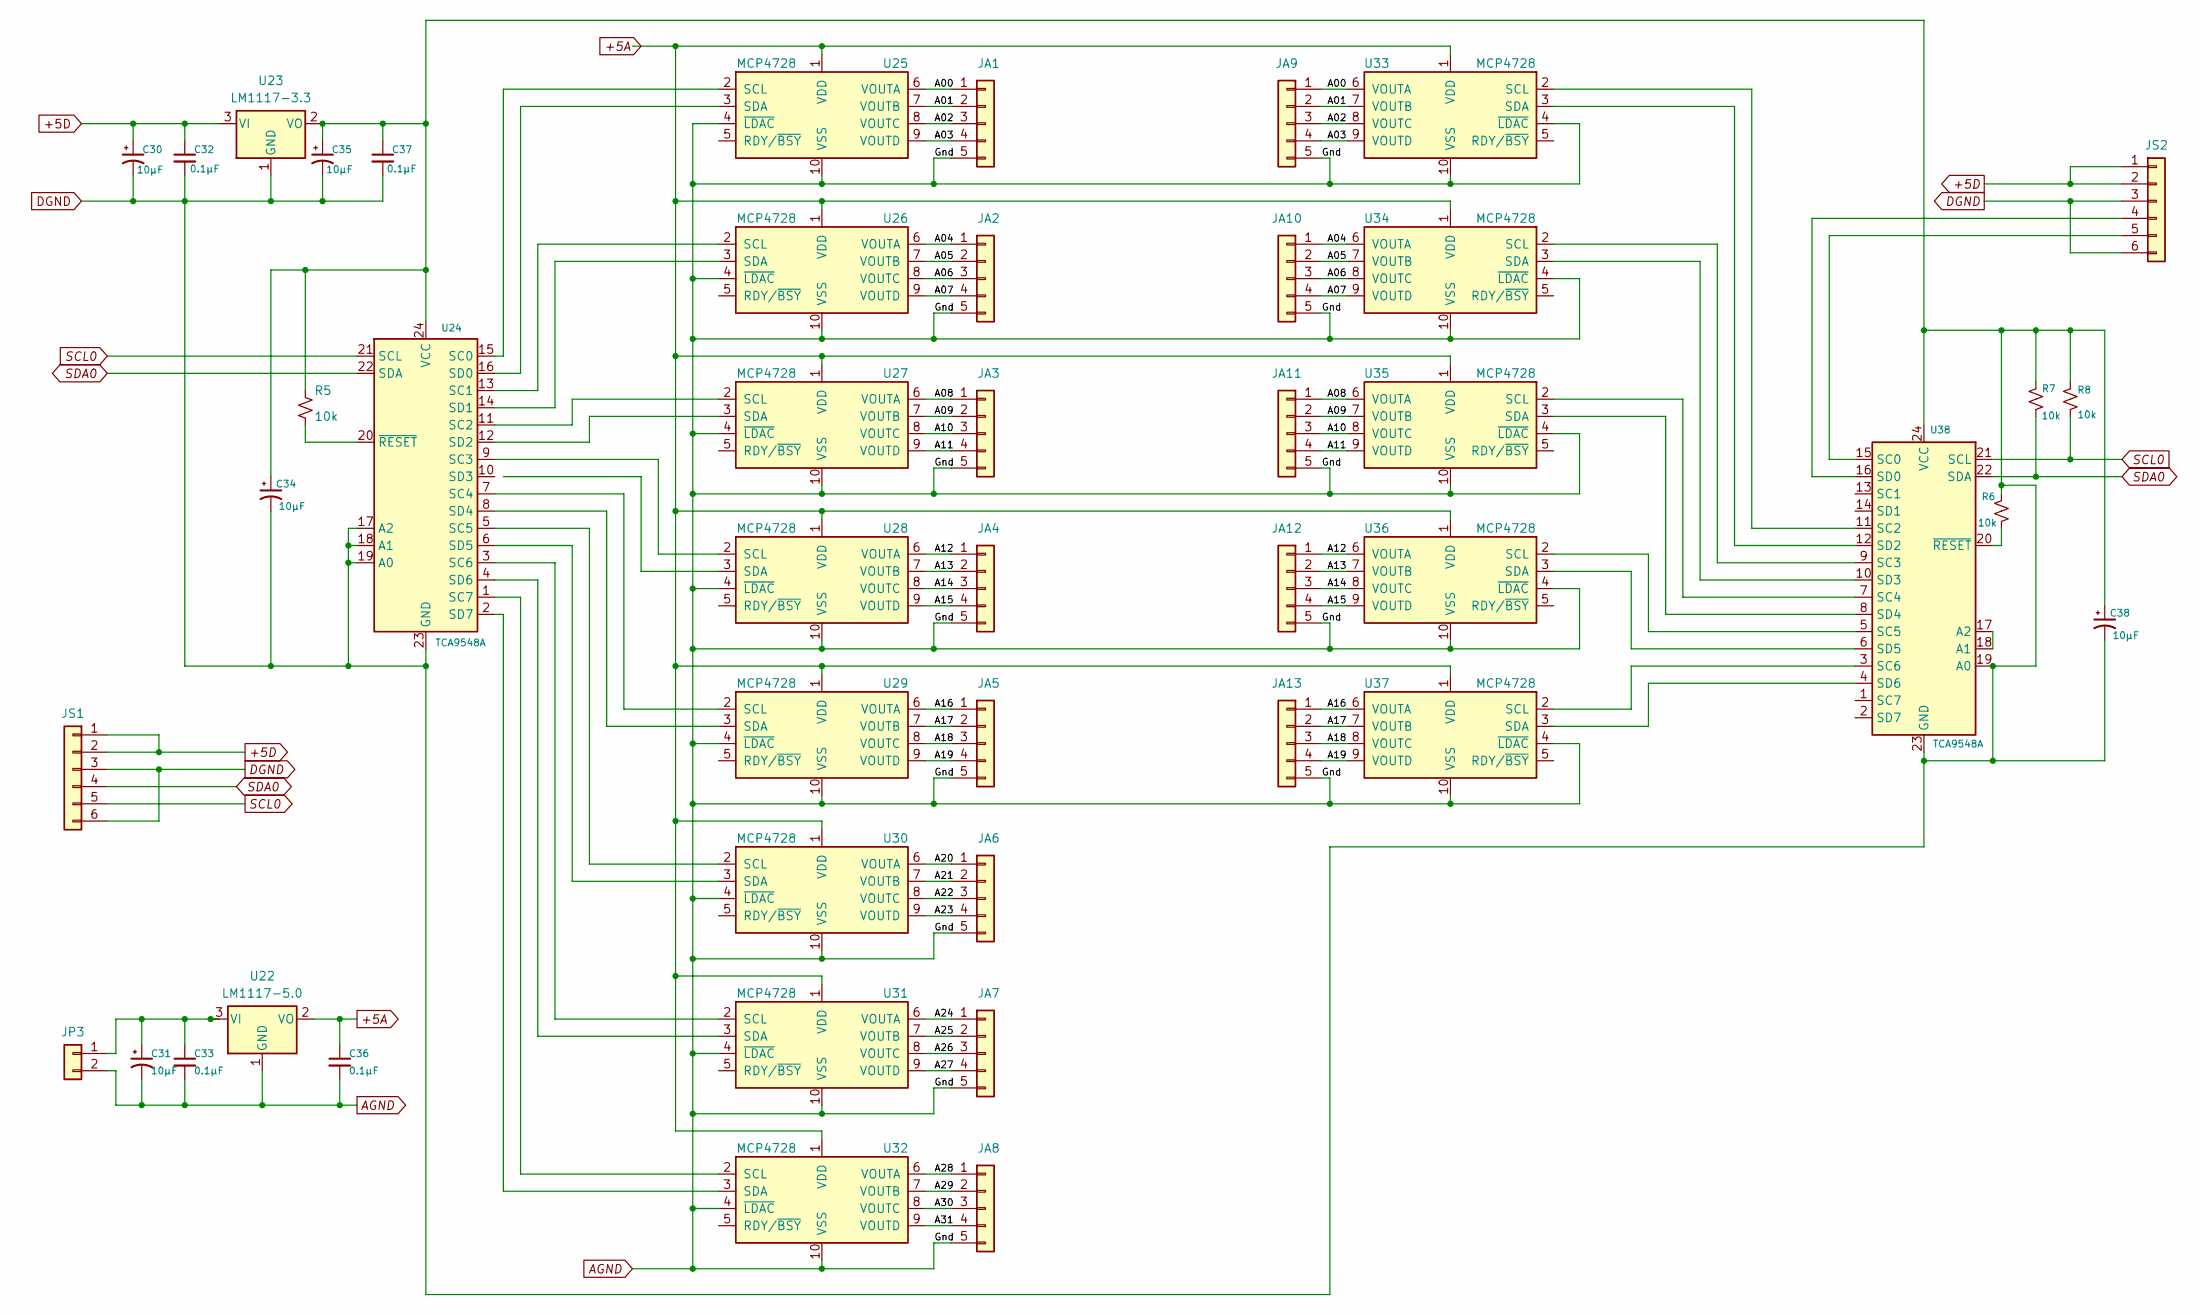
[picture p22: schematic Analog-52channel.kicad_sch]

Parts:
C30, C31, C34, C35, C38: 10µF
C32, C33, C36, C37: 0.1µF
JA1, JA9: DA00
JA2, JA10: DA04
JA3, JA11: DA08
JA4, JA12: DA12
JA5, JA13: DA16
JA6: DA20
JA7: DA24
JA8: DA38
JP3: From 12v Analog
JS1, JS2: To Compute #1
R5, R6, R7, R8: 10k
U22: LM1117-5.0
U23: LM1117-3.3
U24, U38: TCA9548A; SOIC-24W_7.5x15.4mm_P1.27mm
U25, U26, U27, U28, U29, U30, U31, U32, U33, U34, U35, U36, U37: MCP4728; MSOP-10_3x3mm_P0.5mm

Connections:
+5A: C36.1, U22.2 (VO), U25.1 (VDD), U26.1 (VDD), U27.1 (VDD), U28.1 (VDD), U29.1 (VDD), U30.1 (VDD), U31.1 (VDD), U32.1 (VDD), U33.1 (VDD), U34.1 (VDD), U35.1 (VDD), U36.1 (VDD), U37.1 (VDD)
+5D: C30.1, C32.1, JS1.1, JS1.2, JS2.1, JS2.2, U23.3 (VI)
A00: JA1.1, JA9.1, U25.6 (VOUTA), U33.6 (VOUTA)
A01: JA1.2, JA9.2, U25.7 (VOUTB), U33.7 (VOUTB)
A02: JA1.3, JA9.3, U25.8 (VOUTC), U33.8 (VOUTC)
A03: JA1.4, JA9.4, U25.9 (VOUTD), U33.9 (VOUTD)
A04: JA2.1, JA10.1, U26.6 (VOUTA), U34.6 (VOUTA)
A05: JA2.2, JA10.2, U26.7 (VOUTB), U34.7 (VOUTB)
A06: JA2.3, JA10.3, U26.8 (VOUTC), U34.8 (VOUTC)
A07: JA2.4, JA10.4, U26.9 (VOUTD), U34.9 (VOUTD)
A08: JA3.1, JA11.1, U27.6 (VOUTA), U35.6 (VOUTA)
A09: JA3.2, JA11.2, U27.7 (VOUTB), U35.7 (VOUTB)
A10: JA3.3, JA11.3, U27.8 (VOUTC), U35.8 (VOUTC)
A11: JA3.4, JA11.4, U27.9 (VOUTD), U35.9 (VOUTD)
A12: JA4.1, JA12.1, U28.6 (VOUTA), U36.6 (VOUTA)
A13: JA4.2, JA12.2, U28.7 (VOUTB), U36.7 (VOUTB)
A14: JA4.3, JA12.3, U28.8 (VOUTC), U36.8 (VOUTC)
A15: JA4.4, JA12.4, U28.9 (VOUTD), U36.9 (VOUTD)
A16: JA5.1, JA13.1, U29.6 (VOUTA), U37.6 (VOUTA)
A17: JA5.2, JA13.2, U29.7 (VOUTB), U37.7 (VOUTB)
A18: JA5.3, JA13.3, U29.8 (VOUTC), U37.8 (VOUTC)
A19: JA5.4, JA13.4, U29.9 (VOUTD), U37.9 (VOUTD)
A20: JA6.1, U30.6 (VOUTA)
A21: JA6.2, U30.7 (VOUTB)
A22: JA6.3, U30.8 (VOUTC)
A23: JA6.4, U30.9 (VOUTD)
A24: JA7.1, U31.6 (VOUTA)
A25: JA7.2, U31.7 (VOUTB)
A26: JA7.3, U31.8 (VOUTC)
A27: JA7.4, U31.9 (VOUTD)
A28: JA8.1, U32.6 (VOUTA)
A29: JA8.2, U32.7 (VOUTB)
A30: JA8.3, U32.8 (VOUTC)
A31: JA8.4, U32.9 (VOUTD)
AGND: C31.2, C33.2, C36.2, JA1.5, JA2.5, JA3.5, JA4.5, JA5.5, JA6.5, JA7.5, JA8.5, JA9.5, JA10.5, JA11.5, JA12.5, JA13.5, JP3.2, U22.1 (GND), U25.4 (~LDAC), U25.10 (VSS), U26.4 (~LDAC), U26.10 (VSS), U27.4 (~LDAC), U27.10 (VSS), U28.4 (~LDAC), U28.10 (VSS), U29.4 (~LDAC), U29.10 (VSS), U30.4 (~LDAC), U30.10 (VSS), U31.4 (~LDAC), U31.10 (VSS), U32.4 (~LDAC), U32.10 (VSS), U33.4 (~LDAC), U33.10 (VSS), U34.4 (~LDAC), U34.10 (VSS), U35.4 (~LDAC), U35.10 (VSS), U36.4 (~LDAC), U36.10 (VSS), U37.4 (~LDAC), U37.10 (VSS)
DGND: C30.2, C32.2, C34.1, C34.2, C35.1, C35.2, C37.1, C37.2, C38.1, C38.2, JS1.3, JS1.6, JS2.3, JS2.6, R5.1, R6.1, R7.1, R8.1, U23.1 (GND), U23.2 (VO), U24.17 (A2), U24.18 (A1), U24.19 (A0), U24.23 (GND), U24.24 (VCC), U38.19 (A0), U38.23 (GND), U38.24 (VCC)
unnamed: C31.1, C33.1, JP3.1, U22.3 (VI)
unnamed: JS2.4, U38.16 (SD0)
unnamed: JS2.5, U38.15 (SC0)
unnamed: R5.2, U24.20 (~RESET)
unnamed: R6.2, U38.20 (~RESET)
unnamed: U24.1 (SC7), U32.2 (SCL)
unnamed: U24.2 (SD7), U32.3 (SDA)
unnamed: U24.3 (SC6), U31.2 (SCL)
unnamed: U24.4 (SD6), U31.3 (SDA)
unnamed: U24.5 (SC5), U30.2 (SCL)
unnamed: U24.6 (SD5), U30.3 (SDA)
unnamed: U24.7 (SC4), U29.2 (SCL)
unnamed: U24.8 (SD4), U29.3 (SDA)
unnamed: U24.9 (SC3), U28.2 (SCL)
unnamed: U24.11 (SC2), U27.2 (SCL)
unnamed: U24.12 (SD2), U27.3 (SDA)
unnamed: U24.13 (SC1), U26.2 (SCL)
unnamed: U24.14 (SD1), U26.3 (SDA)
unnamed: U24.15 (SC0), U25.2 (SCL)
unnamed: U24.16 (SD0), U25.3 (SDA)
unnamed: U33.2 (SCL), U38.11 (SC2)
unnamed: U33.3 (SDA), U38.12 (SD2)
unnamed: U34.2 (SCL), U38.9 (SC3)
unnamed: U34.3 (SDA), U38.10 (SD3)
unnamed: U35.2 (SCL), U38.7 (SC4)
unnamed: U35.3 (SDA), U38.8 (SD4)
unnamed: U36.2 (SCL), U38.5 (SC5)
unnamed: U36.3 (SDA), U38.6 (SD5)
unnamed: U37.2 (SCL), U38.3 (SC6)
unnamed: U37.3 (SDA), U38.4 (SD6)
unnamed: U38.17 (A2), U38.18 (A1)
SCL0: JS1.5, R8.2, U24.21 (SCL), U38.21 (SCL)
SDA0: JS1.4, R7.2, U24.22 (SDA), U38.22 (SDA)
