markeby/Synth32/Schematics/SpareBoards/LFO-ICL8038.kicad_sch

## KiCad design Schematics/SpareBoards/LFO-ICL8038.kicad_sch (2023-11-05)

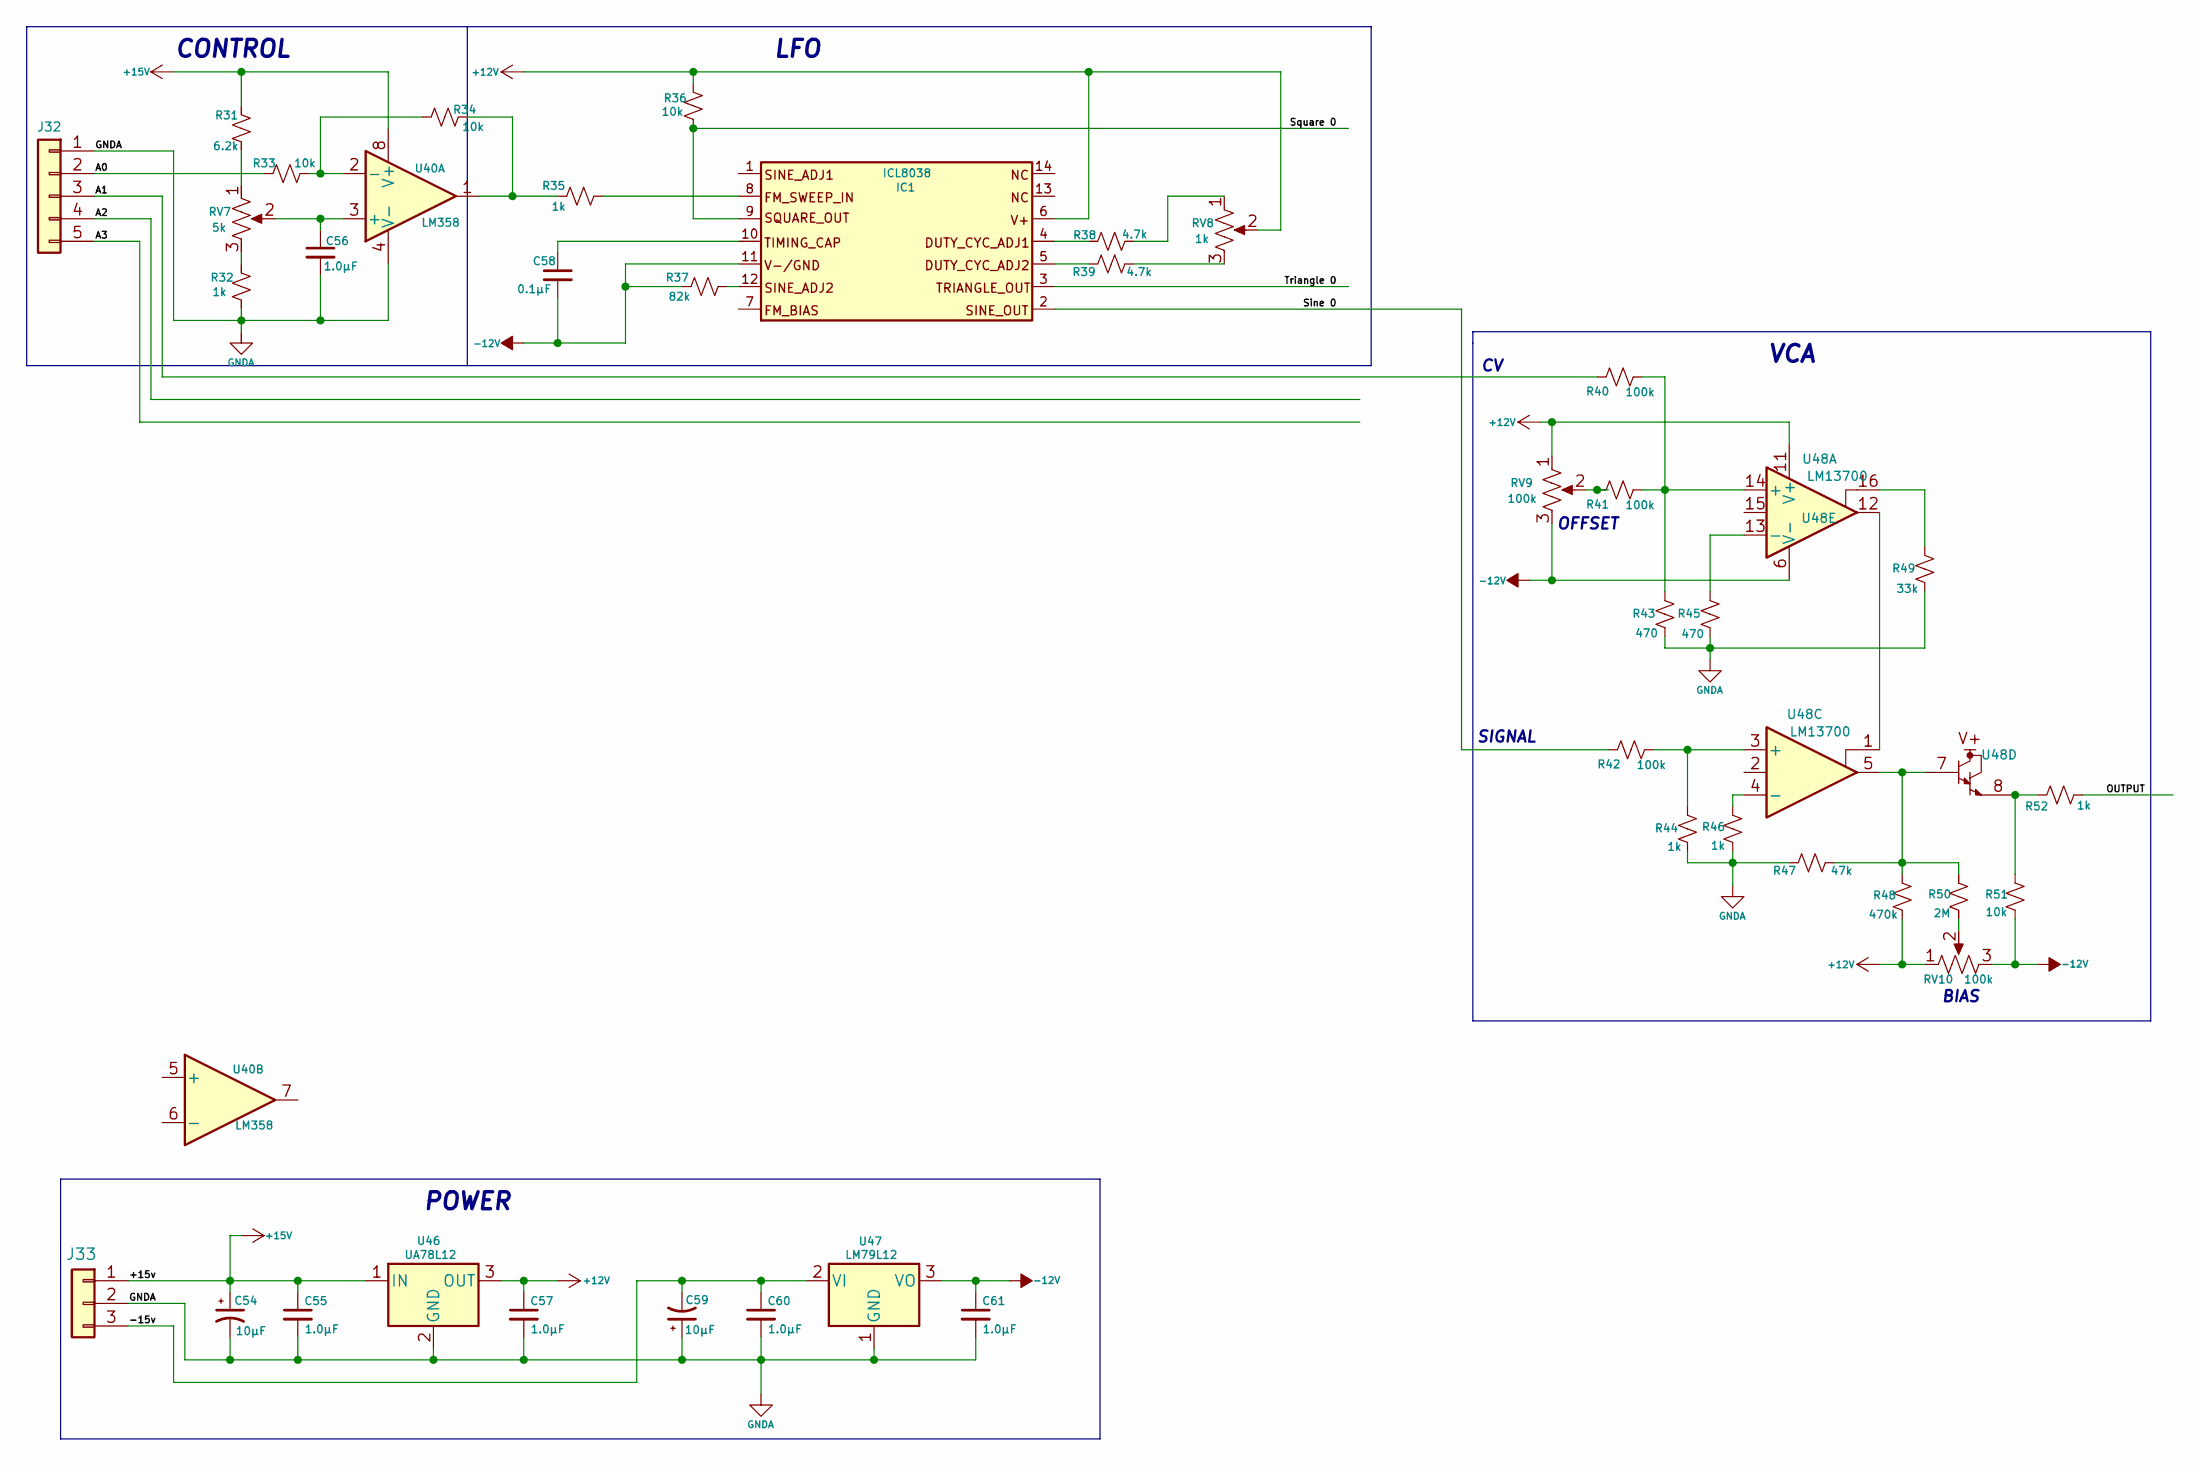
[picture p23: schematic LFO-ICL8038.kicad_sch]

Parts:
C54, C59: 10µF
C55, C56, C57, C60, C61: 1.0µF
C58: 0.1µF
IC1: ICL8038
J32: DA00
J33: Conn_01x03
R31: 6.2k
R32, R35, R44, R46, R52: 1k
R33, R34, R36, R51: 10k
R37: 82k
R38, R39: 4.7k
R40, R41, R42: 100k
R43, R45: 470
R47: 47k
R48: 470k
R49: 33k
R50: 2M
RV7: 5k
RV8: 1k
RV9, RV10: 100k
U40, U45: LM358
U46: UA78L12
U47: LM79L12; TO-220-3_Vertical
U48: LM13700

Connections:
+12V: C57.1, IC1.6, R36.2, R48.1, RV8.2, RV9.1, RV10.1, U46.3 (OUT), U48.11 (V+)
+15v: C54.1, C55.1, J33.1, R31.2, U45.8 (V+), U46.1 (IN)
-12V: C58.2, C61.1, IC1.11, R37.1, R51.1, RV9.3, RV10.3, U47.3 (VO), U48.6 (V-)
-15v: C59.2, C60.1, J33.3, U47.2 (VI)
A0: J32.2, R33.1
A1: J32.3, R40.1
A2: J32.4
A3: J32.5
GNDA: C54.2, C55.2, C56.2, C57.2, C59.1, C60.2, C61.2, J32.1, J33.2, R32.2, R43.1, R44.1, R45.1, R46.1, R47.1, R49.1, U45.4 (V-), U46.2 (GND), U47.1 (GND)
unnamed: C56.1, RV7.2, U40.3 (+)
unnamed: C58.1, IC1.10
unnamed: IC1.4, R38.1
unnamed: IC1.5, R39.1
unnamed: IC1.8, R35.2
unnamed: IC1.12, R37.2
unnamed: R31.1, RV7.1
unnamed: R32.1, RV7.3
unnamed: R33.2, R34.1, U40.2 (-)
unnamed: R34.2, R35.1, U40.1
unnamed: R38.2, RV8.1
unnamed: R39.2, RV8.3
unnamed: R40.2, R41.2, R43.2, U48.14 (+)
unnamed: R41.1, RV9.2
unnamed: R42.2, R44.2, U48.3 (+)
unnamed: R45.2, U48.13 (-)
unnamed: R46.2, U48.4 (-)
unnamed: R47.2, R48.2, R50.2, U48.5, U48.7
unnamed: R49.2, U48.16
unnamed: R50.1, RV10.2
unnamed: R51.2, R52.1, U48.8
unnamed: U48.1, U48.12
OUTPUT: R52.2
Sine 0: IC1.2, R42.1
Square 0: IC1.9, R36.1
Triangle 0: IC1.3

Notes on the sheet:
OFFSET
VCA
LFO
SIGNAL
BIAS
POWER
CONTROL
