markeby/Synth32/Schematics/SpareBoards/Noise.kicad_sch

## KiCad design Schematics/SpareBoards/Noise.kicad_sch (2024-11-26)

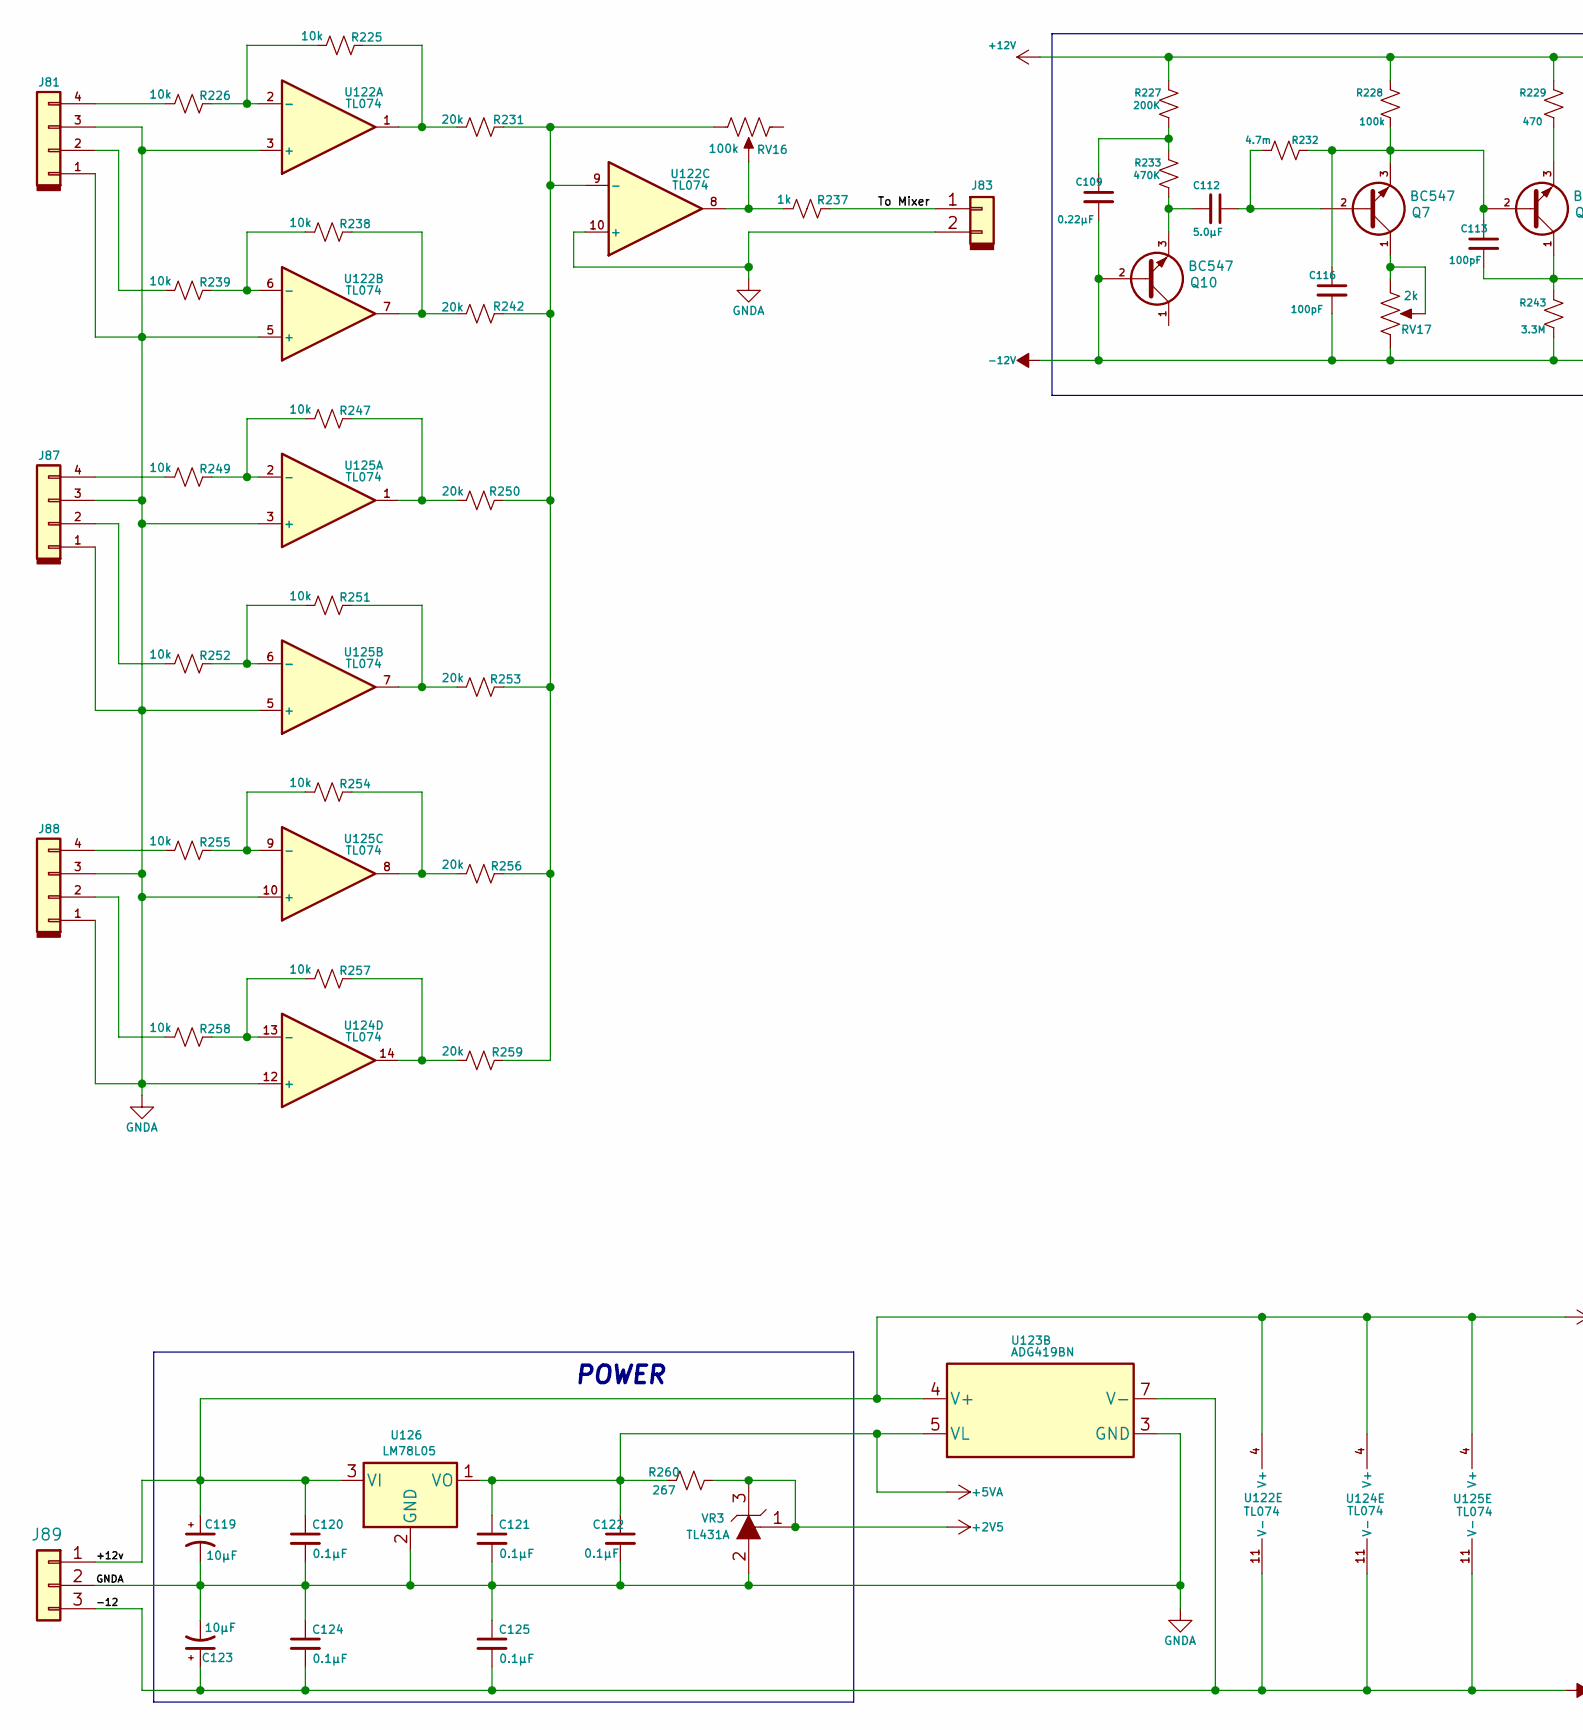
[picture p24: schematic Noise.kicad_sch, part in row 1, column 1]

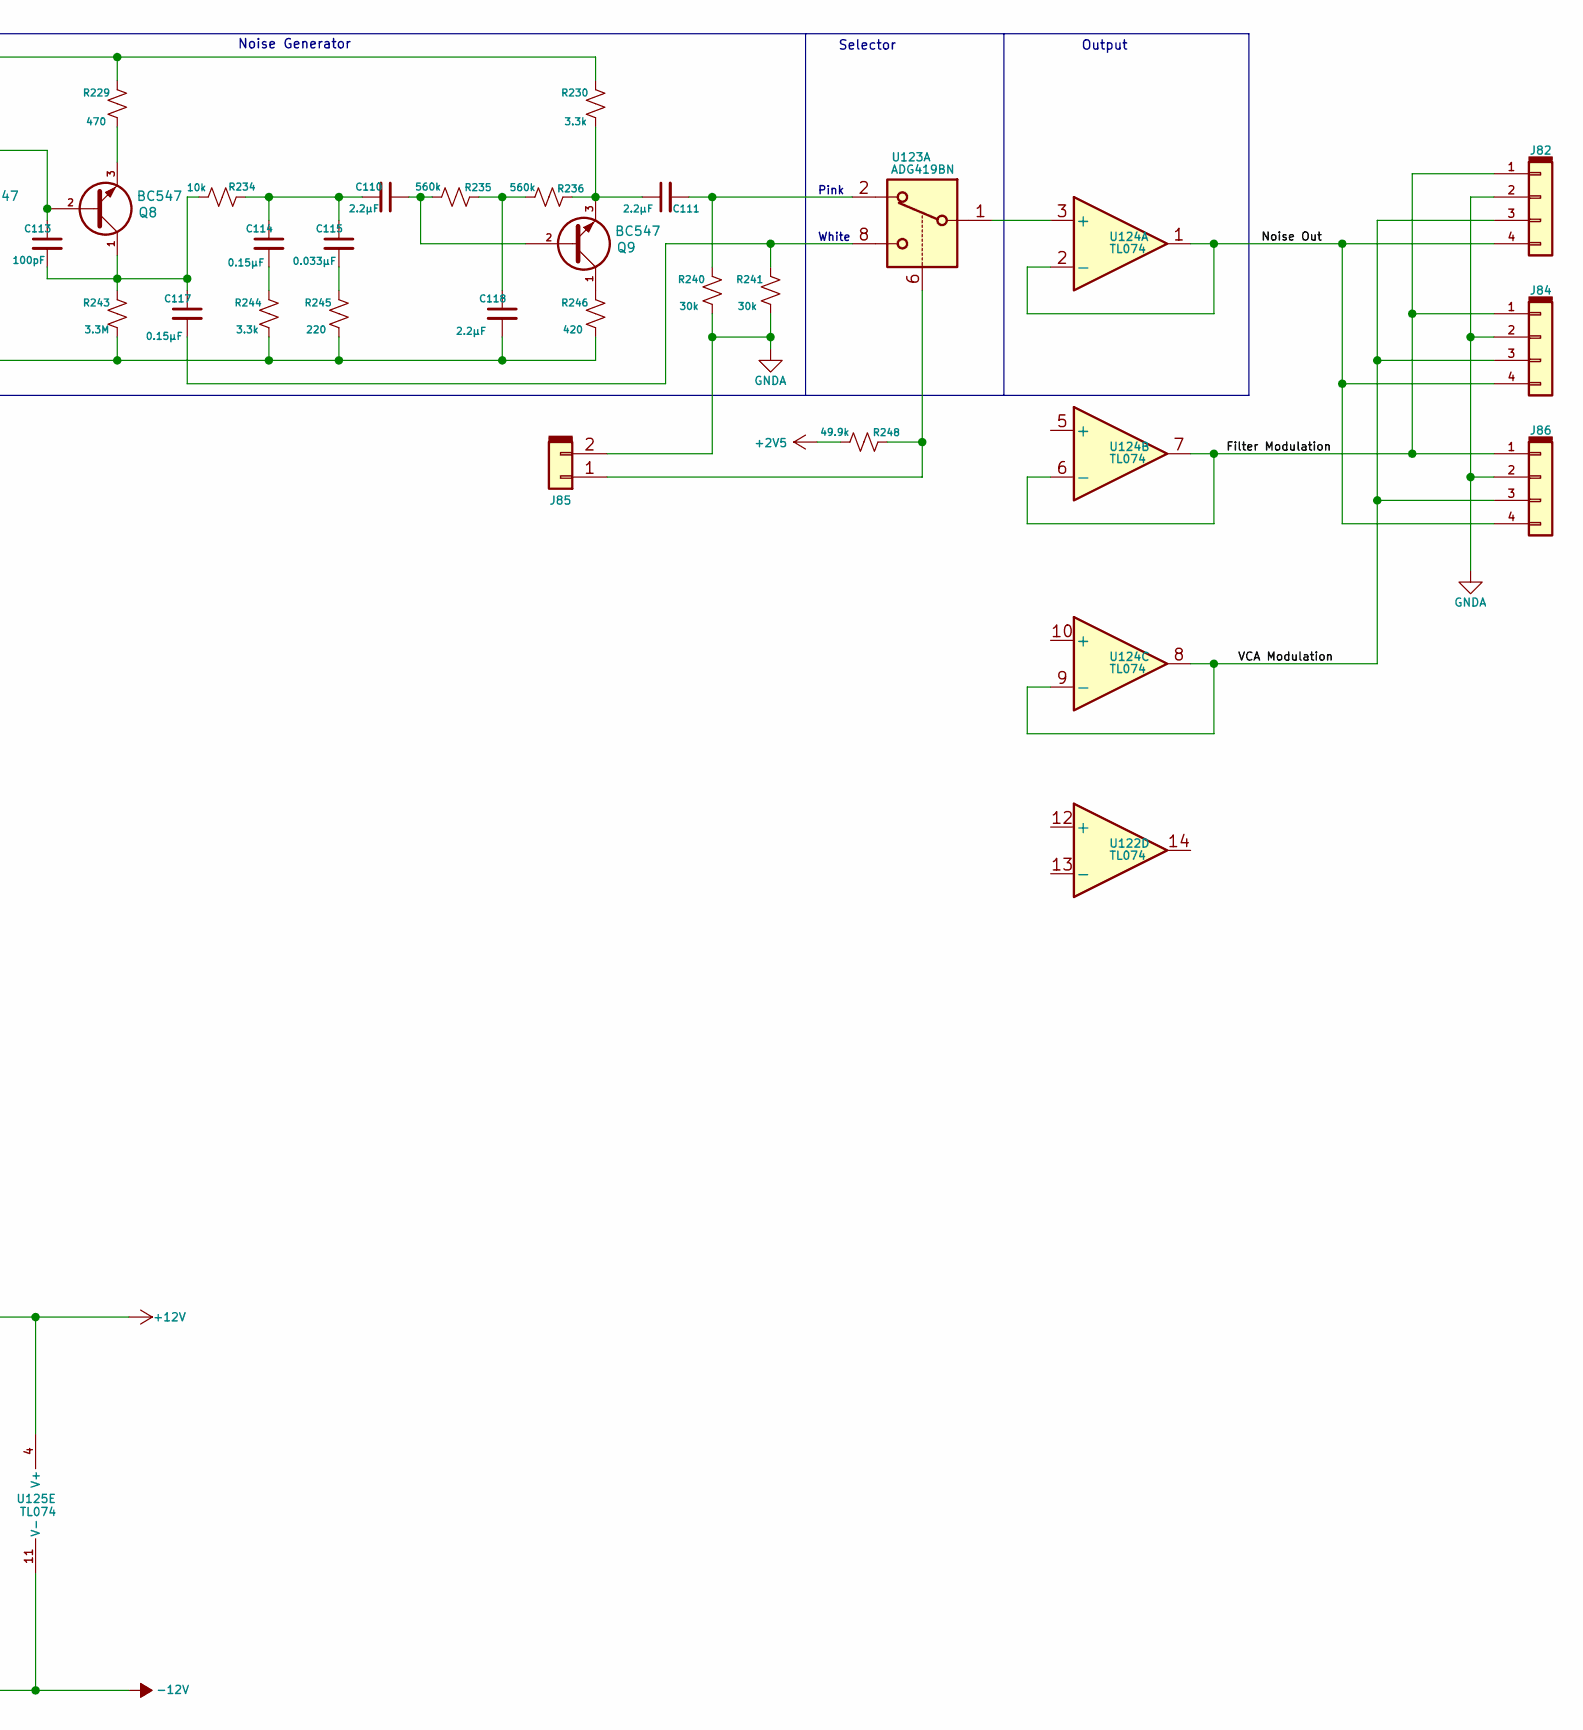
[picture p25: schematic Noise.kicad_sch, part in row 1, column 2]

Parts:
C109: 0.22µF
C110, C111, C118: 2.2µF
C112: 5.0µF
C113, C116: 100pF
C114, C117: 0.15µF
C115: 0.033µF
C119, C123: 10µF
C120, C121, C122, C124, C125: 0.1µF
J81, J82, J84, J86, J87, J88: Conn_01x04
J83, J85: Conn_01x02
J89: Conn_01x03
Q7, Q8, Q9, Q10: BC547; TO-92_Inline
R225, R226, R234, R238, R239, R247, R249, R251, R252, R254, R255, R257, R258: 10k
R227: 200K
R228: 100k
R229: 470
R230, R244: 3.3k
R231, R242, R250, R253, R256, R259: 20k
R232: 4.7m
R233: 470K
R235, R236: 560k
R237: 1k
R240, R241: 30k
R243: 3.3M
R245: 220
R246: 420
R248: 49.9k
R260: 267
RV16: 100k
RV17: 2k
U122, U124, U125: TL074
U123: ADG419BN; DIP-8_W7.62mm
U126: LM78L05; TO-92_Inline
VR3: TL431A; TO-92-3_Formed_Leads; MPN TL431CLPM; Digi-Key_PN 296-26717-1-ND

Connections:
+2V5: R248.2, R260.2, VR3.1 (REF), VR3.3 (K)
+5VA: C121.1, C122.1, R260.1, U123.5 (VL), U126.1 (VO)
+12v: C119.1, C120.1, J89.1, R227.1, R228.1, R229.1, R230.1, U122.4 (V+), U123.4 (V+), U124.4 (V+), U125.4 (V+), U126.3 (VI)
-12V: C109.2, C116.2, C118.2, C123.1, C124.2, C125.2, J89.3, Q10.2 (B), R243.2, R244.2, R245.2, R246.2, RV17., U122.11 (V-), U123.7 (V-), U124.11 (V-), U125.11 (V-)
Filter Modulation: J82.1, J84.1, J86.1, U124.6 (-), U124.7
GNDA: C119.2, C120.2, C121.2, C122.2, C123.2, C124.1, C125.1, J81.1, J81.3, J82.2, J83.2, J84.2, J85.2, J86.2, J87.1, J87.3, J88.1, J88.3, J89.2, R240.2, R241.2, U122.3 (+), U122.5 (+), U122.10 (+), U123.3 (GND), U124.12 (+), U125.3 (+), U125.5 (+), U125.10 (+), U126.2 (GND), VR3.2 (A)
unnamed: C109.1, R227.2, R233.1
unnamed: C110.1, Q9.2 (B), R235.2
unnamed: C110.2, C114.1, C115.1, R234.1
unnamed: C111.1, Q9.3 (E), R230.2, R236.1
unnamed: C111.2, R240.1, U123.2
unnamed: C112.1, Q7.2 (B), R232.2
unnamed: C112.2, Q10.3 (E), R233.2
unnamed: C113.1, C116.1, Q7.3 (E), Q8.2 (B), R228.2, R232.1
unnamed: C113.2, C117.1, Q8.1 (C), R234.2, R243.1
unnamed: C114.2, R244.1
unnamed: C115.2, R245.1
unnamed: C117.2, R241.1, U123.8
unnamed: C118.1, R235.1, R236.2
unnamed: J81.2, R239.1
unnamed: J81.4, R226.1
unnamed: J85.1, R248.1, U123.6
unnamed: J87.2, R252.1
unnamed: J87.4, R249.1
unnamed: J88.2, R258.1
unnamed: J88.4, R255.1
unnamed: Q7.1 (C), RV17.
unnamed: Q8.3 (E), R229.2
unnamed: Q9.1 (C), R246.1
unnamed: R225.1, R226.2, U122.2 (-)
unnamed: R225.2, R231.1, U122.1
unnamed: R231.2, R242.2, R250.2, R253.2, R256.2, R259.2, RV16., U122.9 (-)
unnamed: R237.1, RV16., U122.8
unnamed: R238.1, R239.2, U122.6 (-)
unnamed: R238.2, R242.1, U122.7
unnamed: R247.1, R249.2, U125.2 (-)
unnamed: R247.2, R250.1, U125.1
unnamed: R251.1, R252.2, U125.6 (-)
unnamed: R251.2, R253.1, U125.7
unnamed: R254.1, R255.2, U125.9 (-)
unnamed: R254.2, R256.1, U125.8
unnamed: R257.1, R258.2, U124.13 (-)
unnamed: R257.2, R259.1, U124.14
unnamed: U123.1, U124.3 (+)
Noise Out: J82.4, J84.4, J86.4, U124.1, U124.2 (-)
To Mixer: J83.1, R237.2
VCA Modulation: J82.3, J84.3, J86.3, U124.8, U124.9 (-)

Notes on the sheet:
White
Output
POWER
Selector
Pink
Noise Generator
