markeby/Synth32/Schematics/SpareBoards/NoiseFilter.kicad_sch

## KiCad design Schematics/SpareBoards/NoiseFilter.kicad_sch (2024-07-26)

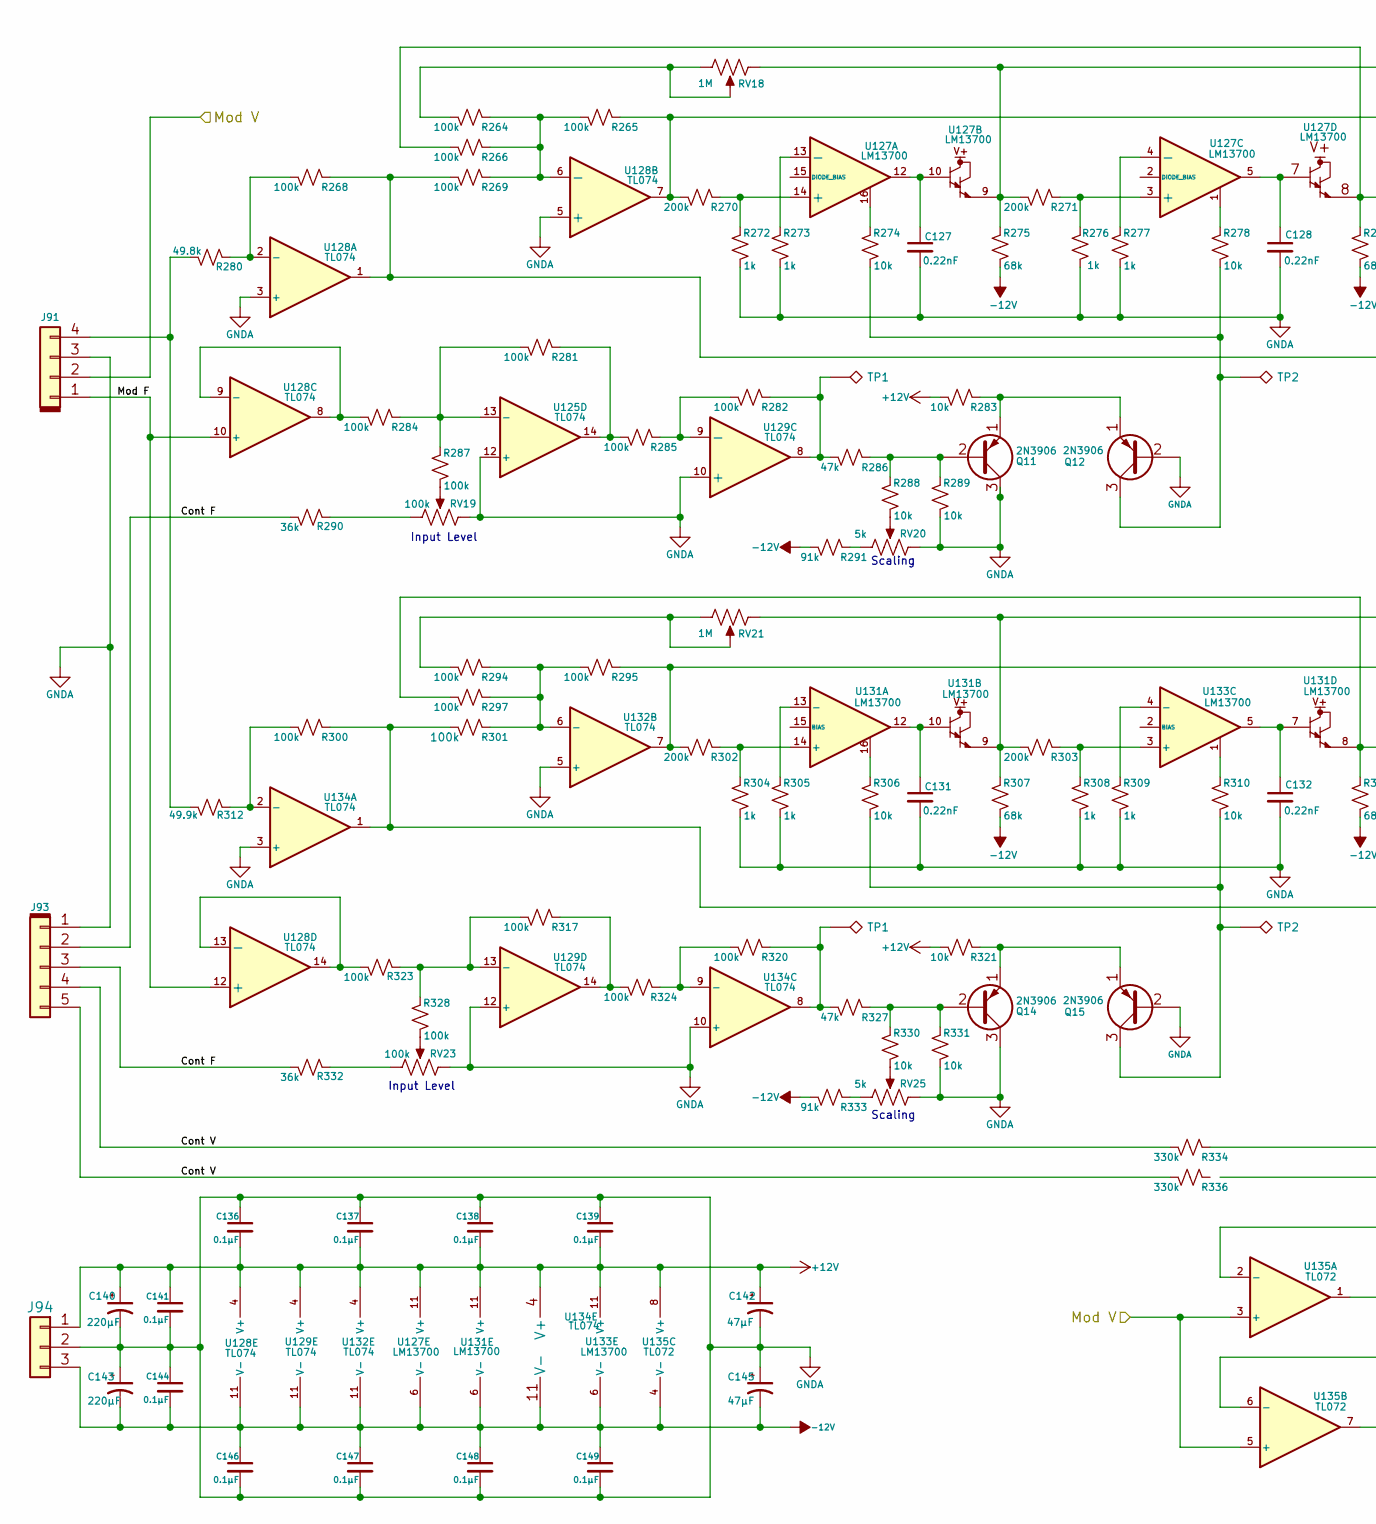
[picture p26: schematic NoiseFilter.kicad_sch, part in row 1, column 1]

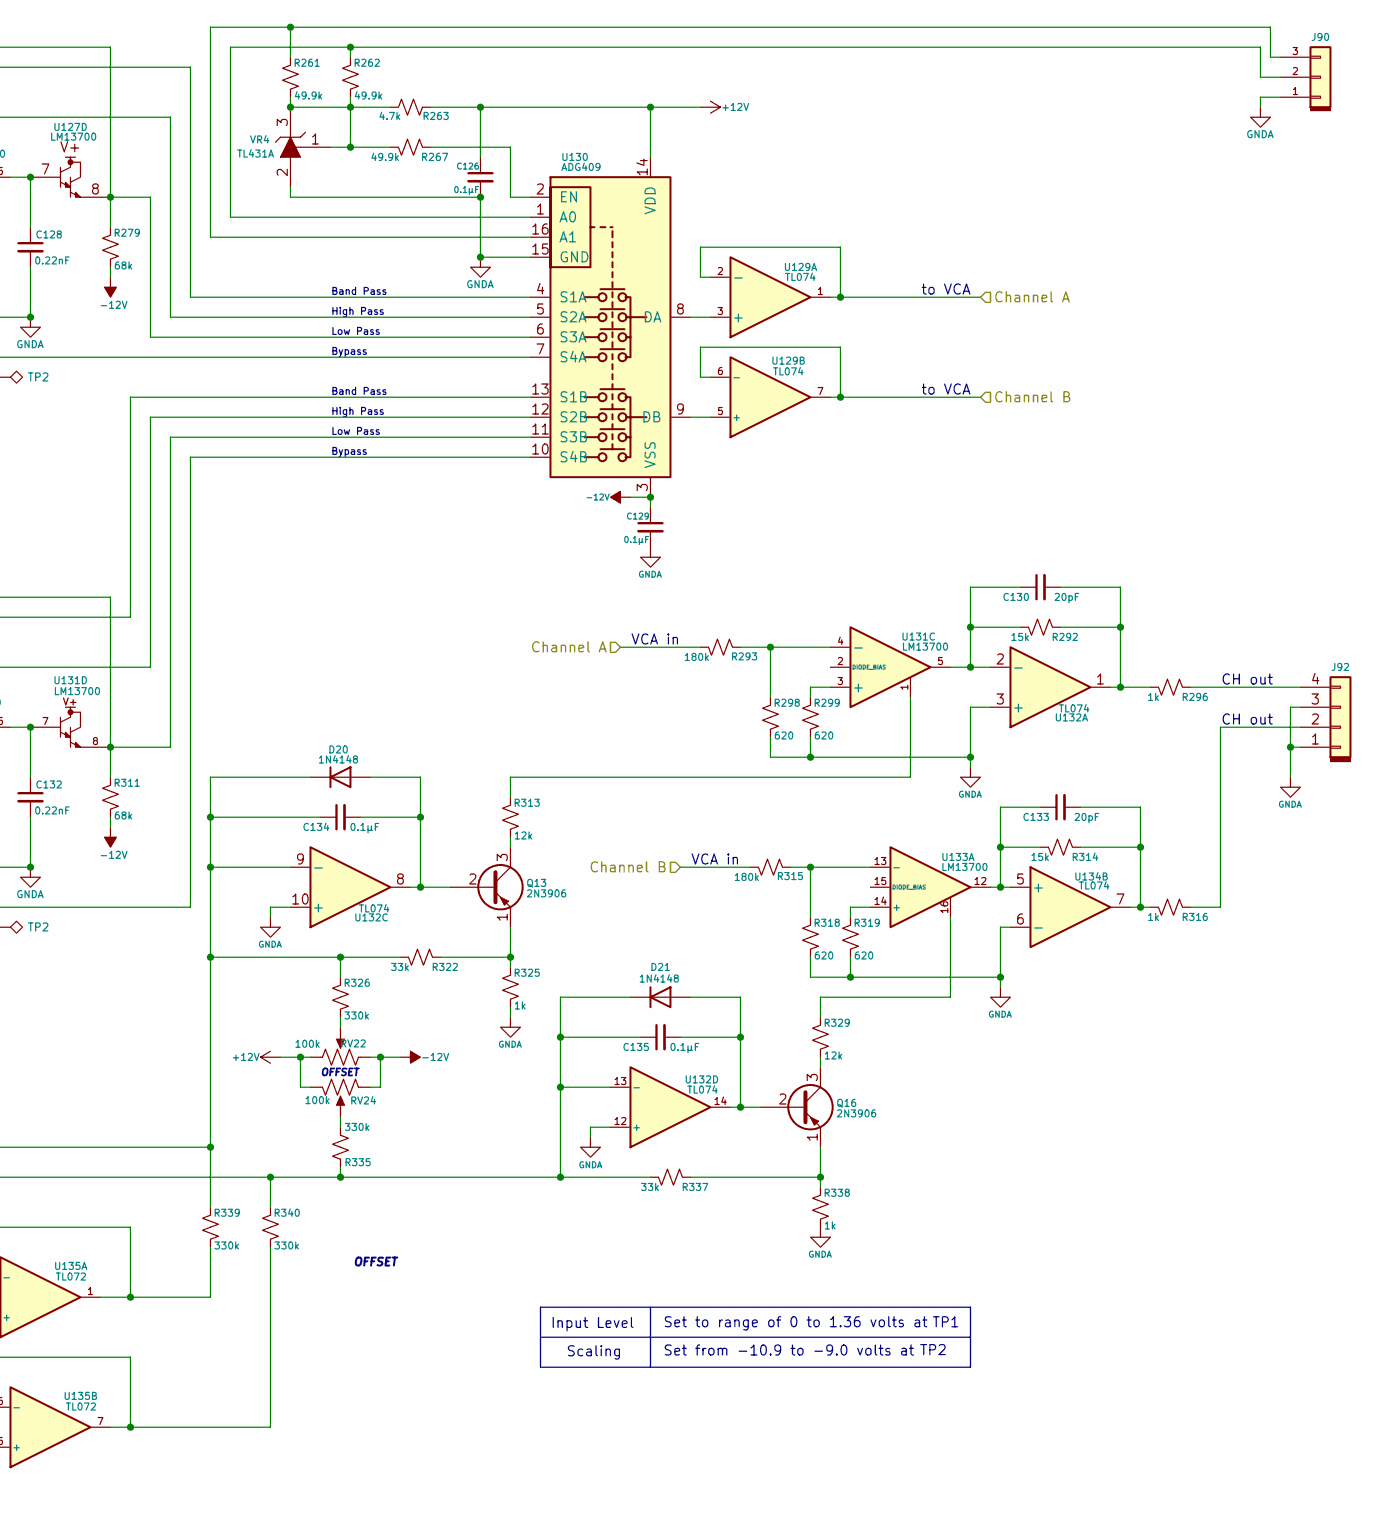
[picture p27: schematic NoiseFilter.kicad_sch, part in row 1, column 2]

Parts:
C126, C129, C134, C135, C136, C137, C138, C139, C141, C144, C146, C147, C148, C149: 0.1µF
C127, C128, C131, C132: 0.22nF
C130, C133: 20pF
C140, C143: 220µF
C142, C145: 47µF
D20, D21: 1N4148; D_DO-35_SOD27_P7.62mm_Horizontal
J90, J94: Conn_01x03
J91, J92: Conn_01x04
J93: Conn_01x05
Q11, Q12, Q13, Q14, Q15, Q16: 2N3906; TO-92_Inline
R261, R262, R267, R312: 49.9k
R263: 4.7k
R264, R265, R266, R268, R269, R281, R282, R284, R285, R287, R294, R295, R297, R300, R301, R317, R320, R323, R324, R328: 100k
R270, R271, R302, R303: 200k
R272, R273, R276, R277, R296, R304, R305, R308, R309, R316, R325, R338: 1k
R274, R278, R283, R288, R289, R306, R310, R321, R330, R331: 10k
R275, R279, R307, R311: 68k
R280: 49.8k
R286, R327: 47k
R290, R332: 36k
R291, R333: 91k
R292, R314: 15k
R293, R315: 180k
R298, R299, R318, R319: 620
R313, R329: 12k
R322, R337: 33k
R326, R334, R335, R336, R339, R340: 330k
RV18, RV21: 1M
RV19, RV22, RV23, RV24: 100k
RV20, RV25: 5k
TP1, TP3: TP1
TP2, TP4: TP2
U125, U128, U129, U132, U134: TL074
U127, U131, U133: LM13700
U130: ADG409
U135: TL072
VR4: TL431A; TO-92-3_Formed_Leads; MPN TL431CLPM; Digi-Key_PN 296-26717-1-ND

Connections:
+12V: C126.1, C136.2, C137.2, C138.2, C139.2, C140.1, C141.1, C142.1, J94.1, R263.2, R283.2, R321.2, RV22., RV24., U127.11 (V+), U128.4 (V+), U129.4 (V+), U130.14 (VDD), U131.11 (V+), U132.4 (V+), U133.11 (V+), U134.4 (V+), U135.8 (V+)
-12V: C129.1, C143.2, C144.2, C145.2, C146.1, C147.1, C148.1, C149.1, J94.3, R275.2, R279.2, R291.2, R307.2, R311.2, R333.2, RV22., RV24., U127.6 (V-), U128.11 (V-), U129.11 (V-), U130.3 (VSS), U131.6 (V-), U132.11 (V-), U133.6 (V-), U134.11 (V-), U135.4 (V-)
Channel A: R293.2, U129.1, U129.2 (-)
Channel B: R315.2, U129.6 (-), U129.7
Cont F: J93.2, J93.3, R290.2, R332.2
Cont V: J93.4, J93.5, R334.2, R336.2
GNDA: C126.2, C127.2, C128.2, C129.2, C131.2, C132.2, C136.1, C137.1, C138.1, C139.1, C140.2, C141.2, C142.2, C143.1, C144.1, C145.1, C146.2, C147.2, C148.2, C149.2, J90.1, J91.3, J92.1, J92.3, J93.1, J94.2, Q11.3 (C), Q12.2 (B), Q14.3 (C), Q15.2 (B), R272.2, R273.2, R276.2, R277.2, R289.2, R298.2, R299.2, R304.2, R305.2, R308.2, R309.2, R318.2, R319.2, R325.2, R331.2, R338.2, RV19., RV20., RV23., RV25., U125.12 (+), U128.3 (+), U128.5 (+), U129.10 (+), U129.12 (+), U130.15 (GND), U132.3 (+), U132.5 (+), U132.10 (+), U132.12 (+), U134.3 (+), U134.6 (-), U134.10 (+), VR4.2 (A)
Mod F: J91.1, U128.10 (+), U128.12 (+)
Mod V: J91.2
Mod V: U135.3 (+), U135.5 (+)
unnamed: C127.1, U127.10, U127.12
unnamed: C128.1, U127.5, U127.7
unnamed: C130.1, R292.2, U131.5, U132.2 (-)
unnamed: C130.2, R292.1, R296.2, U132.1
unnamed: C131.1, U131.10, U131.12
unnamed: C132.1, U131.7, U133.5
unnamed: C133.1, R314.2, U133.12, U134.5 (+)
unnamed: C133.2, R314.1, R316.2, U134.7
unnamed: C134.1, D20.1 (K), R322.2, R326.1, R334.1, R339.1, U132.9 (-)
unnamed: C134.2, D20.2 (A), Q13.2 (B), U132.8
unnamed: C135.1, D21.1 (K), R335.1, R337.2, R340.1, U132.13 (-)
unnamed: C135.2, D21.2 (A), Q16.2 (B), U132.14
unnamed: J90.2, R262.1, U130.1 (A0)
unnamed: J90.3, R261.1, U130.16 (A1)
unnamed: J91.4, R280.2, R312.2
unnamed: J92.2, R316.1
unnamed: J92.4, R296.1
unnamed: Q11.1 (E), Q12.1 (E), R283.1
unnamed: Q11.2 (B), R286.1, R288.1, R289.1
unnamed: Q12.3 (C), R274.2, R278.2, TP2.1
unnamed: Q13.1 (E), R322.1, R325.1
unnamed: Q13.3 (C), R313.2
unnamed: Q14.1 (E), Q15.1 (E), R321.1
unnamed: Q14.2 (B), R327.1, R330.1, R331.1
unnamed: Q15.3 (C), R306.2, R310.2, TP4.1
unnamed: Q16.1 (E), R337.1, R338.1
unnamed: Q16.3 (C), R329.2
unnamed: R261.2, R262.2, R263.1, R267.2, VR4.1 (REF), VR4.3 (K)
unnamed: R264.1, R265.2, R266.1, R269.1, U128.6 (-)
unnamed: R264.2, RV18.
unnamed: R265.1, R270.2, U128.7, U130.5 (S2A)
unnamed: R266.2, R279.1, U127.8, U130.6 (S3A)
unnamed: R267.1, U130.2 (EN)
unnamed: R268.1, R269.2, U128.1, U130.7 (S4A)
unnamed: R268.2, R280.1, U128.2 (-)
unnamed: R270.1, R272.1, U127.14 (+)
unnamed: R271.1, R276.1, U127.3 (+)
unnamed: R271.2, R275.1, RV18., U127.9, U130.4 (S1A)
unnamed: R273.1, U127.13 (-)
unnamed: R274.1, U127.16
unnamed: R277.1, U127.4 (-)
unnamed: R278.1, U127.1
unnamed: R281.1, R285.2, U125.14
unnamed: R281.2, R284.1, R287.1, U125.13 (-)
unnamed: R282.1, R286.2, TP1.1, U129.8
unnamed: R282.2, R285.1, U129.9 (-)
unnamed: R284.2, U128.8, U128.9 (-)
unnamed: R287.2, RV19.
unnamed: R288.2, RV20.
unnamed: R290.1, RV19.
unnamed: R291.1, RV20.
unnamed: R293.1, R298.1, U131.4 (-)
unnamed: R294.1, R295.2, R297.1, R301.1, U132.6 (-)
unnamed: R294.2, RV21.
unnamed: R295.1, R302.2, U130.12 (S2B), U132.7
unnamed: R297.2, R311.1, U130.11 (S3B), U131.8
unnamed: R299.1, U131.3 (+)
unnamed: R300.1, R301.2, U130.10 (S4B), U134.1
unnamed: R300.2, R312.1, U134.2 (-)
unnamed: R302.1, R304.1, U131.14 (+)
unnamed: R303.1, R308.1, U133.3 (+)
unnamed: R303.2, R307.1, RV21., U130.13 (S1B), U131.9
unnamed: R305.1, U131.13 (-)
unnamed: R306.1, U131.16
unnamed: R309.1, U133.4 (-)
unnamed: R310.1, U133.1
unnamed: R313.1, U131.1
unnamed: R315.1, R318.1, U133.13 (-)
unnamed: R317.1, R324.2, U129.14
unnamed: R317.2, R323.1, R328.1, U129.13 (-)
unnamed: R319.1, U133.14 (+)
unnamed: R320.1, R327.2, TP3.1, U134.8
unnamed: R320.2, R324.1, U134.9 (-)
unnamed: R323.2, U128.13 (-), U128.14
unnamed: R326.2, RV22.
unnamed: R328.2, RV23.
unnamed: R329.1, U133.16
unnamed: R330.2, RV25.
unnamed: R332.1, RV23.
unnamed: R333.1, RV25.
unnamed: R335.2, RV24.
unnamed: R339.2, U135.1, U135.2 (-)
unnamed: R340.2, U135.6 (-), U135.7
unnamed: U129.3 (+), U130.8 (DA)
unnamed: U129.5 (+), U130.9 (DB)

Notes on the sheet:
OFFSET
to VCA
VCA in
CH out
Low Pass
Set from -10.9 to -9.0 volts at
Input Level
Scaling
Bypass
High Pass
Band Pass
Set to range of 0 to 1.36 volts at
TP1
TP2
