markeby/Synth32/Schematics/SpareBoards/Osc_4_ifc.kicad_sch

## KiCad design Schematics/SpareBoards/Osc_4_ifc.kicad_sch (2024-10-31)

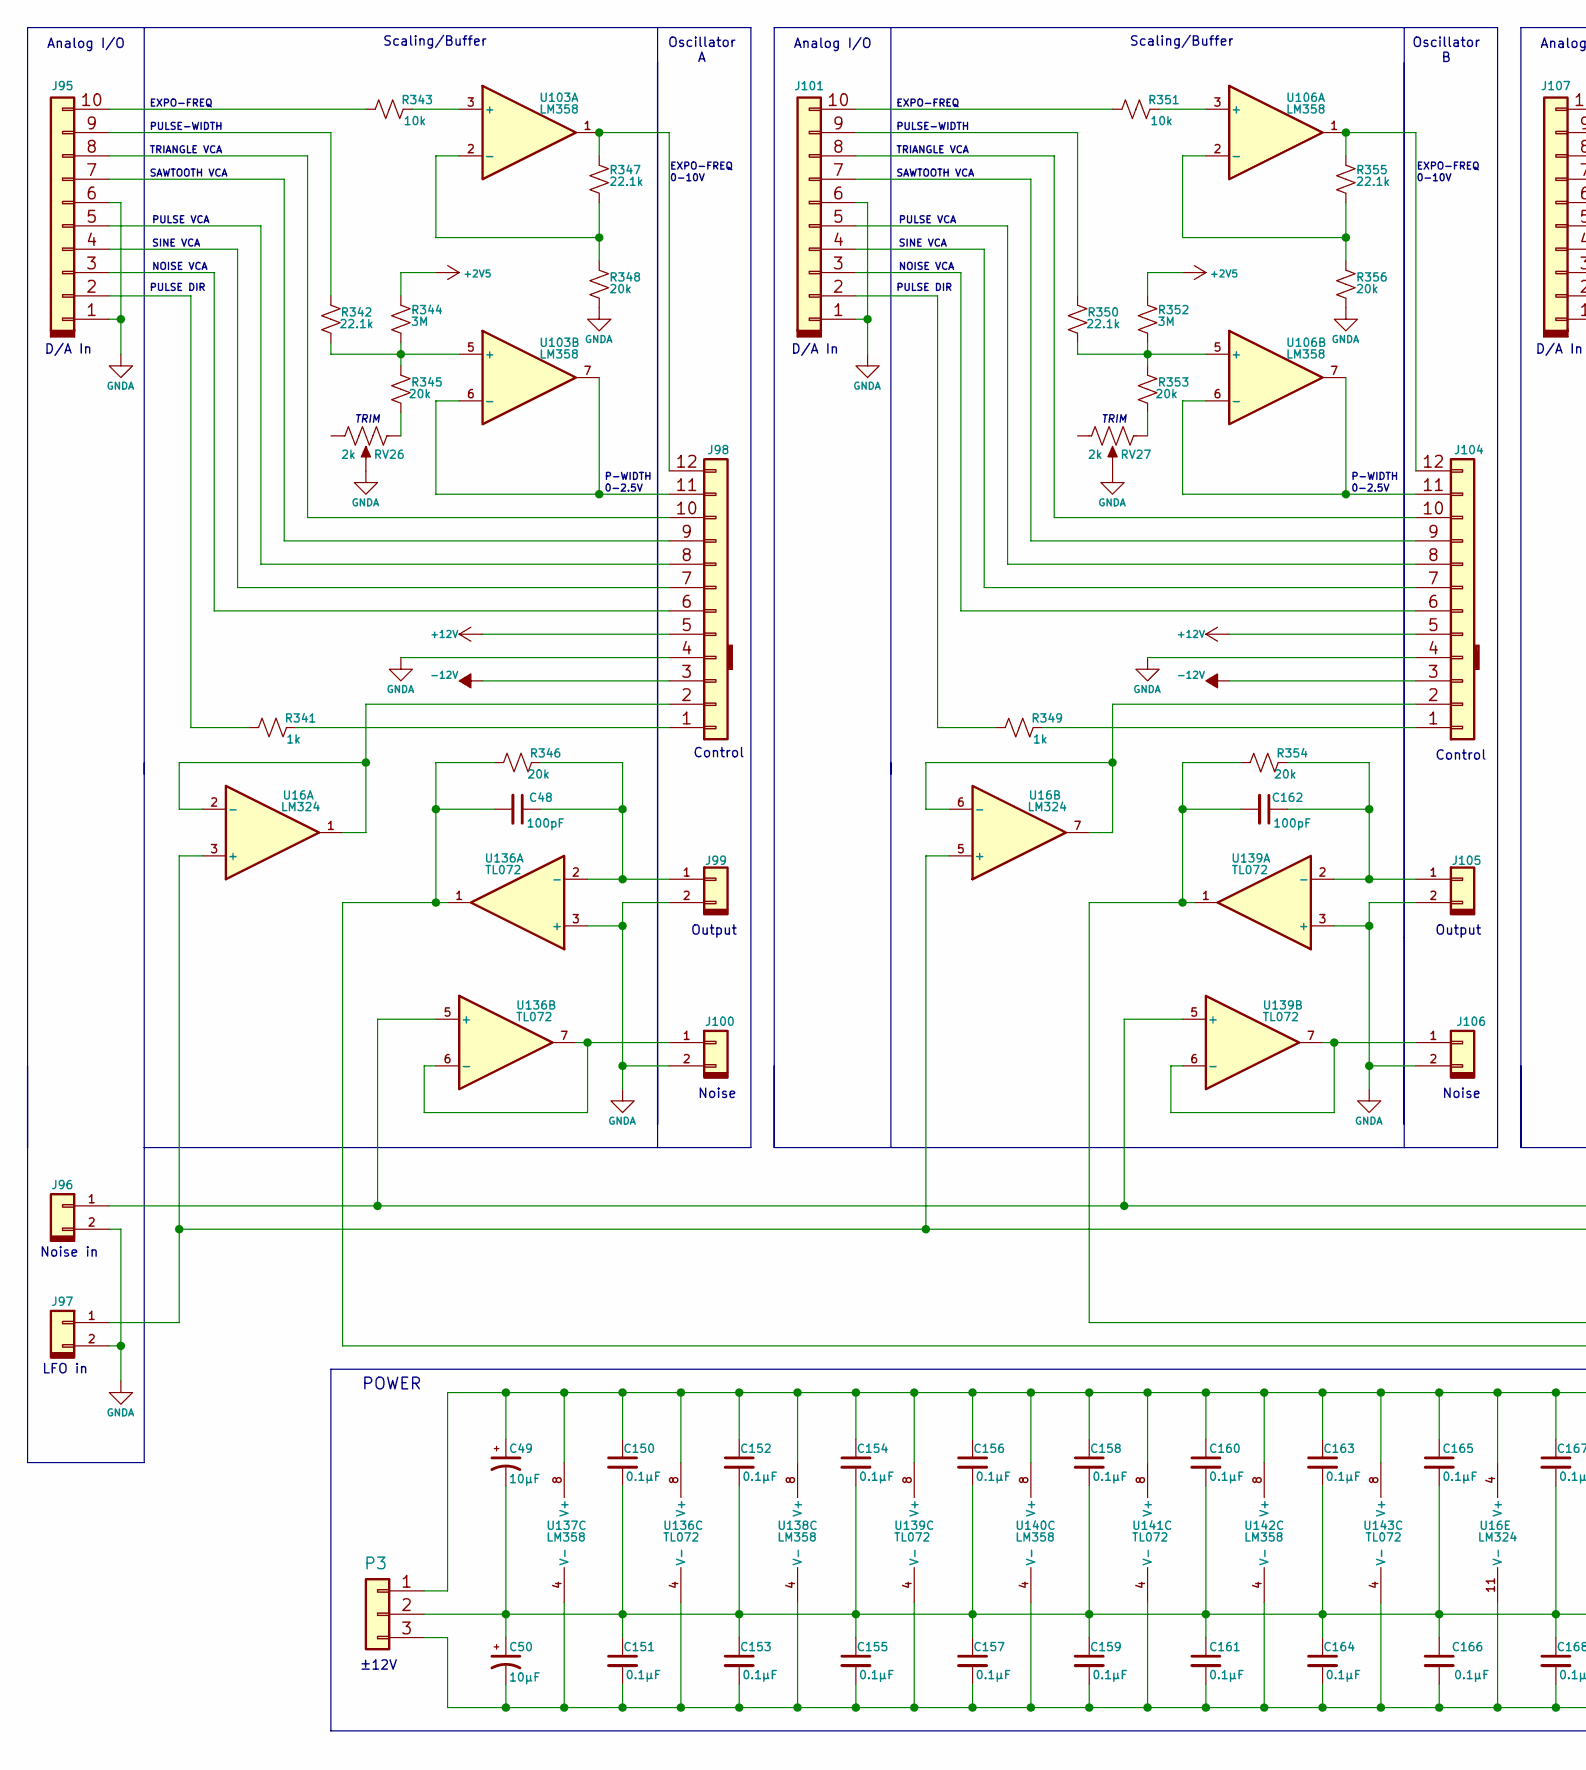
[picture p28: schematic Osc_4_ifc.kicad_sch, part in row 1, column 1]

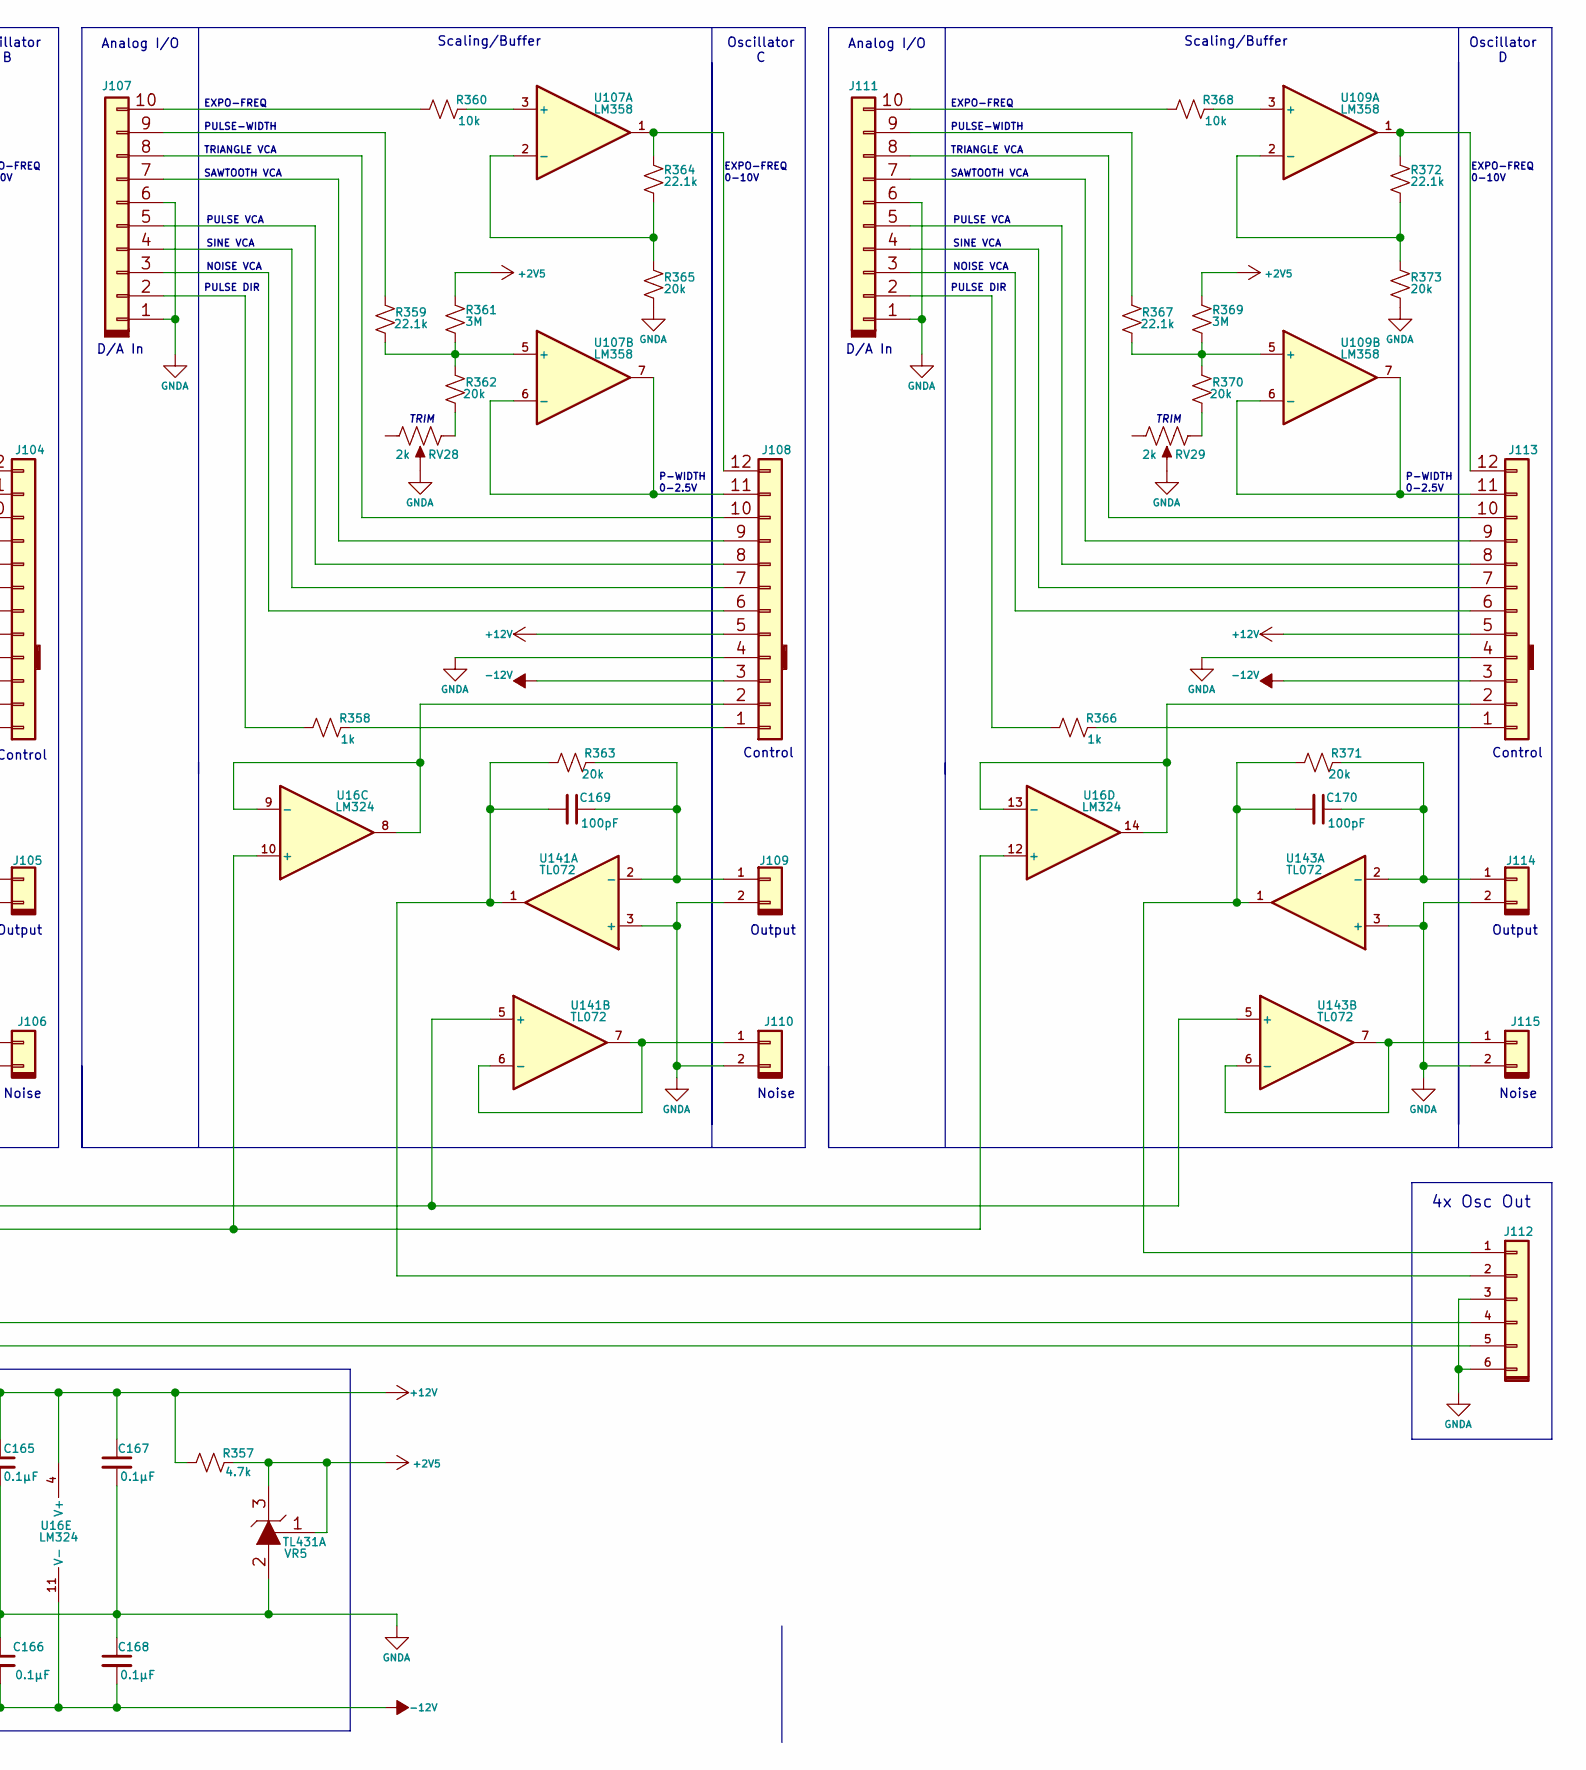
[picture p29: schematic Osc_4_ifc.kicad_sch, part in row 1, column 2]

Parts:
C48, C162, C169, C170: 100pF
C49, C50: 10µF
C150, C151, C152, C153, C154, C155, C156, C157, C158, C159, C160, C161, C163, C164, C165, C166, C167, C168: 0.1µF
J95, J101, J107, J111: Conn_01x10h
J96, J97, J99, J100, J105, J106, J109, J110, J114, J115: Conn_01x02
J98, J104, J108, J113: Conn_01x12
J112: Conn_01x06
P3: Conn_01x03
R341, R349, R358, R366: 1k
R342, R347, R350, R355, R359, R364, R367, R372: 22.1k
R343, R351, R360, R368: 10k
R344, R352, R361, R369: 3M
R345, R346, R348, R353, R354, R356, R362, R363, R365, R370, R371, R373: 20k
R357: 4.7k
RV26, RV27, RV28, RV29: 2k
U16: LM324
U103, U106, U107, U109, U137, U138, U140, U142: LM358
U136, U139, U141, U143: TL072
VR5: TL431A; TO-92-3_Formed_Leads; MPN TL431CLPM; Digi-Key_PN 296-26717-1-ND

Connections:
+2V5: R344.1, R352.1, R357.2, R361.1, R369.1, VR5.1 (REF), VR5.3 (K)
+12V: C49.1, C150.1, C152.1, C154.1, C156.1, C158.1, C160.1, C163.1, C165.1, C167.1, J98.5, J104.5, J108.5, J113.5, P3.1, R357.1, U16.4 (V+), U136.8 (V+), U137.8 (V+), U138.8 (V+), U139.8 (V+), U140.8 (V+), U141.8 (V+), U142.8 (V+), U143.8 (V+)
-12V: C50.2, C151.2, C153.2, C155.2, C157.2, C159.2, C161.2, C164.2, C166.2, C168.2, J98.3, J104.3, J108.3, J113.3, P3.3, U16.11 (V-), U136.4 (V-), U137.4 (V-), U138.4 (V-), U139.4 (V-), U140.4 (V-), U141.4 (V-), U142.4 (V-), U143.4 (V-)
GNDA: C49.2, C50.1, C150.2, C151.1, C152.2, C153.1, C154.2, C155.1, C156.2, C157.1, C158.2, C159.1, C160.2, C161.1, C163.2, C164.1, C165.2, C166.1, C167.2, C168.1, J95.1, J95.6, J96.2, J97.2, J98.4, J99.2, J100.2, J101.1, J101.6, J104.4, J105.2, J106.2, J107.1, J107.6, J108.4, J109.2, J110.2, J111.1, J111.6, J112.3, J112.6, J113.4, J114.2, J115.2, P3.2, R348.2, R356.2, R365.2, R373.2, RV26., RV27., RV28., RV29., U136.3 (+), U139.3 (+), U141.3 (+), U143.3 (+), VR5.2 (A)
unnamed: C48.1, J99.1, R346.2, U136.2 (-)
unnamed: C48.2, J112.5, R346.1, U136.1
unnamed: C162.1, J105.1, R354.2, U139.2 (-)
unnamed: C162.2, J112.4, R354.1, U139.1
unnamed: C169.1, J109.1, R363.2, U141.2 (-)
unnamed: C169.2, J112.2, R363.1, U141.1
unnamed: C170.1, J114.1, R371.2, U143.2 (-)
unnamed: C170.2, J112.1, R371.1, U143.1
unnamed: J95.2, R341.1
unnamed: J95.3, J98.6
unnamed: J95.4, J98.7
unnamed: J95.5, J98.8
unnamed: J95.7, J98.9
unnamed: J95.8, J98.10
unnamed: J95.9, R342.1
unnamed: J95.10, R343.1
unnamed: J96.1, U136.5 (+), U139.5 (+), U141.5 (+), U143.5 (+)
unnamed: J97.1, U16.3 (+), U16.5 (+), U16.10 (+), U16.12 (+)
unnamed: J98.1, R341.2
unnamed: J98.2, U16.1, U16.2 (-)
unnamed: J98.11, U103.6 (-), U103.7
unnamed: J98.12, R347.1, U103.1
unnamed: J100.1, U136.6 (-), U136.7
unnamed: J101.2, R349.1
unnamed: J101.3, J104.6
unnamed: J101.4, J104.7
unnamed: J101.5, J104.8
unnamed: J101.7, J104.9
unnamed: J101.8, J104.10
unnamed: J101.9, R350.1
unnamed: J101.10, R351.1
unnamed: J104.1, R349.2
unnamed: J104.2, U16.6 (-), U16.7
unnamed: J104.11, U106.6 (-), U106.7
unnamed: J104.12, R355.1, U106.1
unnamed: J106.1, U139.6 (-), U139.7
unnamed: J107.2, R358.1
unnamed: J107.3, J108.6
unnamed: J107.4, J108.7
unnamed: J107.5, J108.8
unnamed: J107.7, J108.9
unnamed: J107.8, J108.10
unnamed: J107.9, R359.1
unnamed: J107.10, R360.1
unnamed: J108.1, R358.2
unnamed: J108.2, U16.8, U16.9 (-)
unnamed: J108.11, U107.6 (-), U107.7
unnamed: J108.12, R364.1, U107.1
unnamed: J110.1, U141.6 (-), U141.7
unnamed: J111.2, R366.1
unnamed: J111.3, J113.6
unnamed: J111.4, J113.7
unnamed: J111.5, J113.8
unnamed: J111.7, J113.9
unnamed: J111.8, J113.10
unnamed: J111.9, R367.1
unnamed: J111.10, R368.1
unnamed: J113.1, R366.2
unnamed: J113.2, U16.13 (-), U16.14
unnamed: J113.11, U109.6 (-), U109.7
unnamed: J113.12, R372.1, U109.1
unnamed: J115.1, U143.6 (-), U143.7
unnamed: R342.2, R344.2, R345.1, U103.5 (+)
unnamed: R343.2, U103.3 (+)
unnamed: R345.2, RV26.
unnamed: R347.2, R348.1, U103.2 (-)
unnamed: R350.2, R352.2, R353.1, U106.5 (+)
unnamed: R351.2, U106.3 (+)
unnamed: R353.2, RV27.
unnamed: R355.2, R356.1, U106.2 (-)
unnamed: R359.2, R361.2, R362.1, U107.5 (+)
unnamed: R360.2, U107.3 (+)
unnamed: R362.2, RV28.
unnamed: R364.2, R365.1, U107.2 (-)
unnamed: R367.2, R369.2, R370.1, U109.5 (+)
unnamed: R368.2, U109.3 (+)
unnamed: R370.2, RV29.
unnamed: R372.2, R373.1, U109.2 (-)

Notes on the sheet:
Analog I/O
_{TRIM}
Oscillator C
PULSE VCA
Noise
EXPO-FREQ
4x Osc Out
Control
Output
Scaling/Buffer
PULSE DIR
SAWTOOTH VCA
0-10V
PULSE-WIDTH
0-2.5V
D/A In
POWER
±12V
P-WIDTH
NOISE VCA
TRIANGLE VCA
LFO in
SINE VCA
Oscillator A
Oscillator B
Oscillator D
Noise in
