markeby/Synth32/Schematics/SpareBoards/OsccMix.kicad_sch

## KiCad design Schematics/SpareBoards/OsccMix.kicad_sch (2023-11-05)

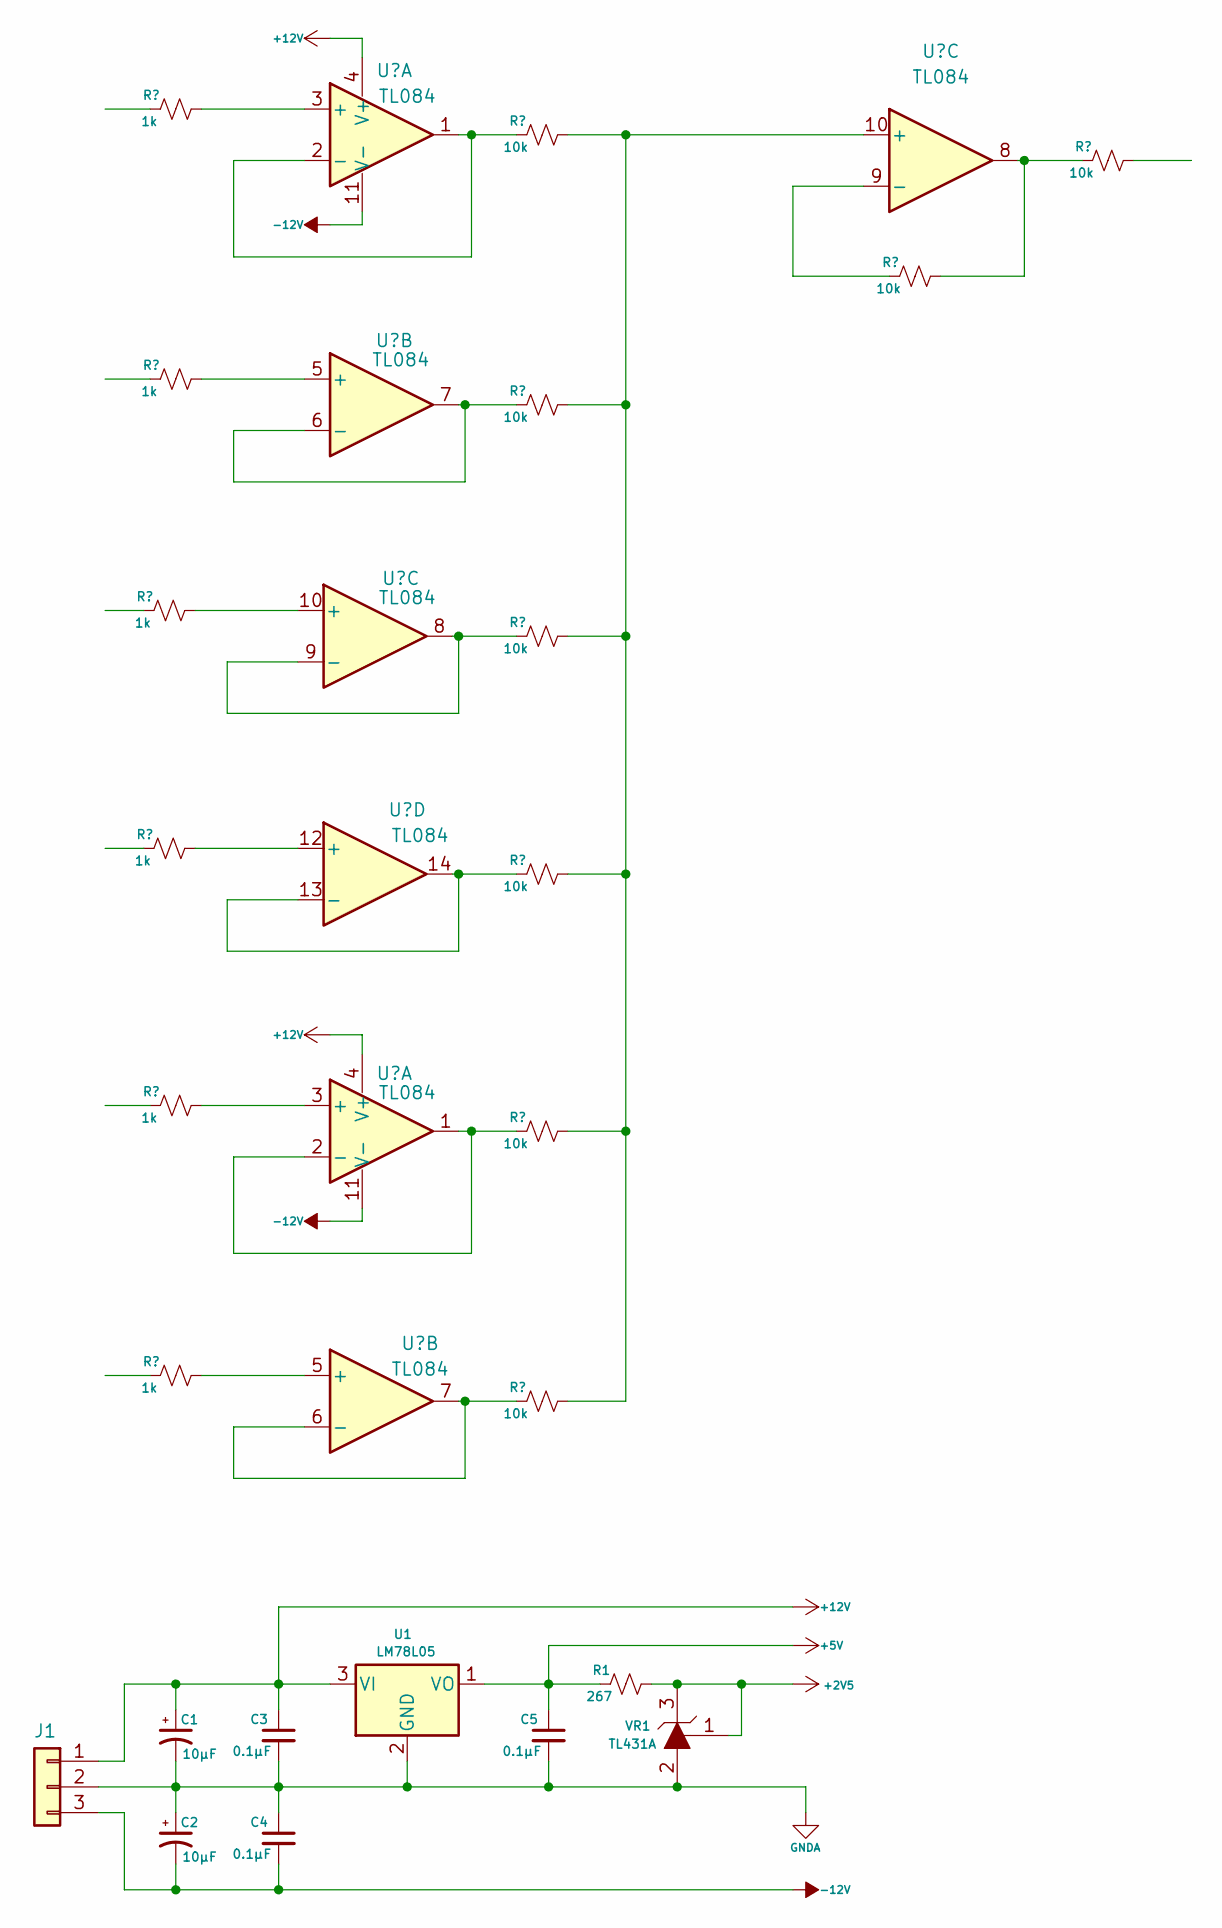
[picture p30: schematic OsccMix.kicad_sch]

Parts:
C1, C2: 10µF
C3, C4, C5: 0.1µF
J1: Conn_01x03
R1: 267
U1: LM78L05; TO-92_Inline
VR1: TL431A; TO-92-3_Formed_Leads; MPN TL431CLPM; Digi-Key_PN 296-26717-1-ND

Connections:
+2V5: R1.2, VR1.1 (REF), VR1.3 (K)
+5V: C5.1, R1.1, U1.1 (VO)
+12V: C1.1, C3.1, J1.1, U1.3 (VI)
-12V: C2.2, C4.2, J1.3
GNDA: C1.2, C2.1, C3.2, C4.1, C5.2, J1.2, U1.2 (GND), VR1.2 (A)
