markeby/Synth32/Midi32/Envelope.cpp

//#######################################################################
// Module:     Envelope.cpp
// Descrption: Envelope processor
// Creator:    markeby
// Date:       6/25/2024
//#######################################################################
#include <Arduino.h>
#include "config.h"
#include "Envelope.h"
#include "SoftLFO.h"

using namespace std;

#include "Debug.h"

#ifdef DEBUG_ON
static const char* Label = "ENV";
#define DBG(args...)  {if (DebugSynth){DebugMsgF(Label,Index,Name,StateLabel[(int)State],args); } }
#else
#define DBG(args...)
#endif

char* StateLabel[] = { "IDLE", "START", "ATTACK", "DECAY", "SUSTAIN", "RELEASE" };
#define TIME_THRESHOLD  10.0

//#######################################################################
ENVELOPE_GENERATOR_C::ENVELOPE_GENERATOR_C ()
    {
    }

//#######################################################################
ENVELOPE_C* ENVELOPE_GENERATOR_C::NewADSR (uint8_t index, String name, uint16_t device, uint8_t& usecount)
    {
    ENVELOPE_C adsl (index, name, device, usecount);
    Envelopes.push_back (adsl);
    return (&(Envelopes.back ()));
    }

//#######################################################################
void ENVELOPE_GENERATOR_C::Loop ()
    {
    for ( deque<ENVELOPE_C>::iterator it = Envelopes.begin ();  it != Envelopes.end();  ++it )
        {
        it->Process (DeltaTimeMilli);
        it->Update ();
        }
    }

//#######################################################################
void ENVELOPE_C::SetRange (int16_t floor, int16_t ceiling)
    {
    this->Floor = floor;
    this->Diff  = ceiling - floor;
    }

//#######################################################################
ENVELOPE_C::ENVELOPE_C (uint8_t index, String name, uint16_t device, uint8_t& usecount) : UseCount(usecount)
    {
    this->Name          = name;
    this->DeviceChannel = device;
    this->Index         = index;
    this->Current       = 0;
    this->Peak          = 0;
    this->Sustain       = 0;
    this->AttackTime    = 0;
    this->DecayTime     = 0;
    this->SustainTime   = 0;
    this->ReleaseTime   = 0;
    this->UseSoftLFO    = false;
    this->SetRange (0, DA_MAX);        // Defualt to normal D/A converter settings
    this->Clear    ();
    }

//#######################################################################
void ENVELOPE_C::SetTime (ESTATE state, float time)
    {
    switch (state )
        {
        case ESTATE::ATTACK:
            this->AttackTime = time;
            break;
        case ESTATE::DECAY:
            this->DecayTime = time;
            break;
        case ESTATE::SUSTAIN:
            this->SustainTime = time;
            break;
        case ESTATE::RELEASE:
            this->ReleaseTime = time;
            break;
        }
    DBG ("%s - Time setting > %f mSec", StateLabel[(int)state], time );
    }

//#######################################################################
float ENVELOPE_C::GetTime (ESTATE state)
    {
    float val = 0.0;

    switch (state )
        {
        case ESTATE::ATTACK:
            val = this->AttackTime;
            break;
        case ESTATE::DECAY:
            val = this->DecayTime;
            break;
        case ESTATE::SUSTAIN:
            val = this->SustainTime;
            break;
        case ESTATE::RELEASE:
            val = this->ReleaseTime;
            break;
        }
    return (val);
    }

//#######################################################################
void ENVELOPE_C::SetLevel (ESTATE state, float percent)
    {
    switch ( state )
        {
        case ESTATE::START:
            break;
        case ESTATE::ATTACK:
            this->Peak = percent;
            break;
        case ESTATE::DECAY:
            this->Sustain = percent;
            break;
        case ESTATE::SUSTAIN:
            this->Sustain = percent;
            break;
        case ESTATE::RELEASE:
            break;
        }
    DBG ("setting %s > %f", StateLabel[(int)state], percent );
    }

//#######################################################################
float ENVELOPE_C::GetLevel (ESTATE state)
    {
    float val = 0.0;

    switch ( state )
        {
        case ESTATE::START:
            break;
        case ESTATE::ATTACK:
            val = this->Peak;
            break;
        case ESTATE::DECAY:
            val = this->Sustain;
            break;
        case ESTATE::SUSTAIN:
            val = this->Sustain;
            break;
        case ESTATE::RELEASE:
            break;
        }
    return (val);
    }

//#######################################################################
void ENVELOPE_C::Start ()
    {
    if ( this->Active || (this->Peak == 0.0) )
        return;
    this->Active = true;
    this->State = ESTATE::START;
    this->UseCount++;
    DBG ("starting %d", this->Index);
    }

//#######################################################################
void ENVELOPE_C::End ()
    {
    if ( !this->Active )
        return;
    this->TriggerEnd = true;
    this->State = ESTATE::IDLE;
    }

//#######################################################################
void ENVELOPE_C::Clear ()
    {
    if ( this->Active && this->UseCount )   this->UseCount--;
    this->Active        = false;
    this->TriggerEnd    = false;
    this->State         = ESTATE::IDLE;
    this->Current       = 0.0;
    this->Updated       = true;
    DBG ("clearing %d", Index);
    this->Update ();
    }

//#######################################################################
void ENVELOPE_C::Update ()
    {
    float output;

    if ( this->Updated )
        {
        if ( this->Current > this->Peak )
            this->Current = this->Peak;

        output = this->Current * this->Multiplier;
        if ( this->UseSoftLFO && (output > 0.05) )
            output += SoftLFO.GetSin ();

        int16_t z = abs(this->Floor + (this->Diff * output));
        I2cDevices.D2Analog (this->DeviceChannel, z);
        this->Updated = false;
        }
    }

//#######################################################################
//#######################################################################
void ENVELOPE_C::Process (float deltaTime)
    {
    if ( !this->Active )                      // if we ain't doing it then we don't need to run this.
        return;

    if ( this->UseSoftLFO )
        this->Updated = true;

    //***************************************
    //  Beginning of the end
    //***************************************
    if ( this->TriggerEnd && (this->State != ESTATE::RELEASE) )
        {
        this->State     = ESTATE::RELEASE;
        this->Timer     = this->ReleaseTime;
        this->ReleaseSt = this->Current;
        DBG ("Terminating");
        return;
        }

    switch ( this->State )
        {
        //***************************************
        //  Start envelope
        //***************************************
        case ESTATE::START:
            {
            this->Current     = 0.0;
            this->Timer       = 0.0;
            this->PeakLevel   = false;
            this->TargetTime  = this->AttackTime - TIME_THRESHOLD;
            this->State       = ESTATE::ATTACK;
            DBG ("Start attact to %f mSec from level %f to %f", TargetTime, Current, Peak);
            return;
            }
        //***************************************
        //  ATTACK
        //***************************************
        case ESTATE::ATTACK:
            {
            if ( Timer < TargetTime )
                {
                Timer  += deltaTime;
                Current  = (Timer / TargetTime) * Peak;
                Updated = true;
                DBG ("Timer > %f mSec at level %f", Timer, Current);
                return;
                }
            Current     = Peak;
            Updated     = true;
            Timer       = DecayTime - TIME_THRESHOLD;;
            State       = ESTATE::DECAY;
            Target      = Peak - Sustain;
            TargetTime  = 0.0;
            DBG ("Start > %f  mSec from level %f to %f", Timer, Current, Sustain);
            return;
            }

        //***************************************
        //  DECAY
        //***************************************
        case ESTATE::DECAY:
            {
            if ( Timer > 10 )
                {
                Timer -= deltaTime;
                Current = Sustain + ((Timer / DecayTime) * Target);
                Updated = true;
                DBG ("Timer > %f mSec at level %f", Timer, Current);
                return;
                }
            Current = Sustain;
            Updated = true;
            Timer   = SustainTime - TIME_THRESHOLD;
            State   = ESTATE::SUSTAIN;
            if ( Sustain >= Peak )
                PeakLevel = true;

            if ( DebugSynth )
                {
                if ( SustainTime < 0 )
                    { DBG ("Staying at level %f", Current); }
                else
                    { DBG ("%f mSec at level %f", Timer, Current); }
                }
            return;
            }
        //***************************************
        //  SUSTAIN
        //***************************************
        case ESTATE::SUSTAIN:
            {
            if ( Timer <= 0 )
                {           // At this level if the max volume is to change, then all volume changes
                if ( PeakLevel )
                    {
                    if ( Current != Peak )
                        {
                        Current = Peak;
                        Updated = true;
                        }
                    }

                return;
                }
            if ( Timer > TIME_THRESHOLD )
                {
                Timer -= deltaTime;
                DBG ("Timer > %f mSec at level %f", Timer, Current);
                return;
                }
            Timer      = ReleaseTime - TIME_THRESHOLD;
            State      = ESTATE::RELEASE;
            ReleaseSt  = Current;
            DBG ("Start > %f  mSec from level %f to 0", Timer, Current);
            return;
            }
        //***************************************
        //  RELEASE
        //***************************************
        case ESTATE::RELEASE:
            {
            TriggerEnd = false;
            if ( Timer > 20)
                {
                Timer  -= deltaTime;
                Current = (Timer / ReleaseTime) * ReleaseSt;
                Updated = true;
                DBG ("Timer > %f mSec at level %f", Timer, Current);
                return;
                }
            Clear ();          // We got to here so this envelope process in finished.
            return;
            }
        }
    //***************************************
    //  This should never happen
    //***************************************
    DBG ("DANGER! DANGER!We should have never gotten here during environment processing!");
    Clear ();
    }
