markeby/Synth32/Midi32/LFOosc.cpp

//#######################################################################
// Module:     LFOusc.cpp
// Descrption: Oscillator controls
// Creator:    markeby
// Date:       9/18/2023
//#######################################################################
#include <Arduino.h>
#include "../Common/SynthCommon.h"
#include "config.h"
#include "I2Cmessages.h"
#include "LFOosc.h"
#include "Debug.h"

#ifdef DEBUG_ON
static const char* Label = "LFO";
#define DBG(args...) {if(DebugOsc){DebugMsg(Label,Number,args);}}
#else
#define DBG(args...)
#endif

#define CONST_MULT      (DA_RANGE / FULL_KEYS)
static  const char*     MixerNames[] = { "sine", "triangle", "saw", "pulse" };

//#######################################################################
SYNTH_LFO_C::SYNTH_LFO_C ()
    {
    Valid         = false;
    UpdateNeded   = false;
    CurrentLevel  = 0;
    }

//#######################################################################
void SYNTH_LFO_C::ClearState ()
    {
    for ( int z = 0;  z < LFO_VCA_COUNT;  z++)
        {
        VCA_T& m = Vca[z];
        I2cDevices.D2Analog (m.Channel, 0);
        }
    }

//#######################################################################
void SYNTH_LFO_C::SetMaxLevel (byte ch, byte data)
    {
    int z = (int)((data * 0.007874) * (float)MAX_DA);
    Vca[ch].MaximumLevel =  (z > MAX_DA ) ? MAX_DA : z;

    DBG ("Level limit > %d", Vca[ch].MaximumLevel);
    }

//#######################################################################
void SYNTH_LFO_C::SetLevel (byte ch, byte data)
    {
    int z = (int)((data * 0.007874) * (float)MAX_DA);
    z = (z > Vca[ch].MaximumLevel ) ? Vca[ch].MaximumLevel : z;

    if ( z != Vca[ch].CurrentLevel )
        {
        Vca[ch].CurrentLevel = z;
        I2cDevices.D2Analog (Vca[ch].Channel,  z);
        UpdateNeded = true;
        DBG ("%s level > %d", Vca[ch].Name, z);
        }
    }

//#######################################################################
//#######################################################################
void SYNTH_LFO_C::Begin (int num, byte first_device)
    {
    Number = num;
    // D/A configuration
    OscChannel = first_device + byte(D_A_OFF::FREQ);
    PwmChannel = first_device + byte(D_A_OFF::WIDTH);
    BendChannel = first_device + byte(D_A_OFF::BEND);
    Vca[int(SHAPE::TRIANGLE)].Channel = first_device + byte(D_A_OFF::TRIANGLE);
    Vca[int(SHAPE::SAWTOOTH)].Channel = first_device + byte(D_A_OFF::SAWTOOTH);
    Vca[int(SHAPE::PULSE)].Channel    = first_device + byte(D_A_OFF::PULSE);
    Vca[int(SHAPE::SINE)].Channel     = first_device + byte(D_A_OFF::SINE);

    // Initialize mixer
    for ( int z = 0;  z < LFO_VCA_COUNT;  z++ )
        {
        Vca[z].Name         = MixerNames[z];
        Vca[z].CurrentLevel = 0;
        Vca[z].MaximumLevel = MAX_DA;
        }

    if ( I2cDevices.IsChannelValid (first_device) && I2cDevices.IsChannelValid (first_device + 7) )
        {
        Valid = true;
        PitchBend (50.0);
        ClearState ();
        if ( DebugOsc )
            printf("\t  >> LFO %d started for device %d\n", Number, first_device);
        }
    else
        printf("\t  ** LFO %d NO USABLE D/A CHANNELS FROM DEVICE %d\n", num, first_device);
    }

//#######################################################################
void SYNTH_LFO_C::Clear ()
    {
    ClearState ();
    I2cDevices.UpdateAnalog ();     // Update D/A ports
    }

//#######################################################################
void SYNTH_LFO_C::SetFreq (float percent)
    {
    CurrentPercent = percent;
    int z = CurrentPercent * MAX_DA;
    DBG ("Set frequency %d", z);
    I2cDevices.D2Analog (OscChannel, z);
    I2cDevices.UpdateAnalog ();     // Update D/A ports
    }

//#######################################################################
void SYNTH_LFO_C::Select (byte ch, bool sel)
    {
    Vca[ch].Select = sel;
    if ( sel )
        SetLevel (ch, CurrentLevel);
    else
        SetLevel (ch, 0);

    if ( UpdateNeded )
        {
        I2cDevices.UpdateAnalog ();     // Update D/A ports
        UpdateNeded = false;
        }

    DBG ("%s(%d) selected %s", Vca[ch].Name, ch, ((sel) ? "ON" : "off"));
    }

//#######################################################################
void SYNTH_LFO_C::Level (byte data)
    {
    CurrentLevel = data;
    for (int z = 0;  z < LFO_VCA_COUNT;  z++ )
        {
        if ( Vca[z].Select )
            SetLevel (z, data);
        else
            SetLevel (z, 0);
        }
    if ( UpdateNeded )
        {
        I2cDevices.UpdateAnalog ();     // Update D/A ports
        UpdateNeded = false;
        }
    }

//#######################################################################
void SYNTH_LFO_C::PitchBend (float percent)
    {
    if ( percent < 1.0 )
        percent = 1.0;
    I2cDevices.D2Analog(BendChannel, (percent * 0.01) * (float)MAX_DA);
    I2cDevices.UpdateAnalog ();     // Update D/A ports
    }
