markeby/Synth32/Midi32/Settings.cpp

//#######################################################################
// Module:     Settings.cpp
// Descrption: Load and save settings for system and synth
// Creator:    markeby
// Date:       5/17/2023
//#######################################################################
#include <Arduino.h>
#include <Preferences.h>
#include "Settings.h"
#include "FrontEnd.h"

//#######################################################################
Preferences Prefs;

//#######################################################################
// Preference keys
static const char* sysKeySpace    = "SysP";
static const char* sysKeySSID     = "SSID";
static const char* sysKeyPSWD     = "PASSD";
static const char* sysKeyDBG      = "DBG";

static const char* synthKeySpace  = "SynthP";
static const char* synthKeyBank   = "BANK";

//#######################################################################
void SETTINGS_C::ClearAllSys (void)
    {
    Prefs.begin (sysKeySpace, false);
    Prefs.clear ();
    Prefs.end ();
    }

//#######################################################################
void SETTINGS_C::PutSSID (String& str)
    {
    Prefs.begin (sysKeySpace, false);
    Prefs.putString (sysKeySSID, str);
    s_SSID = str;
    Prefs.end ();
    }

//#######################################################################
void SETTINGS_C::PutPasswd (String& str)
    {
    Prefs.begin (sysKeySpace, false);
    Prefs.putString (sysKeyPSWD, str);
    s_PSWD = str;
    Prefs.end ();
    }

//#######################################################################
void SETTINGS_C::PutDebugSwitch (byte num, bool state)
    {
    char buf[8];

    sprintf (buf, "%s%d", sysKeyDBG, num);
    Prefs.begin(sysKeySpace, false);
    Prefs.putBool ((const char *)buf, state);
    Prefs.end ();
    }

//#######################################################################
bool SETTINGS_C::GetDebugSwitch (byte num)
    {
    char buf[8];

    sprintf (buf, "%s%d", sysKeyDBG, num);
    Prefs.begin (sysKeySpace, false);
    if (  !Prefs.isKey ((const char *)buf) )
        this->DebugFlags = false;
    bool zb = Prefs.getBool ((const char *)buf);
    Prefs.end ();
    return (zb);
    }

//#######################################################################
void SETTINGS_C::SaveDebugFlags ()
    {
    this->PutDebugSwitch (0, DebugMidi);
    this->PutDebugSwitch (1, DebugI2C);
    this->PutDebugSwitch (2, DebugOsc);
    this->PutDebugSwitch (3, DebugSynth);
    this->PutDebugSwitch (4, DebugDisp);
    }

//#######################################################################
void SETTINGS_C::RestoreDebugFlags ()
    {
    this->DebugFlags = true;
    DebugMidi   = this->GetDebugSwitch (0);
    DebugI2C    = this->GetDebugSwitch (1);
    DebugOsc    = this->GetDebugSwitch (2);
    DebugSynth  = this->GetDebugSwitch (3);
    DebugDisp   = this->GetDebugSwitch (4);
    if ( this->DebugFlags )
        printf ("\t>>> Debug setup.\n");
    else
        printf ("\t  **** Debug flags failed to load\n");
    }

//#######################################################################
SETTINGS_C::SETTINGS_C (void)
    {
    }

//#######################################################################
void SETTINGS_C::Begin (void)
    {
    Prefs.begin (sysKeySpace, false);
        {
        s_SSID = Prefs.getString (sysKeySSID);
        s_PSWD = Prefs.getString (sysKeyPSWD);
        }
    Prefs.end ();
    Settings.RestoreDebugFlags ();
    }

//#######################################################################
//#######################################################################
void SETTINGS_C::ClearAllSynth (void)
    {
    Prefs.begin (synthKeySpace, false);
    Prefs.clear ();
    Prefs.end ();
    }

//#######################################################################
bool SETTINGS_C::GetOscBank (byte num, uint16_t* pbank)
    {
    char buf[8];
    bool exist = true;

    sprintf (buf, "%s%d", synthKeyBank, num);
    Prefs.begin (synthKeySpace, false);
    if (  Prefs.isKey ((const char *)buf) )
        {
        bool zb = Prefs.getBytes((const char *)buf, pbank, FULL_KEYS * sizeof(uint16_t));
        exist = false;
        }
    Prefs.end ();
    return (exist);
    }

//#######################################################################
void SETTINGS_C::PutOscBank (byte num, uint16_t* pbank)
    {
    char buf[8];

    sprintf (buf, "%s%d", synthKeyBank, num);
    Prefs.begin(synthKeySpace, false);
    Prefs.putBytes ((const char *)buf, pbank, FULL_KEYS * sizeof (uint16_t));
    Prefs.end ();
    }

//#######################################################################
SETTINGS_C Settings;        // System settings
