markeby/Synth32/Midi32/Debug.h

//#######################################################################
// Module:     Debug.h
// Descrption: Varialble length debug output
// Creator:    markeby
// Date:       3/17/2024
//#######################################################################
#pragma once

#define DEBUG_ON            1

#define DEBUG_NO_INDEX      255

const String vFormat (const char *const zcFormat, ...);
const String vsFormat (const char *const zcFormat, va_list args);

void DebugMsg  (const char* label, uint8_t index, const char *const fmt, ...);
void DebugMsgN (const char* label, uint8_t index, String name,  const char *const fmt, ...);
void DebugMsgF (const char* label, uint8_t index, String name, char* flag, const char *const fmt, ...);
