markeby/Synth32/Midi32/I2Cmessages.cpp

//#######################################################################
// Module:     SyntFront.ino
// Descrption: Synthesizer front end controller
//                 Midi->Front->SynthModules
// Creator:    markeby
// Date:       5/17/2023
//#######################################################################
#include <Arduino.h>
#include <Wire.h>
#include "config.h"
#include "I2Cmessages.h"
#include "Debug.h"

using namespace DISP_MESSAGE_N;

static const char* LabelD = "D";
#define DBGM(args...) {if(DebugDisp){ DebugMsg(LabelD,DEBUG_NO_INDEX,args);}}

static byte sendBuffer[16];

//#######################################################################
//#######################################################################

I2C_MESSAGE_C::I2C_MESSAGE_C () : Ready (false)
    {
    ResetState = false;
    Paused = false;
    }

//#######################################################################
void I2C_MESSAGE_C::Begin (byte display, byte sda, byte scl)
    {
    pinMode (RESET_STROBE_IO, INPUT);

    memset (sendBuffer, 0, 16);
    this->DisplayAddress = display;
    Wire1.begin (sda, scl, 400000UL);   // Clock at 400kHz
    this->Ready = true;
    }

//###################################################################
void I2C_MESSAGE_C::SendComplete (byte length)
    {
    Wire1.beginTransmission (DisplayAddress);
    int written = Wire1.write ((const byte*)sendBuffer, length);
    Wire1.endTransmission();
    if ( written != length )
        printf("[DISP] ### ERROR ### Attempt to send %d byte message but shows %d", length, written);
    }

//###################################################################
void I2C_MESSAGE_C::Page (PAGE_C page)
    {
    if ( this->Ready )
        {
        sendBuffer[0] = (byte)CMD_C::PAGE_SHOW;
        sendBuffer[1] = 0;
        sendBuffer[2] = (byte)page;
        DBGM ("Page %d", (byte)page);
        SendComplete (MESSAGE_LENGTH_PAGE);
        }
    }

//###################################################################
// CMD_C chan EFFECT_C high low
void I2C_MESSAGE_C::SendUpdate (CMD_C page, byte channel, EFFECT_C effect, uint16_t value)
    {
    if ( this->Ready )
        {
        sendBuffer[0] = (byte)page;
        sendBuffer[1] = channel;
        sendBuffer[2] = (byte)effect;
        sendBuffer[3] = (byte)(value & 0x00FF);
        sendBuffer[4] = (byte)(value >> 8);
        DBGM ("Page: %X  channel: %X   effect: %X   Value: %X", sendBuffer[0], sendBuffer[1], sendBuffer[2], value);
        this->SendComplete (MESSAGE_LENGTH_UPDATE);
        }
    }

//#####################################################################
void I2C_MESSAGE_C::Pause (bool state)
    {
    if ( state )
        sendBuffer[0] = (byte)CMD_C::PAUSE;
    else
        sendBuffer[0] = (byte)CMD_C::GO;
    sendBuffer[1] = 0;
    DBGM ("Command: %d\n", sendBuffer[0]);
    this->SendComplete (MESSAGE_LENGTH_CNTL);
    }

I2C_MESSAGE_C DisplayMessage;
